MR-DOS/TDR_diploma_thesis/LaTeX/images/cml_output-eps-converted-to.pdf

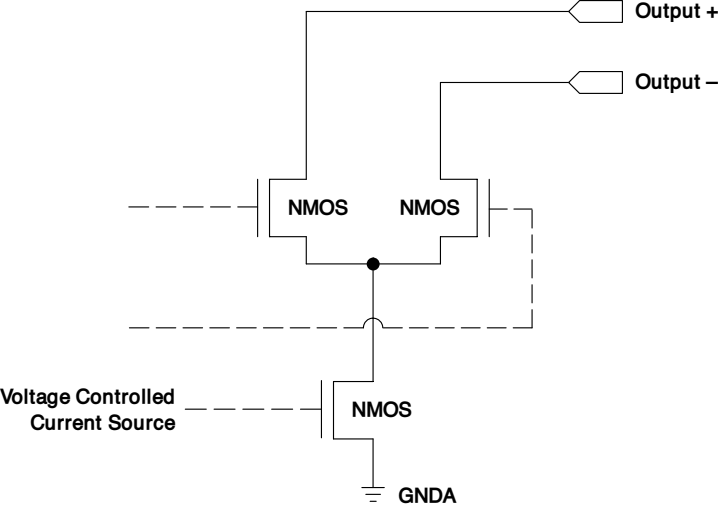
[picture p11: figure]
GNDA; NMOS; Output –; Voltage Controlled Current Source; Output +
