MR-DOS/TDR_diploma_thesis/LaTeX/diplomovy_projekt_4_separace.tex

\chapter{Separace budicího a odraženého signálu}
Pro potřeby zpracování změřených dat je nezbytné separovat budicí signál od jeho odrazů. Takovou separaci je možné provádět buď hardwarově v době měření nebo až během zpracování změřených dat. Cílem je dosáhnout toho, aby byly tyto dva signály zcela oddělené (či oddělitelné při zpracování). Možné metody separace:
\begin{itemize}
	\item
	\textbf{Směrová odbočnice}\\*	
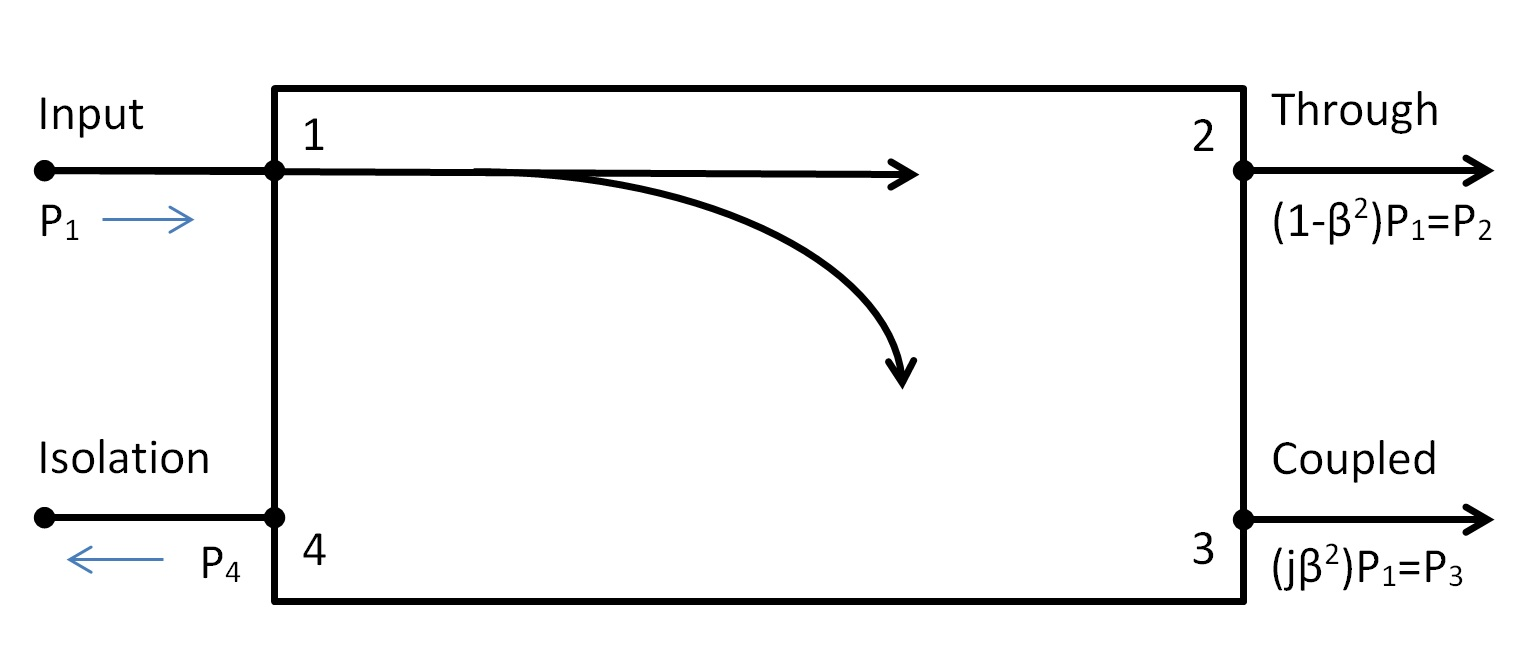
[picture p49: LaTeX/images/directionalcoupler.png]
	\begin{figure}[htbp]\caption{Směrová odbočnice, převzato z \cite{widebandcouplers}.}\label{directionalcoupler}\end{figure}	

	Pomocí tradičních odbočnic jako na obr. \ref{directionalcoupler} je možné provádět separaci s velkou izolací nechtěného signálu, ovšem nesplňují požadavek na šířku zpracovávaného pásma \cite{widebandcouplers}. Problematická je také skutečnost, že s rostoucí šířkou použitelného pásma odbočnice obvykle klesá směrovost odbočnice. Dochází tedy pouze k částečné separaci, další separační krok by byl nezbytný během zpracování naměřených dat.
	
	\item
	\textbf{Odporový můstek}\\*	
	Pomocí odporových můstků je možné provádět separaci signálů s velmi velkou šířkou pásma, např. v \cite{resistivedirectionalbridge} a obr. \ref{resistivebridge} uveden můstek pro pásmo \SI{300}{\kilo\hertz}--\SI{13.5}{\giga\hertz}. Opět je však separace budicího pulzu a odezvy pouze částečná, neboť tento můstek má konečnou směrovost.

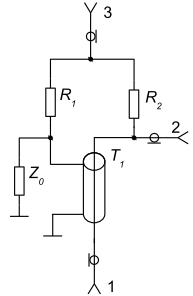
[picture p50: LaTeX/images/resistivebridge.png]
	\begin{figure}[htbp]\caption{Odporový směrový můstek, převzato z \cite{resistivedirectionalbridge}.}\label{resistivebridge}\end{figure}	
	
	\item
	\textbf{Časové oddělení}\\*	
	Pokud má budicí signál tu vlastnost, že má omezenou délku, po kterou se mění a mimo ni je konstantní (vybraný jednotkový skok tuto vlastnost splňuje), je možné jej od odrazů separovat tak, že je časově posunut vůči odezvě systému. Toho je možné dosáhnout například použitím dokonalého vedení bez odrazů, které se zapojí mezi bod měření a měřený systém. Jeho délka musí být minimálně taková, aby se nemohla nikdy překrývat nekonstantní část budicího signálu s odrazy. Pokud je v naměřených datech známá poloha budicího pulzu (nebo je-li možné jej spolehlivě identifikovat), je možné naměřená data rozdělit na část buzení a část odpovědi měřeného systému. První část pak může sloužit ke korekci frekvenční charakteristiky změřené odezvy systému a odhadu šumového spektra. Známe-li i přesnou délku prodlužovacího vedení (hrubě z návrhu zařízení, přesně pomocí kalibrace), je možné provést kalibraci měřicí roviny. Při použití této metody separace stačí vzorkování pouze jednoho průběhu, snižuje tedy počet potřebných vzorkovačů ze dvou (nebo více) na jeden. Z toho také vyplývá, že měřená data nejsou zatížena chybou, která by mohla vzniknout vzhledem k rozdílným vlastnostem jednotlivých vzorkovačů.
	
	Na obrázku \ref{separableunitstep} je znázorněna odezva na chybovou funkci pro \SI{50}{\ohm} zakončené \SI{75}{\ohm} terminátorem. Buzení se nachází v čase $t=\SI{0}{\nano\second}$, odezva v čase $t=\SI{0.5}{\nano\second}$. Průběh budicí funkce je předem známý, nekonstantní část průběhu se nepřekrývá s odezvou, je tedy možné je v časové oblasti $t\in (\SI{0}{\nano\second};\SI{0.5}{\nano\second})$ rozdělit na dva samostatné průběhy.

\begin{figure}[htbp]\caption{Časově oddělitelná odezva na jednotkový skok.}\label{separableunitstep}\end{figure}	
\end{itemize}

Pro vybraný budicí signál (jednotkový skok) je tedy možné provést separaci od odrazů zpožďovacím vedením a vhodným rozdělením naměřených dat na dvě části. Toto řešení se jeví jako obvodově i výpočetně nejjednodušší z uvažovaných metod separace.
