MR-DOS/TDR_diploma_thesis/obhajoba/obhajoba_prezentace_oponent.odp

## Diplomová práce Reflektometr v časové oblasti

ČVUT FEL EK, Elektronika

Petr Polášek

2020-02-01

## Slide 2

Odpovědi na dotazy oponenta

## Slide 3

## Slide 4

## Slide 5

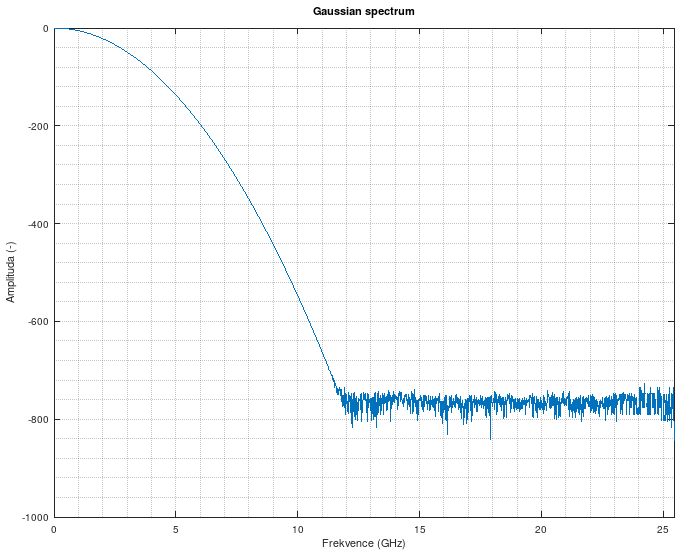
[picture p51: figure]

## Slide 6

## Slide 7

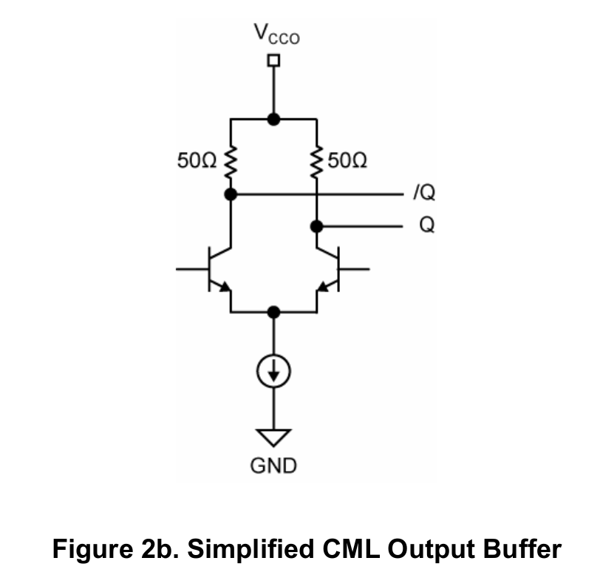
[picture p52: figure]

## Slide 8

+1.6 mW

(+0.8 mW)

+1.6 mW

(+0.8 mW)

## Slide 9

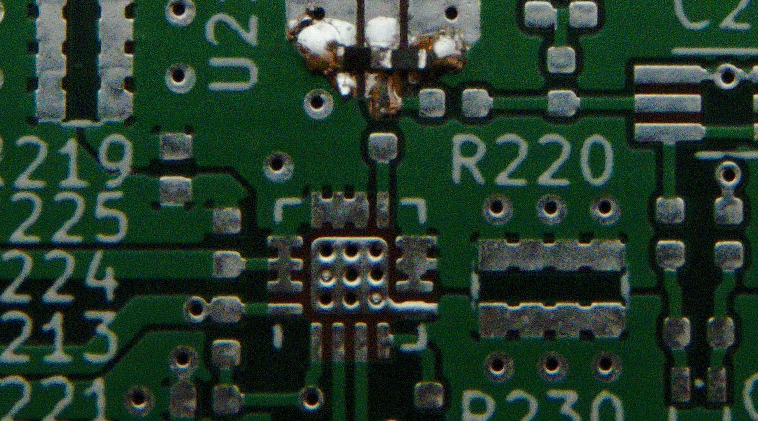
[picture p53: figure]

## Slide 10

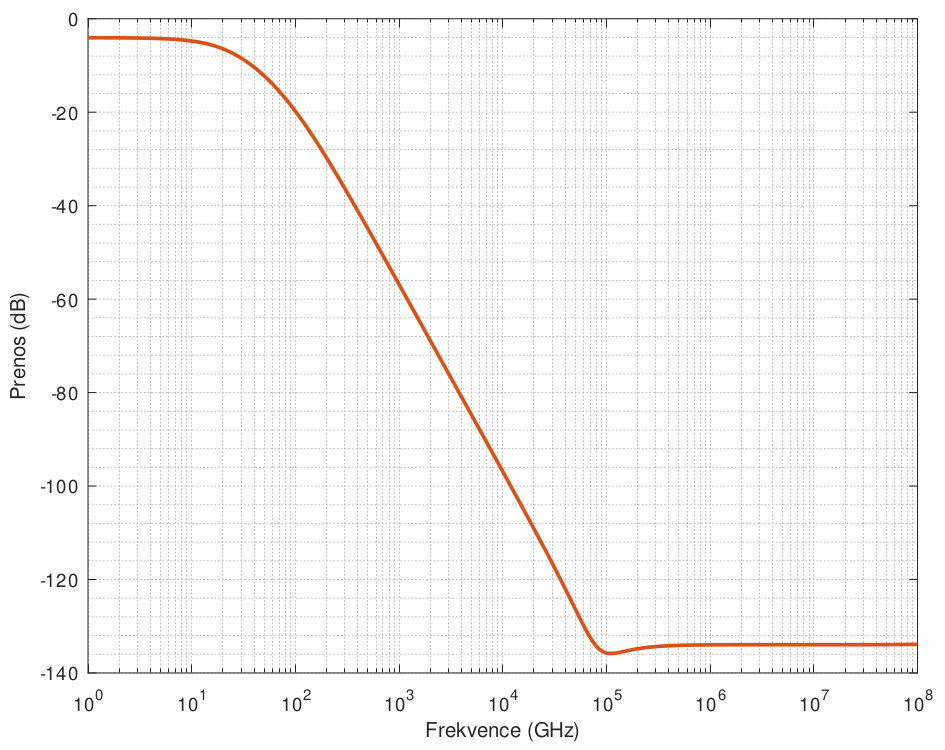
[picture p54: figure]

## Slide 11

## Slide 12

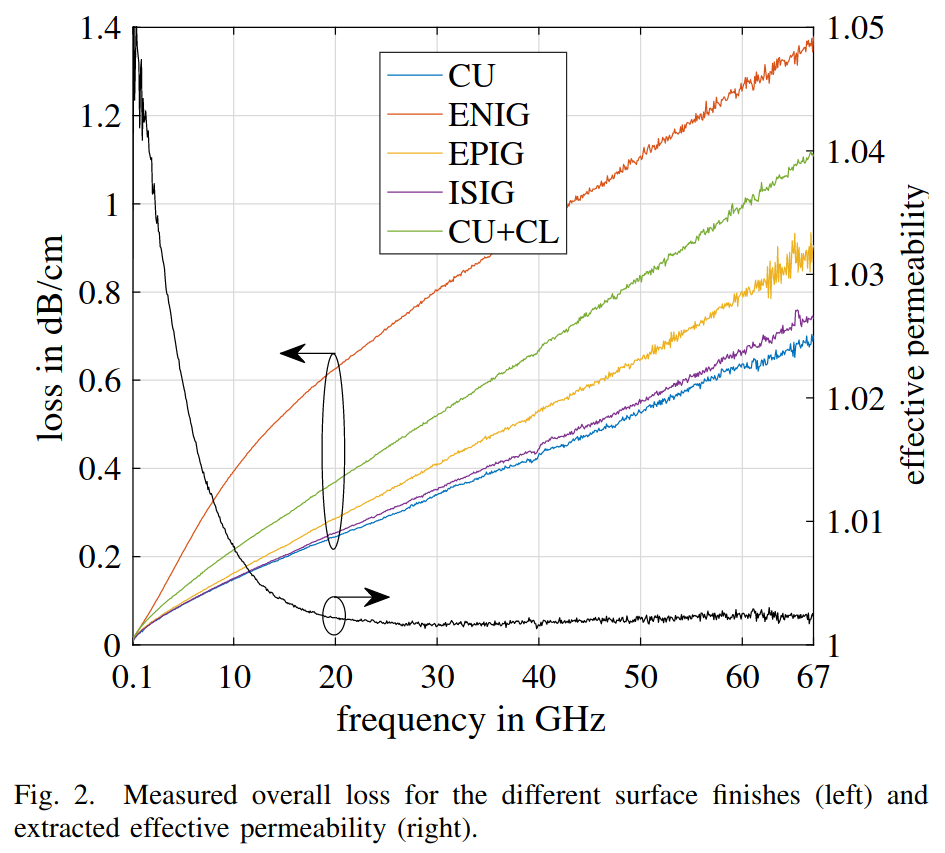
[picture p55: figure]

## Slide 13

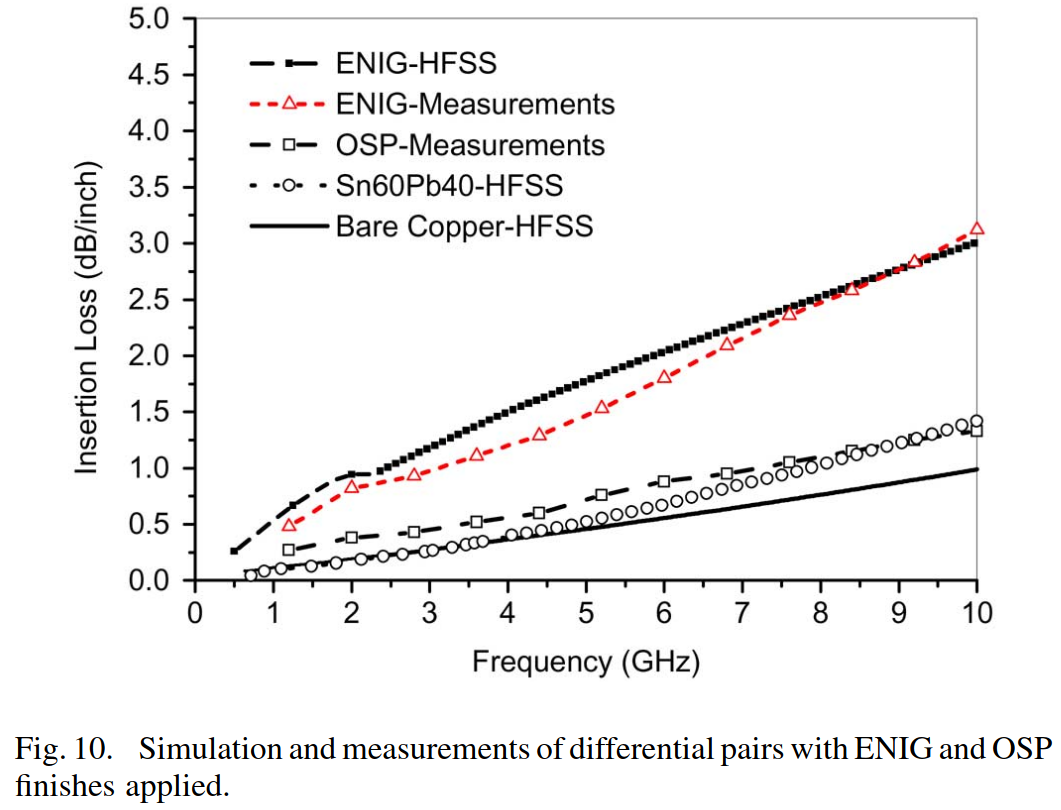
[picture p56: figure]

## Slide 14

## Slide 15

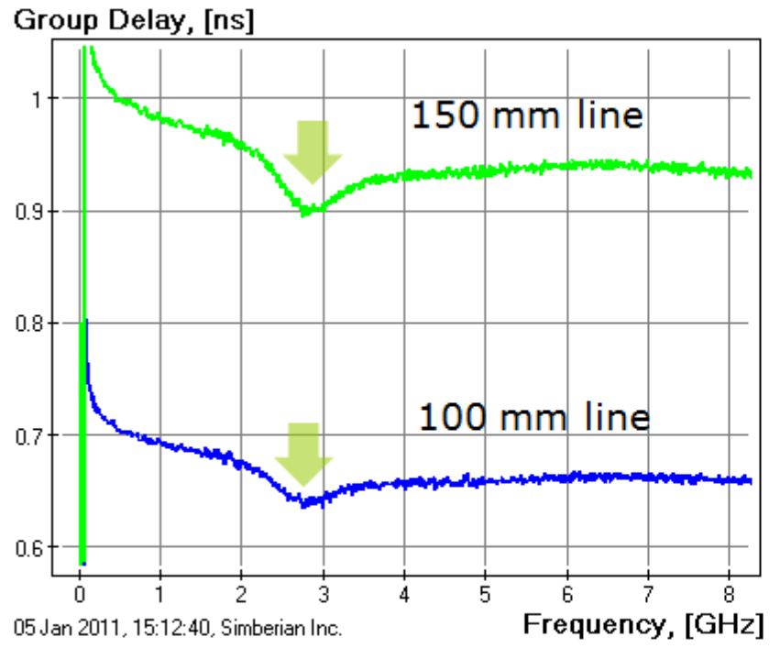
[picture p57: figure]
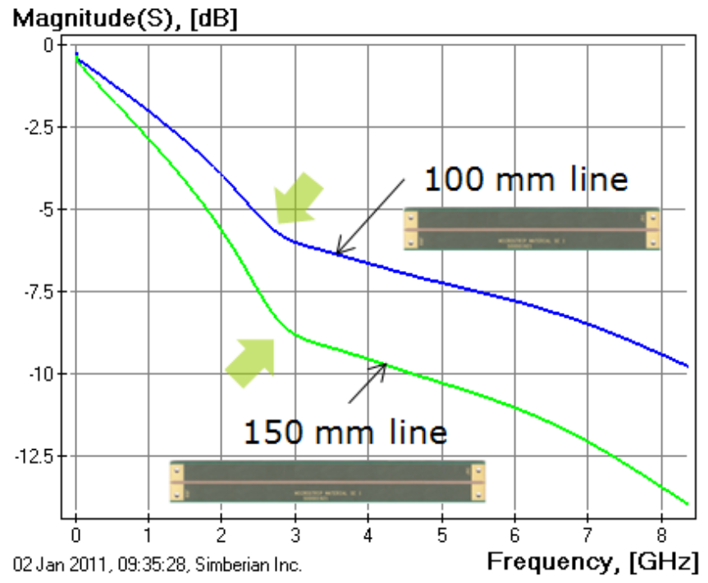
[picture p58: figure]

## Slide 16

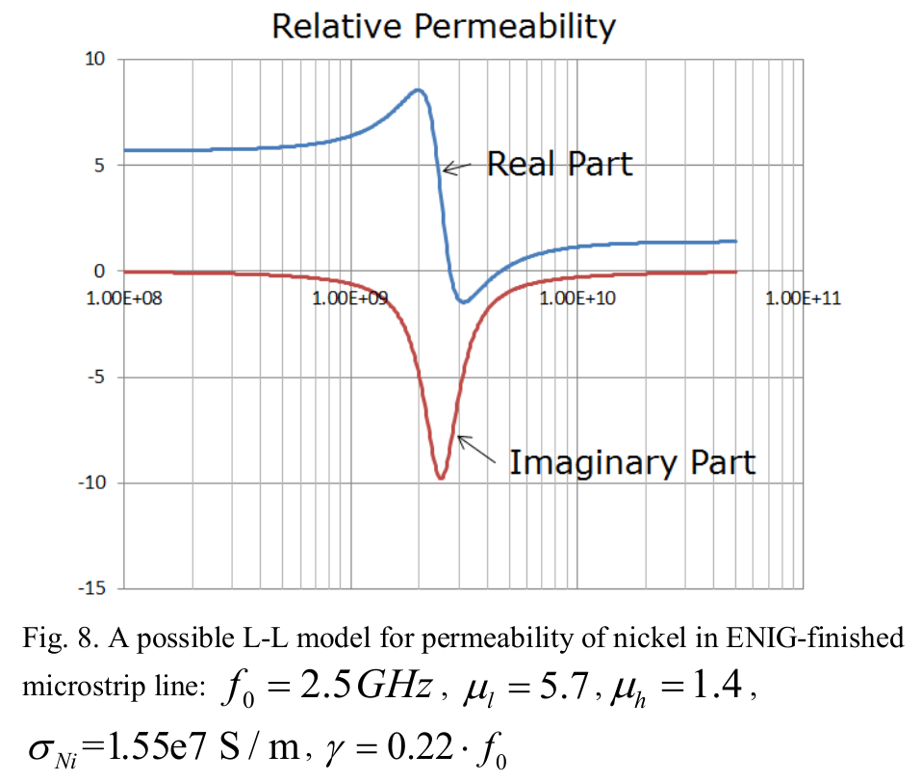
[picture p59: figure]
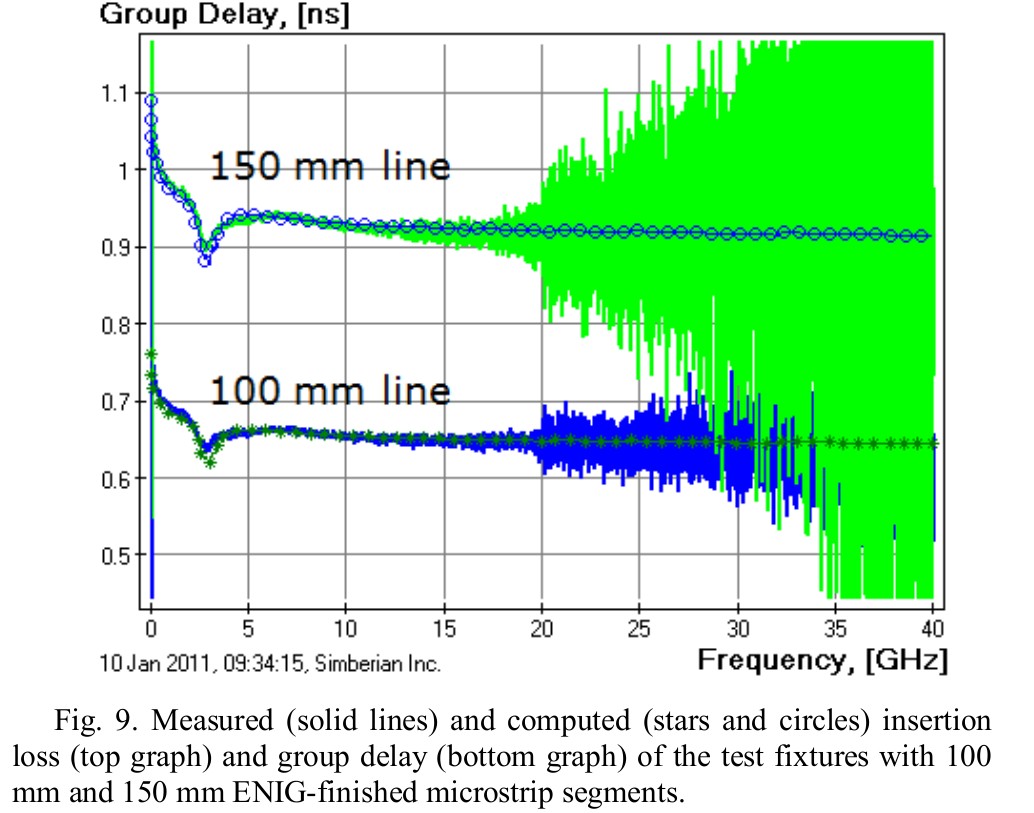
[picture p60: figure]

## Slide 17

## Slide 18

## Slide 19


## Slide 20

## Slide 21

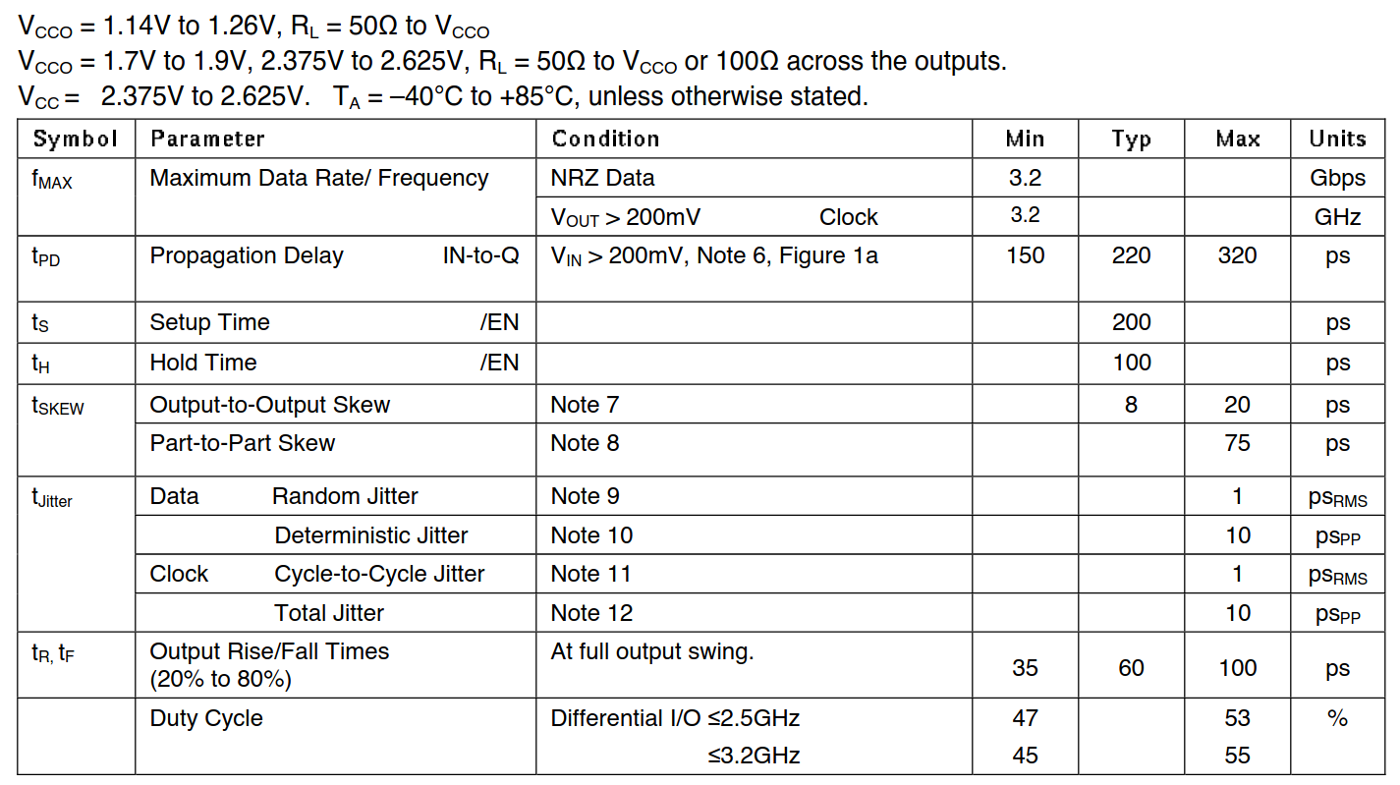
[picture p61: figure]

## Slide 22

## Slide 23

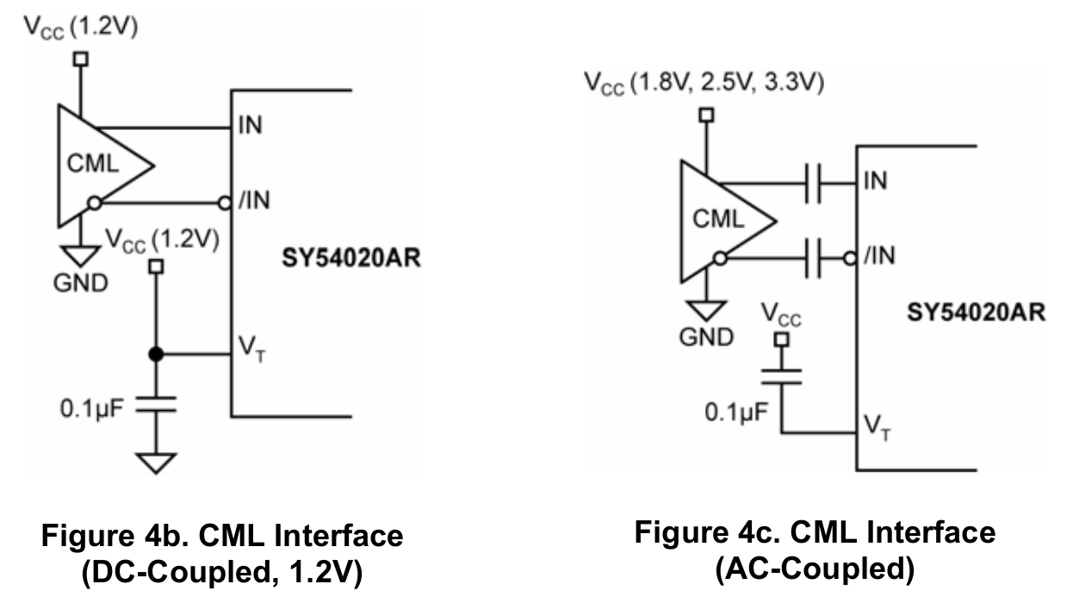
[picture p62: figure]

## Slide 24

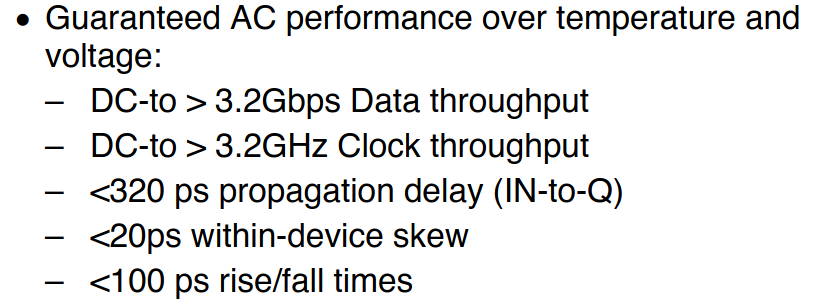
[picture p63: figure]

## Slide 25

## Slide 26

## Slide 27

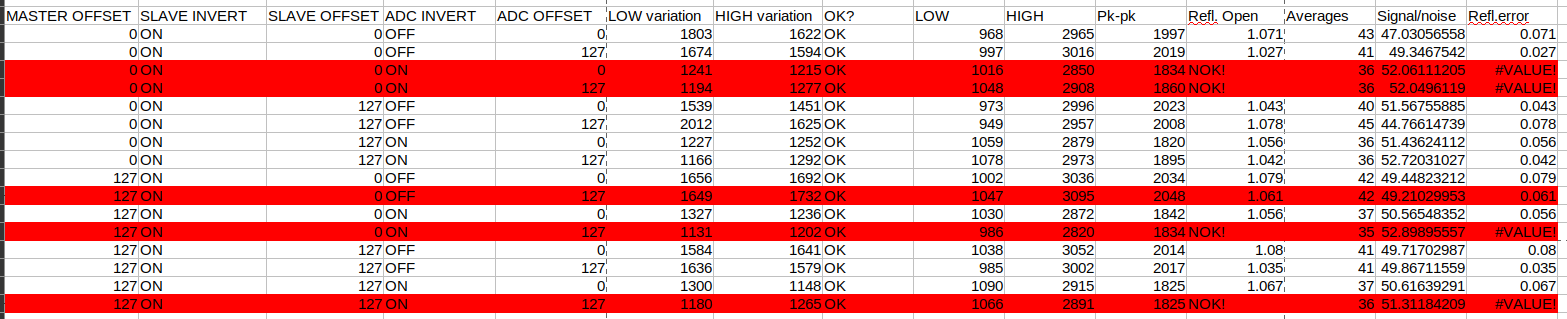
[picture p64: figure]

## Slide 28

## Slide 29

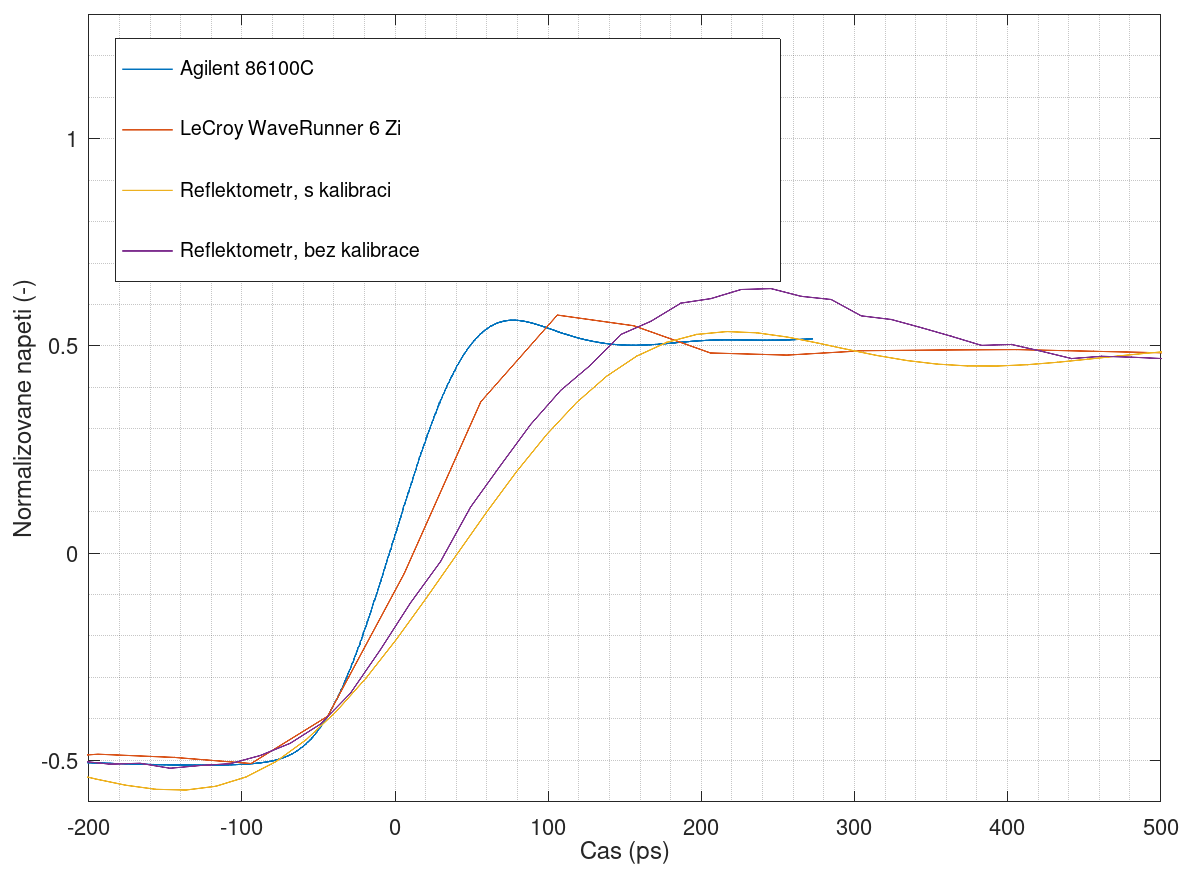
[picture p65: figure]

## Slide 30

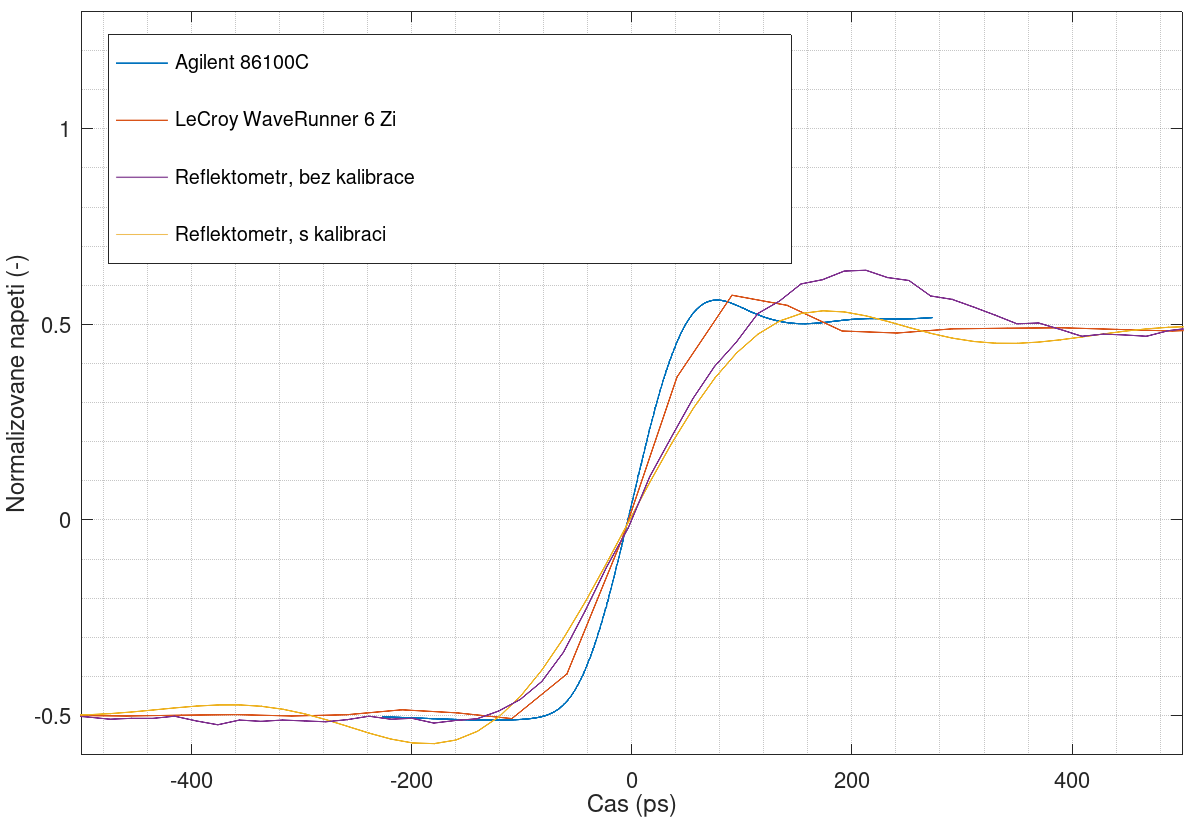
[picture p66: figure]

## Slide 31

## Slide 32

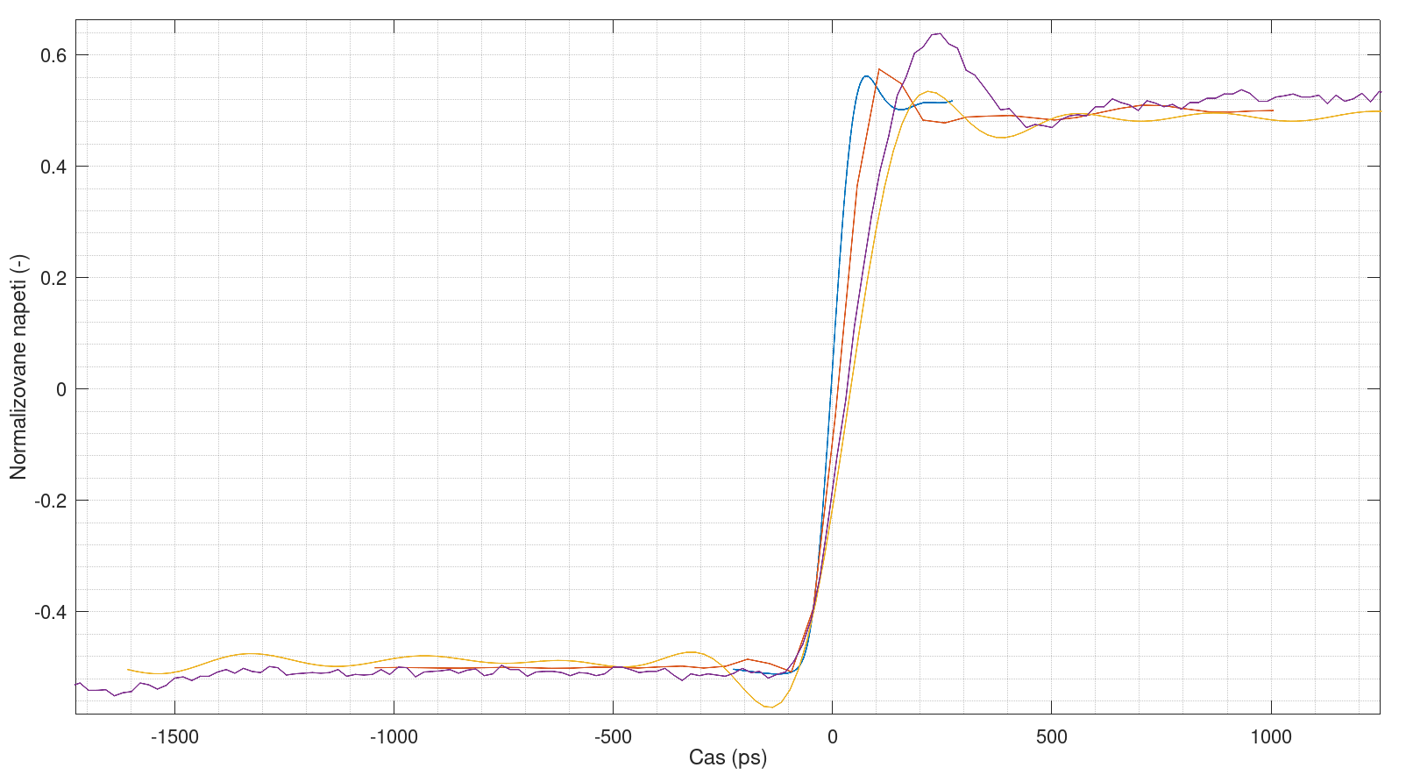
[picture p67: figure]

## Slide 33

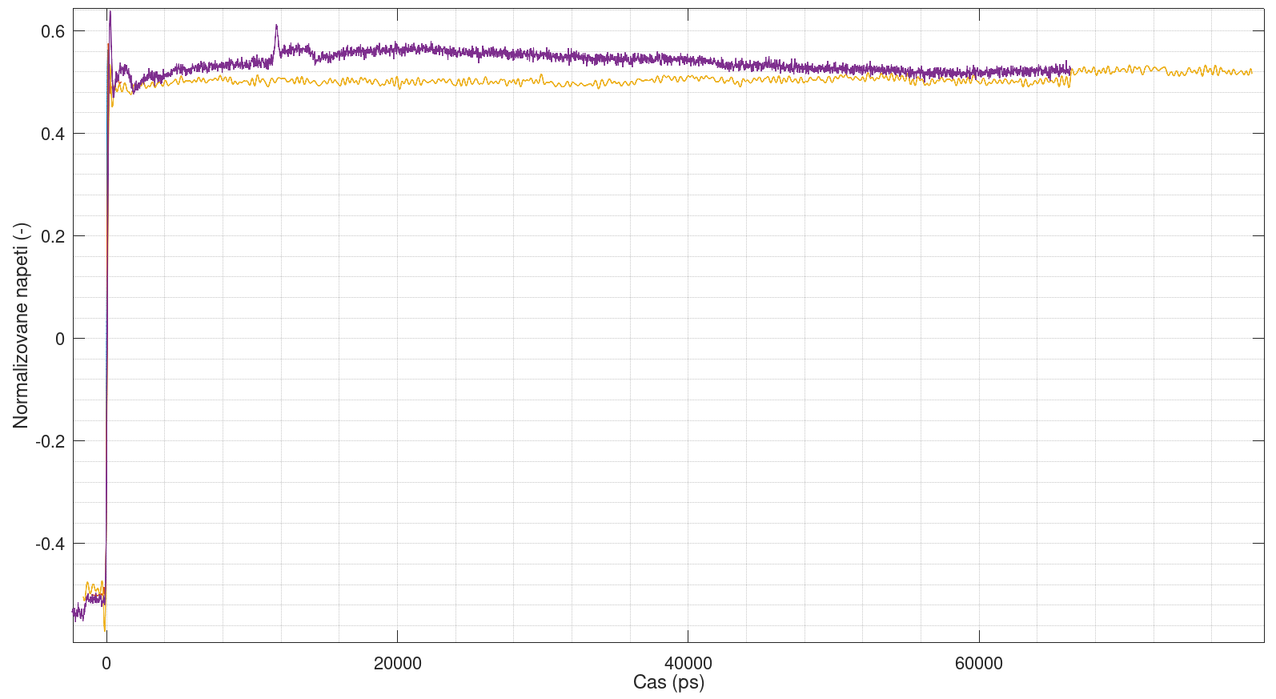
[picture p68: figure]

## Slide 34

## Slide 35

## Slide 36

5,2 mm

0,63 mm

## Slide 37

## Slide 38

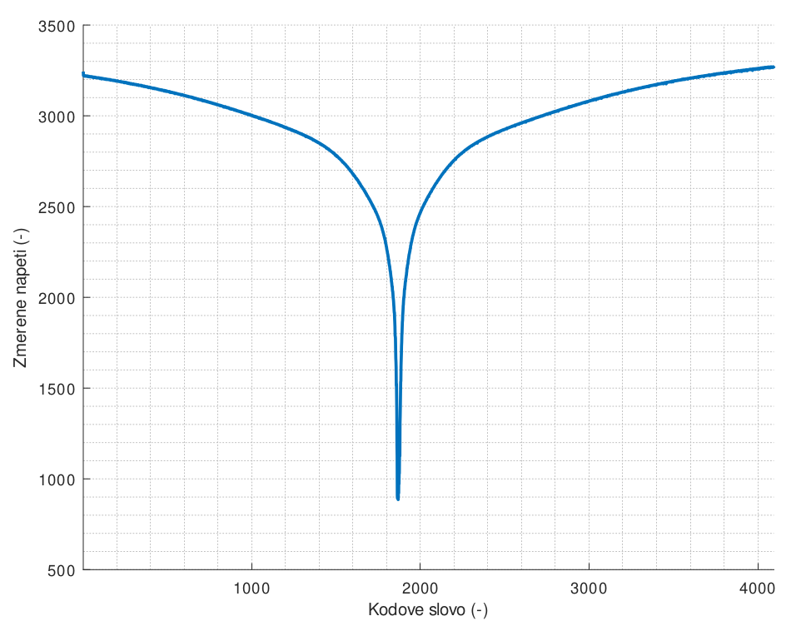
[picture p69: figure]

## Slide 39

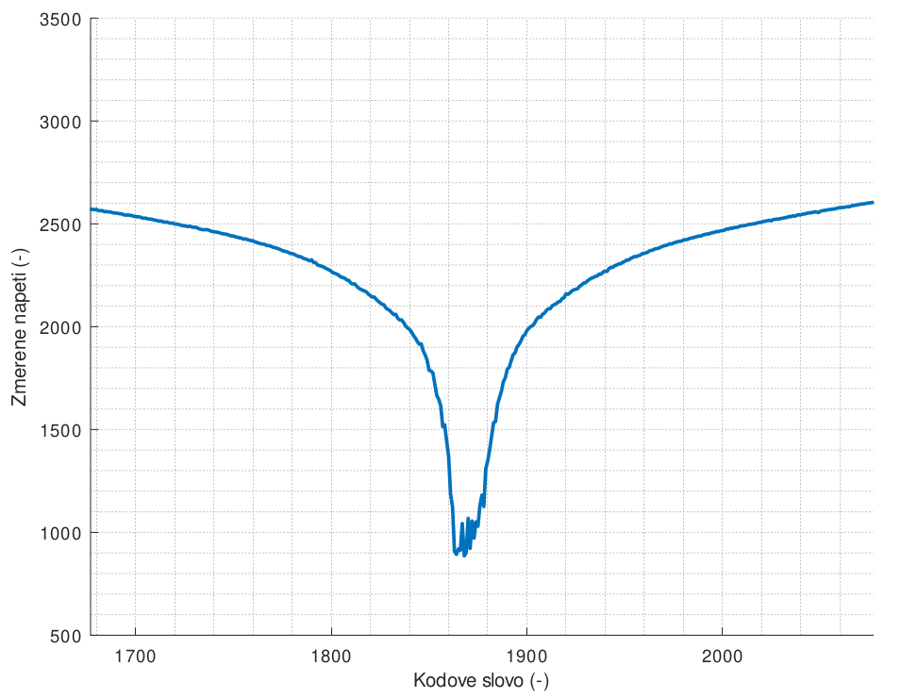
[picture p70: figure]

## Slide 40

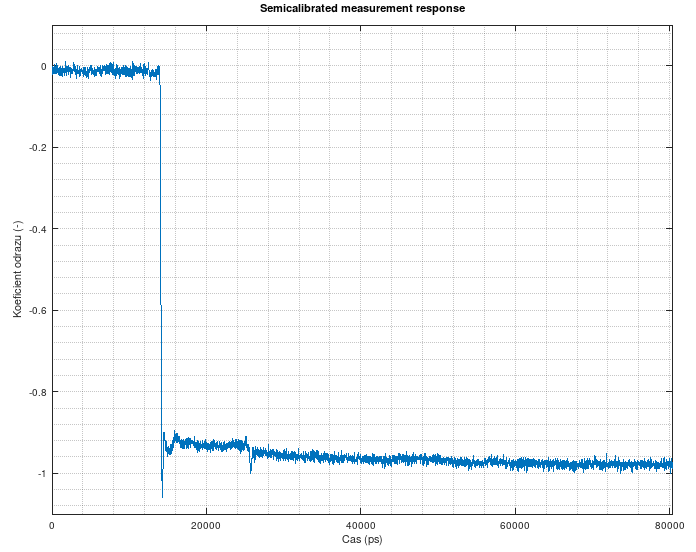
[picture p71: figure]

## Slide 41

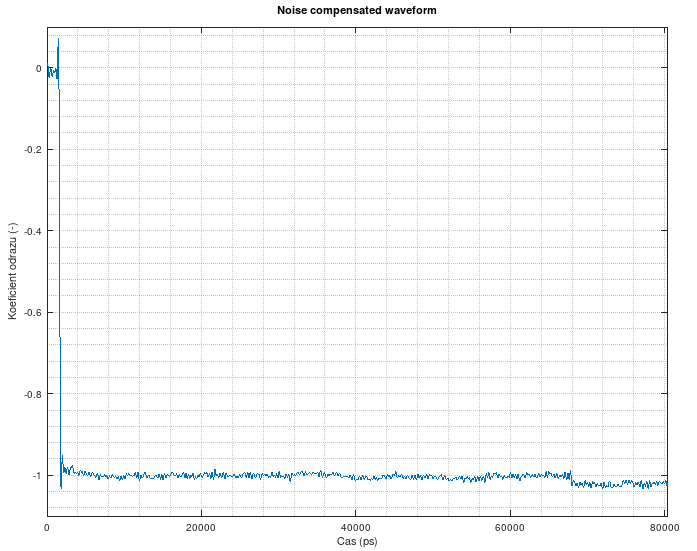
[picture p72: figure]

## Slide 42

## Slide 43

## Slide 44

## Slide 45

## Slide 46

## Slide 47

## Diplomová práce Reflektometr v časové oblasti

ČVUT FEL EK, Elektronika

Petr Polášek

2020-02-01
