MR-DOS/TDR_diploma_thesis/obhajoba/obhajoba_prezentace_oponent_flat_min.odp

## Diplomová práce Reflektometr v časové oblasti

ČVUT FEL EK, Elektronika

Petr Polášek

2020-02-01

## Slide 2

Odpovědi na dotazy oponenta

## Slide 3

## Slide 4

## Slide 5

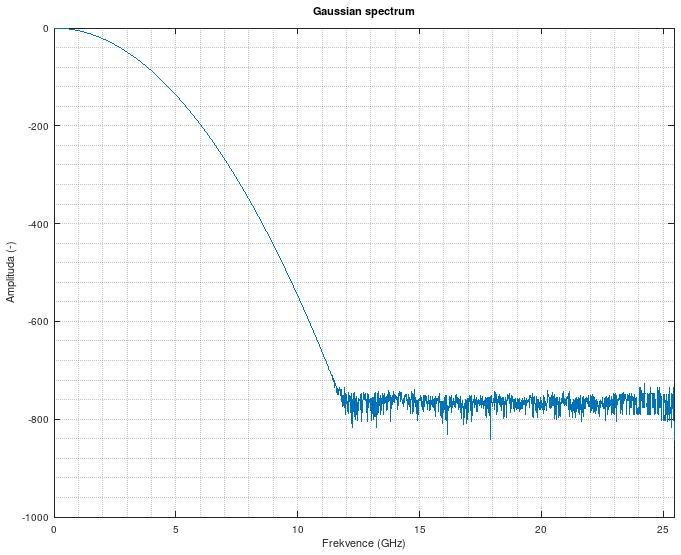
[picture p73: figure]

## Slide 6

## Slide 7

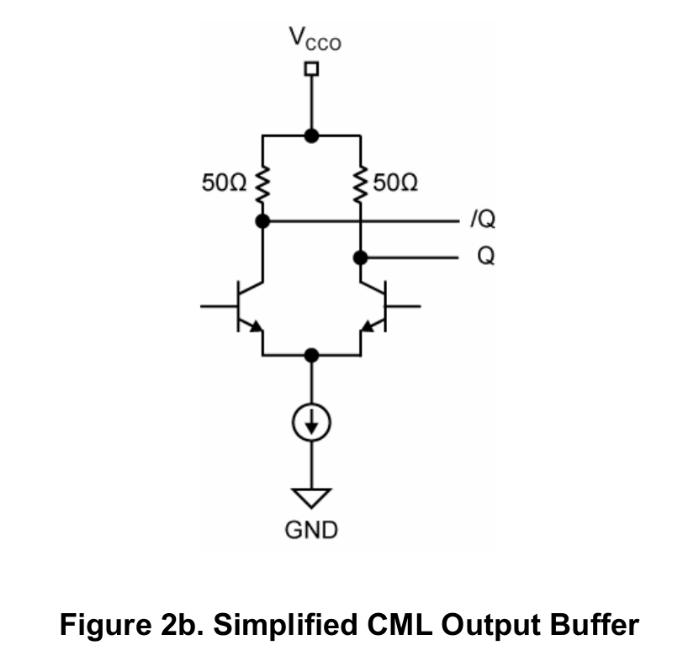
[picture p74: figure]

## Slide 8

+1.6 mW

(+0.8 mW)

+1.6 mW

(+0.8 mW)

## Slide 9

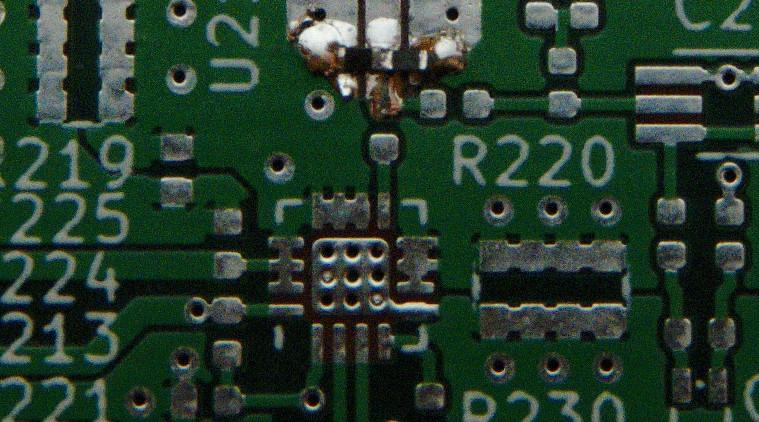
[picture p75: figure]

## Slide 10

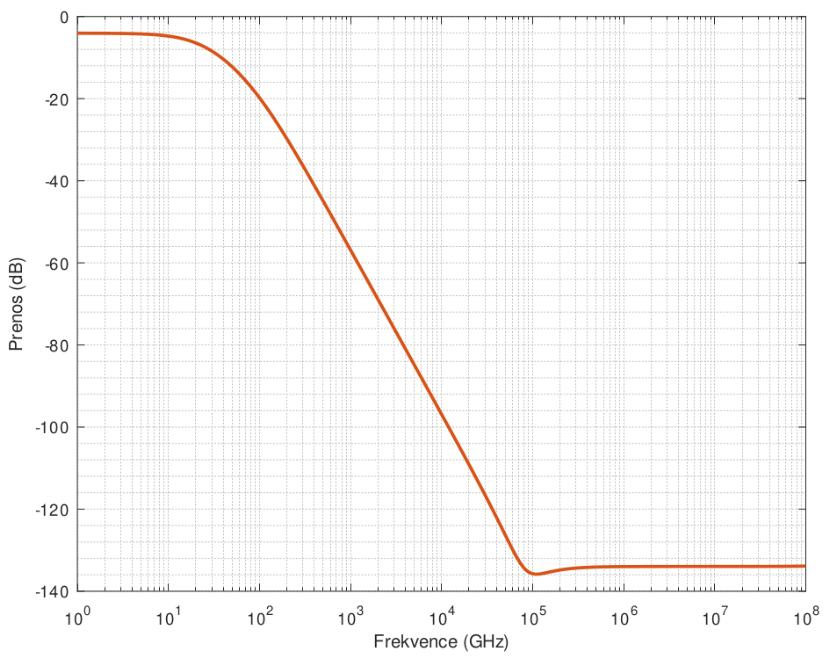
[picture p76: figure]

## Slide 11

## Slide 12

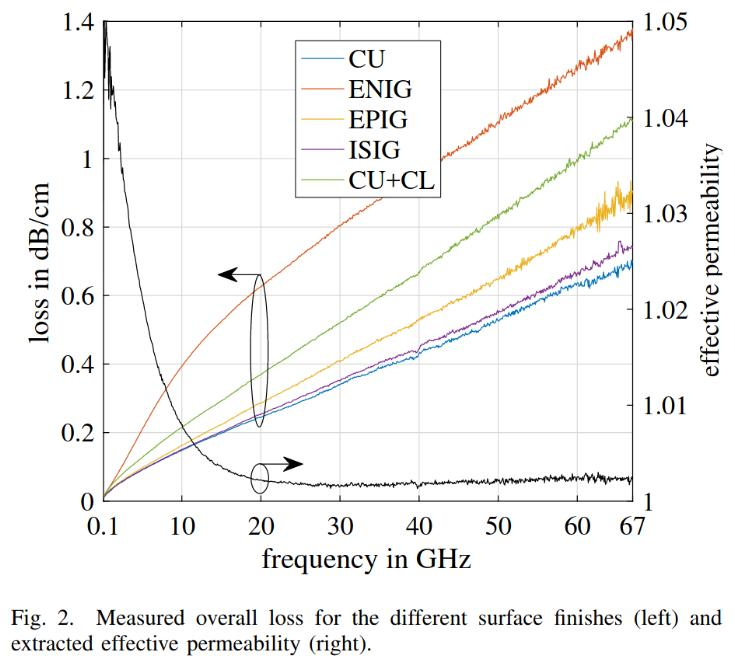
[picture p77: figure]

## Slide 13

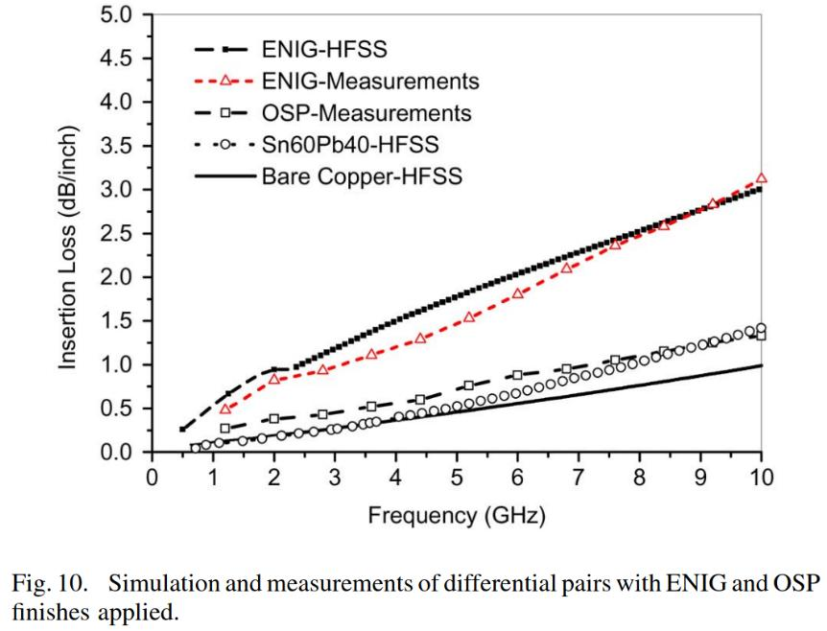
[picture p78: figure]

## Slide 14

## Slide 15

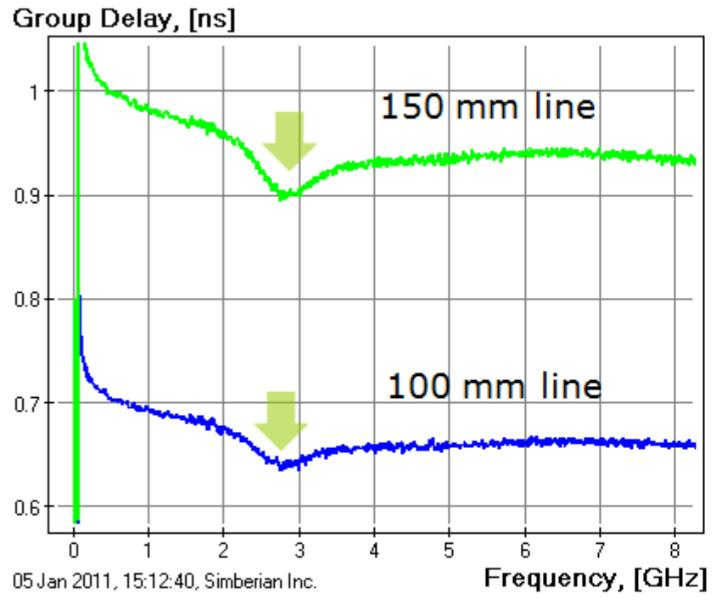
[picture p79: figure]
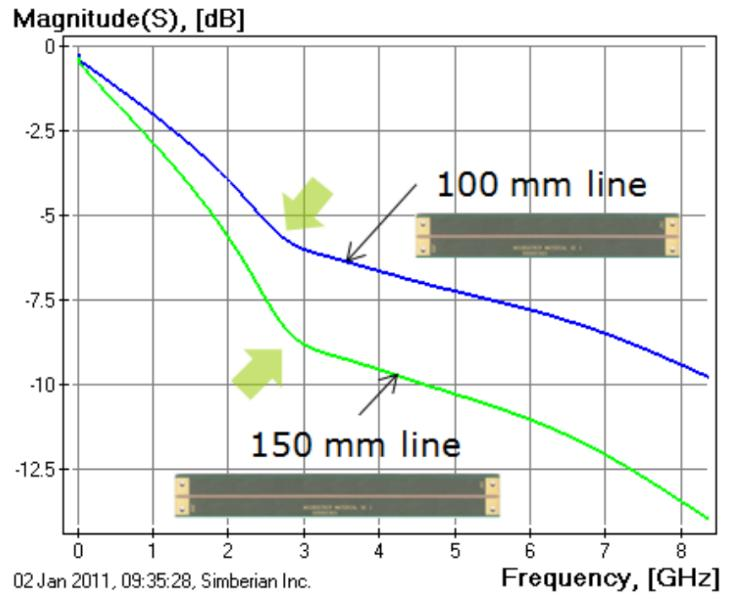
[picture p80: figure]

## Slide 16

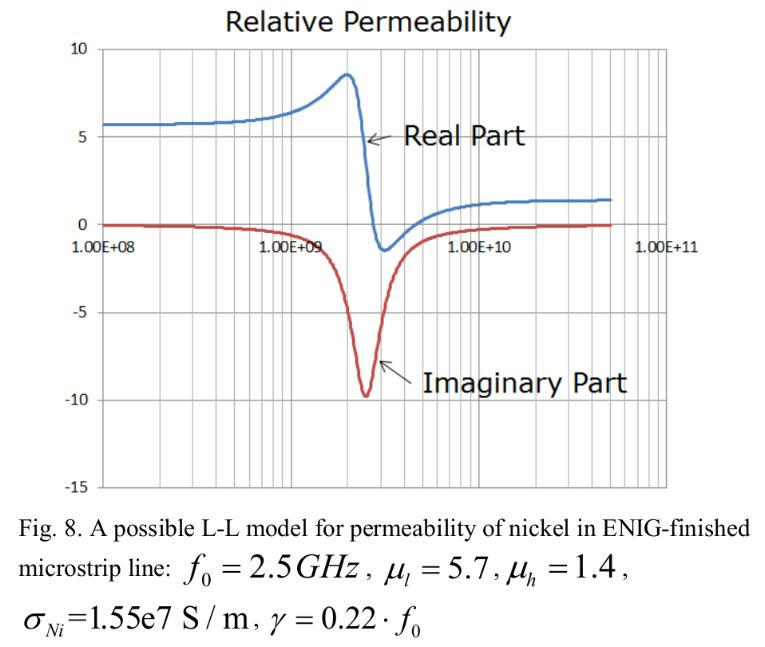
[picture p81: figure]
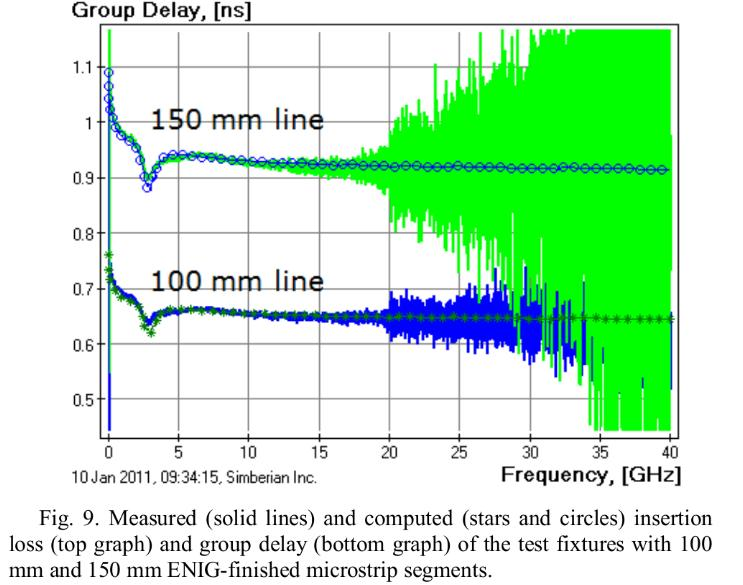
[picture p82: figure]

## Slide 17

## Slide 18

## Slide 19

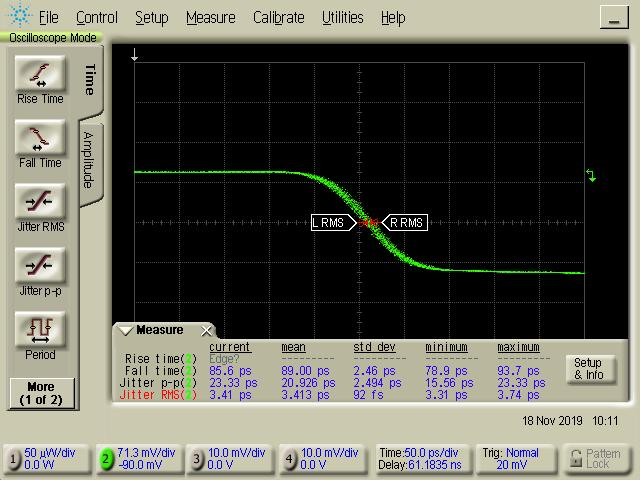
[picture p83: figure]

## Slide 20

## Slide 21

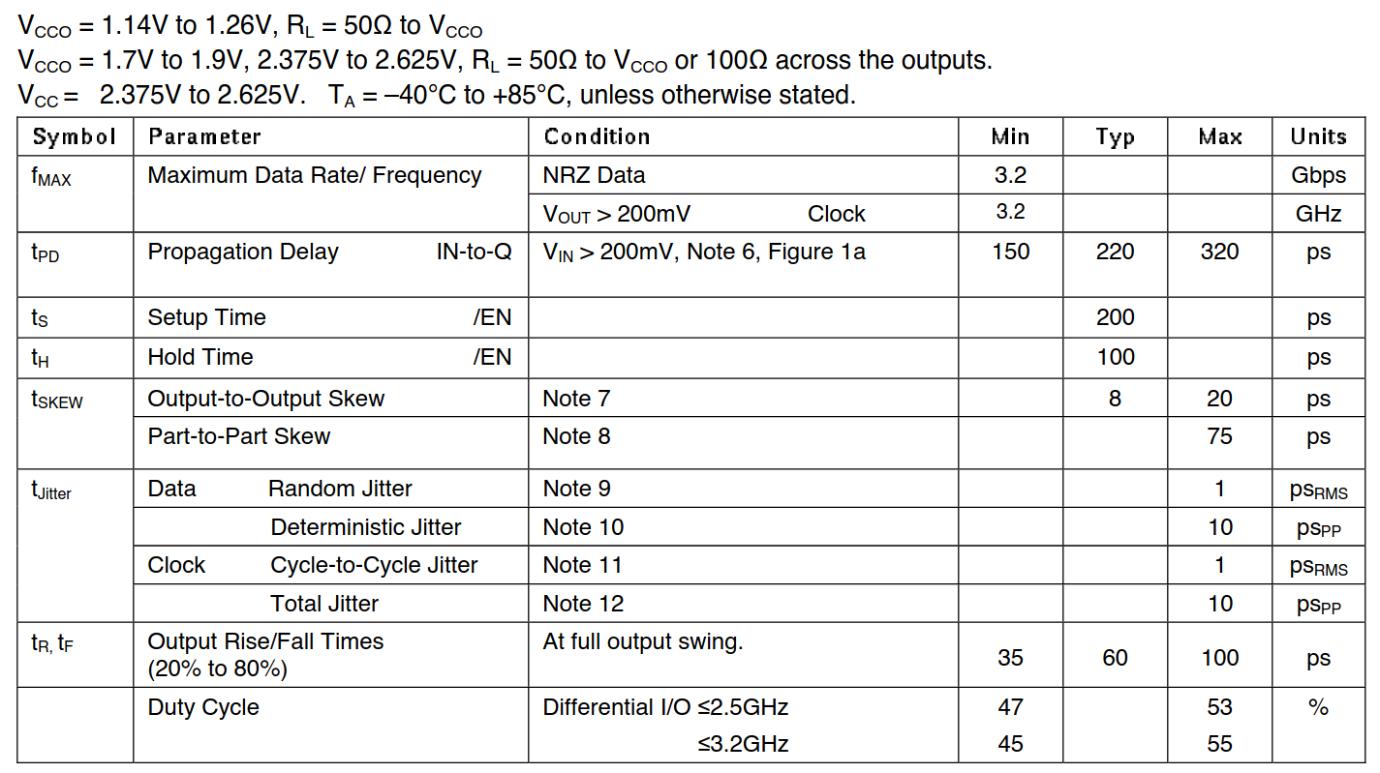
[picture p84: figure]

## Slide 22

## Slide 23

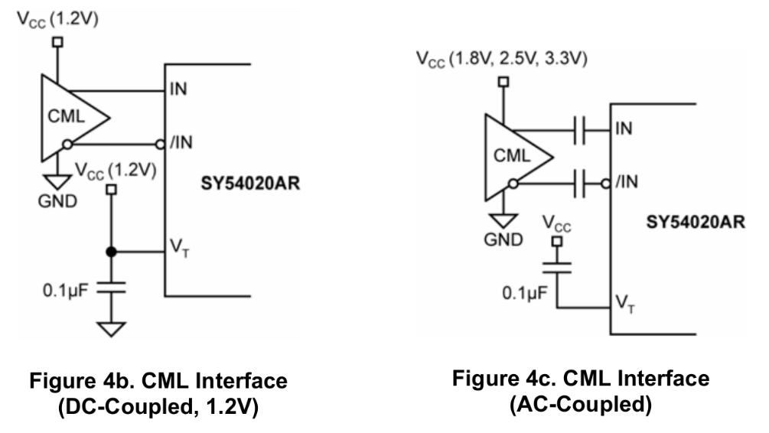
[picture p85: figure]

## Slide 24

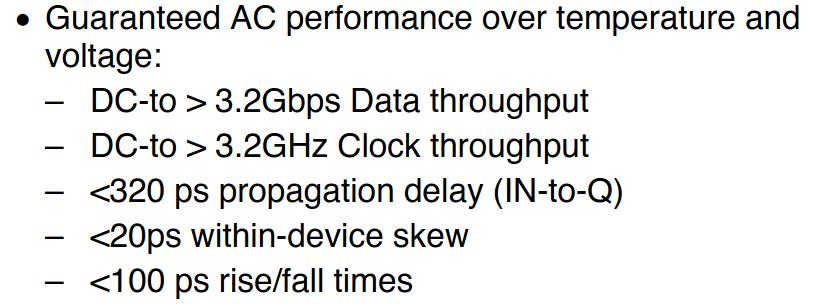
[picture p86: figure]

## Slide 25

## Slide 26

## Slide 27

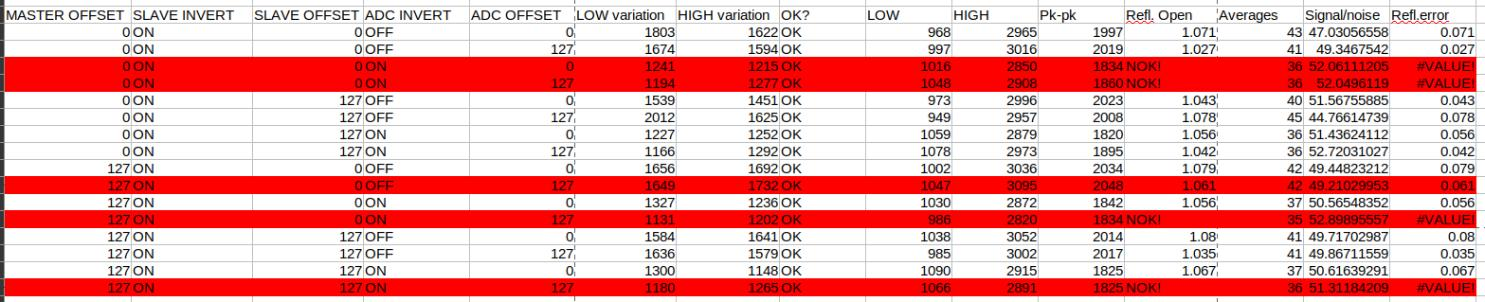
[picture p87: figure]

## Slide 28

## Slide 29

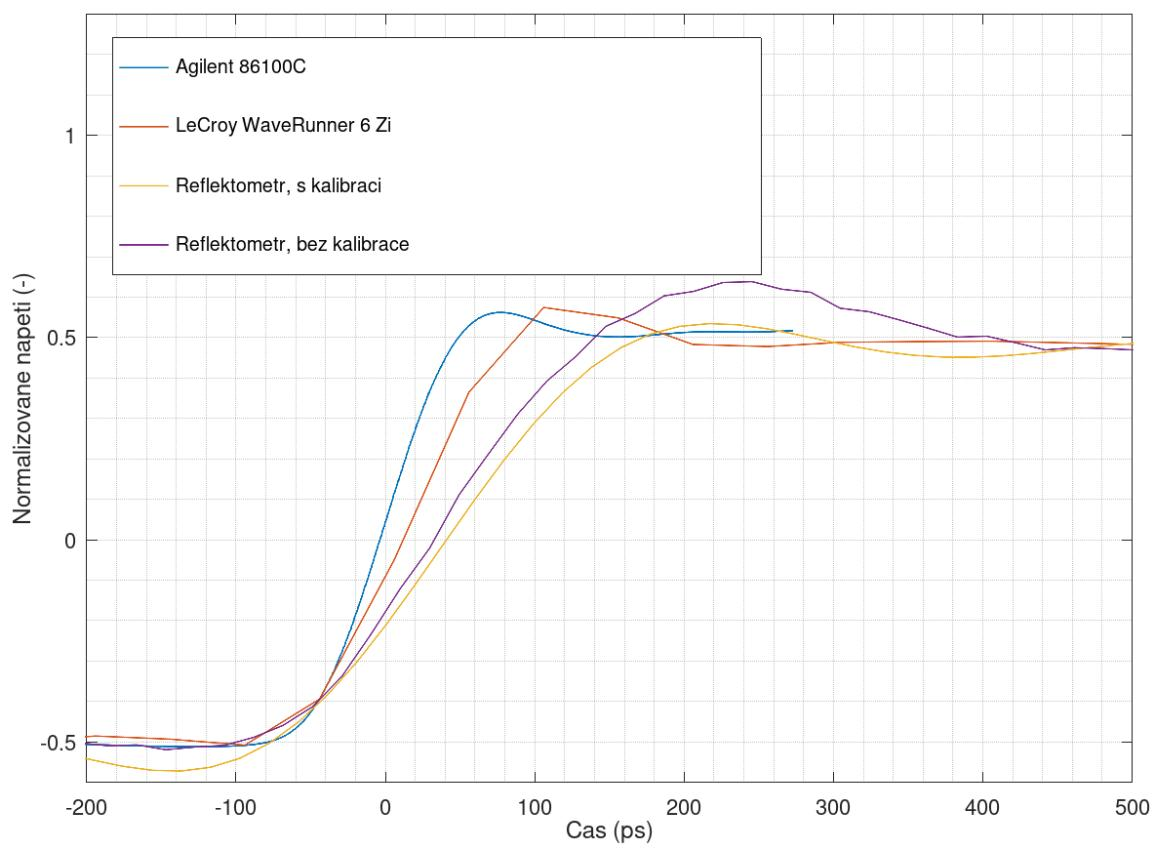
[picture p88: figure]

## Slide 30


## Slide 31

## Slide 32

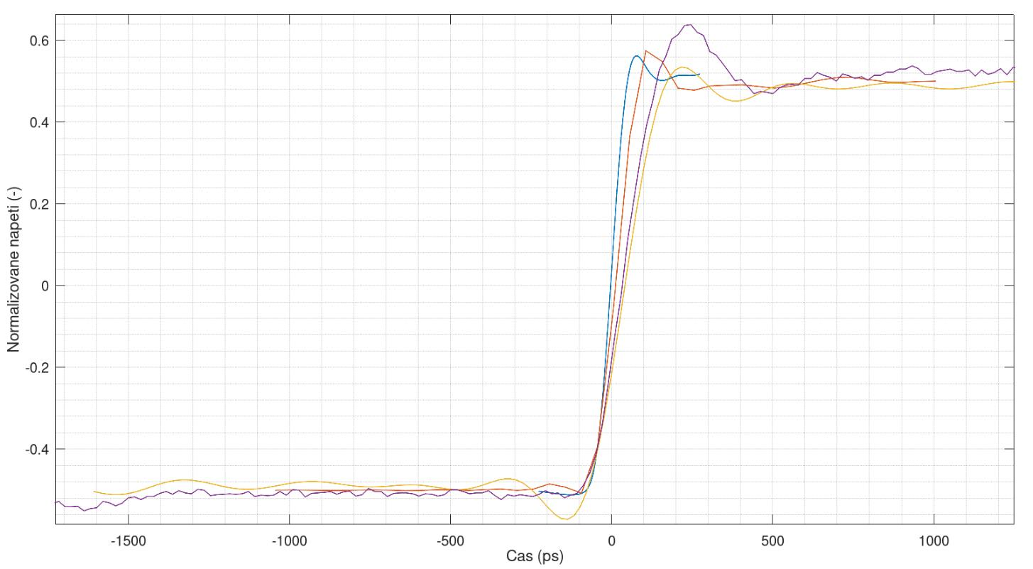
[picture p89: figure]

## Slide 33

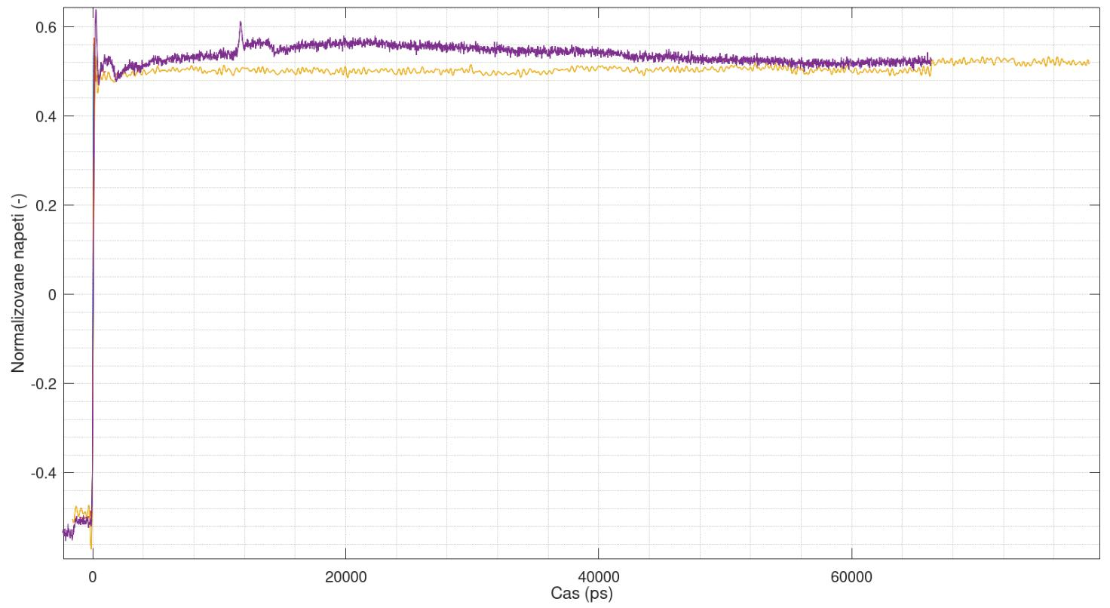
[picture p90: figure]

## Slide 34

## Slide 35

## Slide 36

5,2 mm

0,63 mm

## Slide 37

## Slide 38

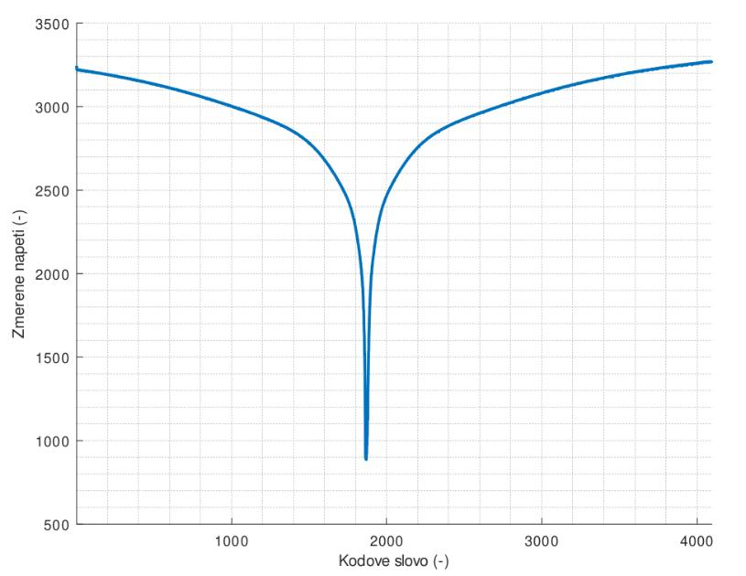
[picture p91: figure]

## Slide 39

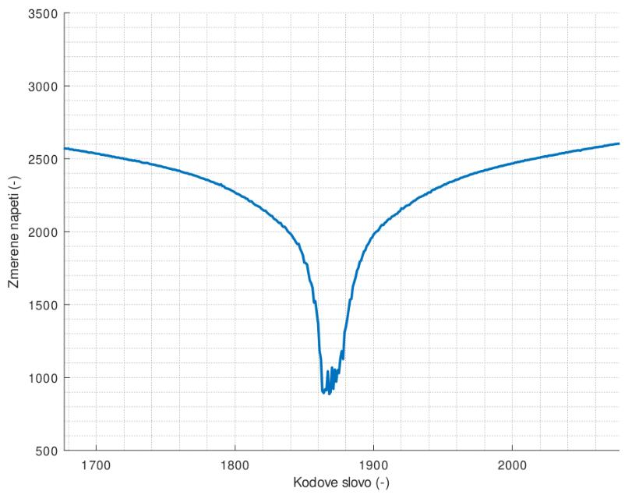
[picture p92: figure]

## Slide 40


## Slide 41

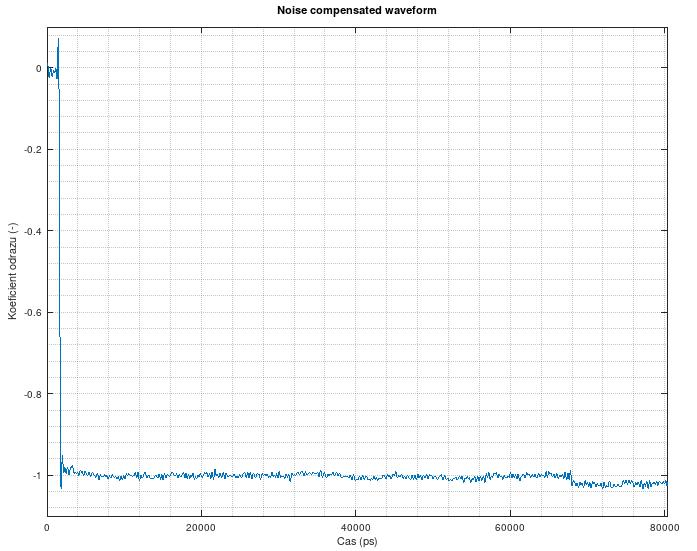
[picture p93: figure]

## Slide 42

## Slide 43

## Slide 44

## Slide 45

## Slide 46

## Slide 47

## Diplomová práce Reflektometr v časové oblasti

ČVUT FEL EK, Elektronika

Petr Polášek

2020-02-01
