MR-DOS/TDR_diploma_thesis/obhajoba/obhajoba_prezentace_prace_flat_min.odp

## Diplomová práce Reflektometr v časové oblasti

ČVUT FEL EK, Elektronika

Petr Polášek

2020-02-01

## Struktura obhajoby

Princip funkce

Navržený hardware

Firmware v zařízení

Software pro PC

SOL kalibrace

Potlačení šumu

Změřené parametry

## Slide 3

Princip funkce

## Slide 4

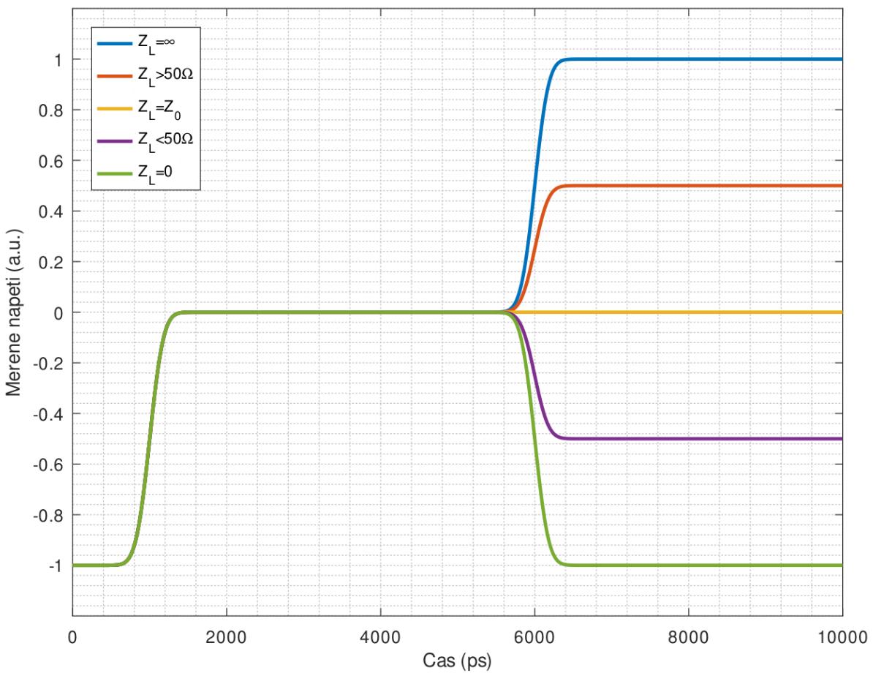
[picture p94: figure]

## Slide 5

## Slide 6

## Slide 7

## Slide 8

## Slide 9

## Slide 10

## Slide 11

## Slide 12

Navržený hardware

## Slide 13

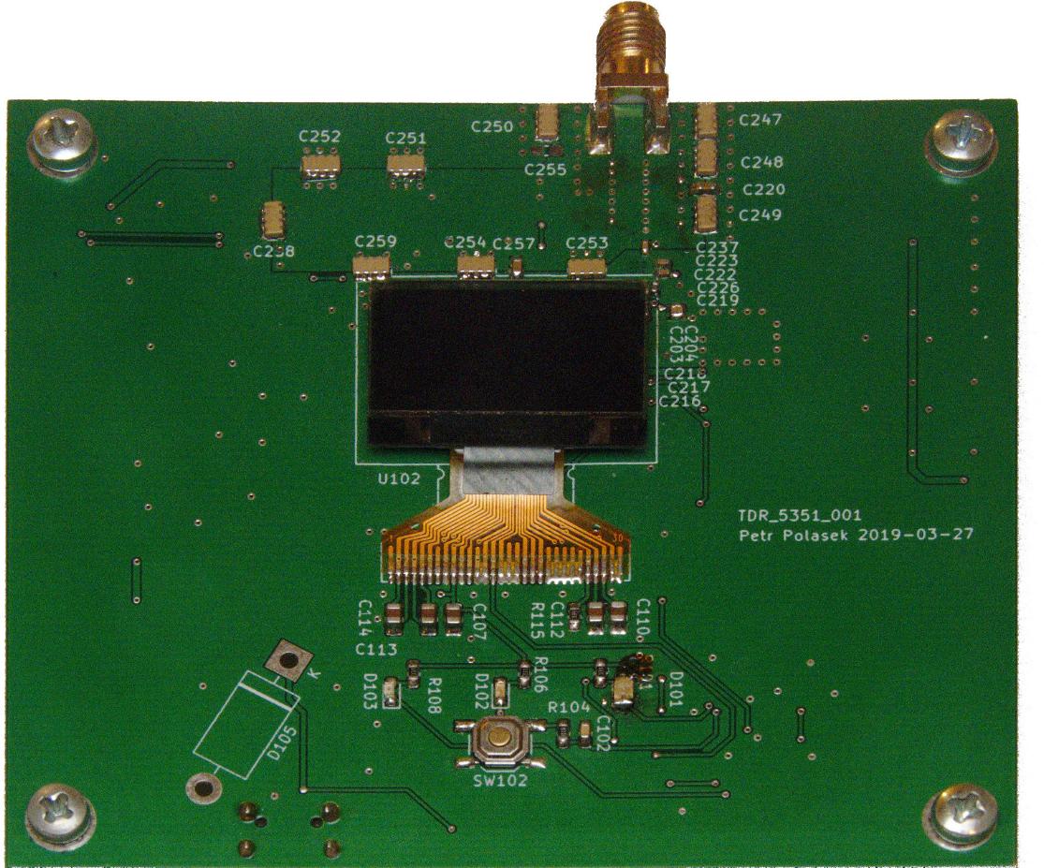
[picture p95: figure]

## Slide 14

## Slide 15

## Slide 16

## Slide 17

## Slide 18

## Slide 19

## Slide 20

## Slide 21

## Slide 22

## Slide 23

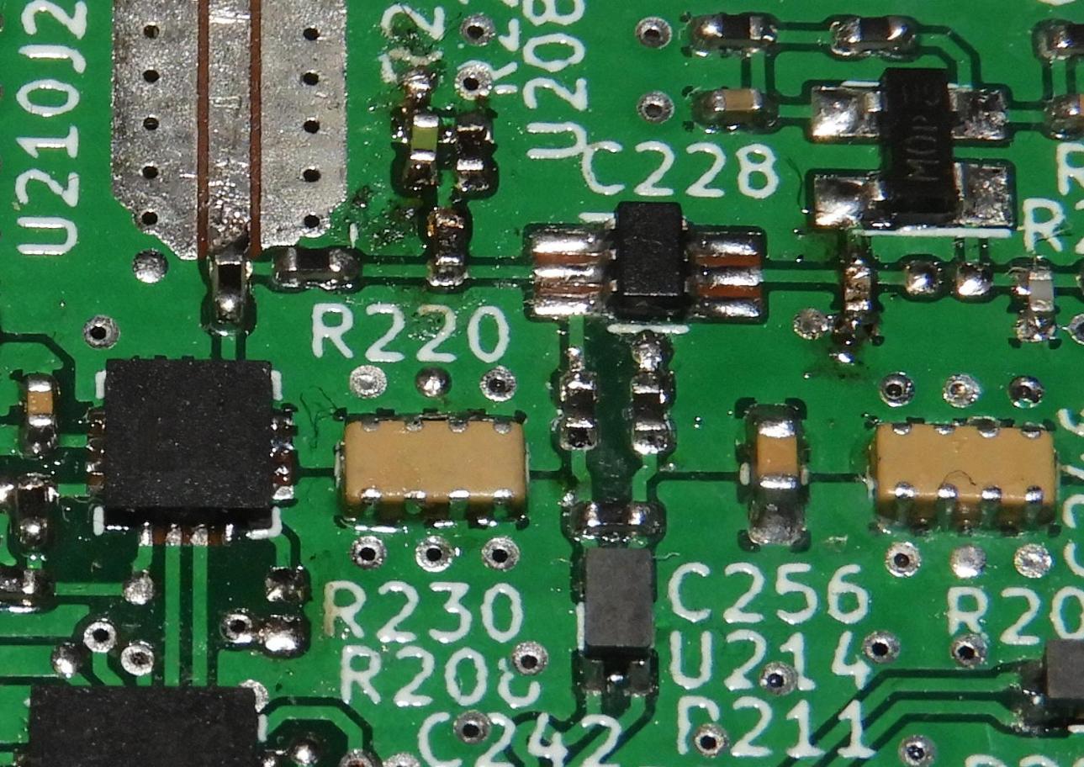
[picture p96: figure]

## Slide 24

## Slide 25

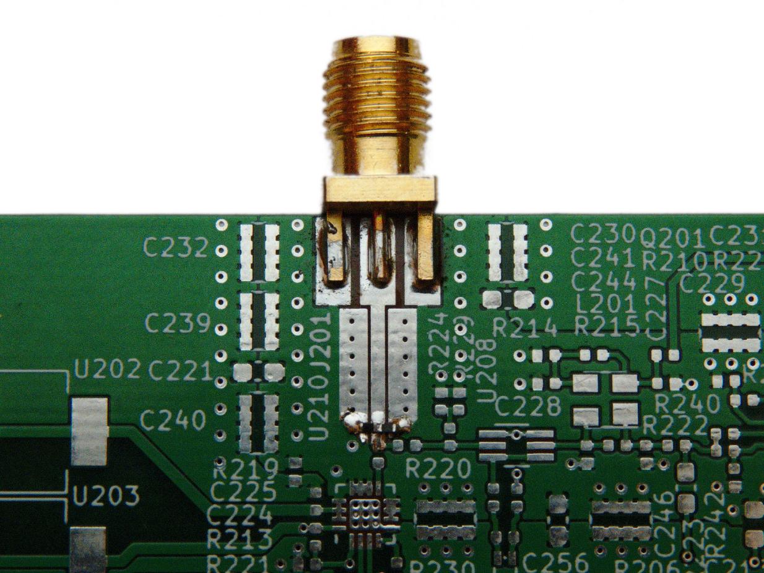
[picture p97: figure]

## Slide 26

Firmware v zařízení

## Slide 27

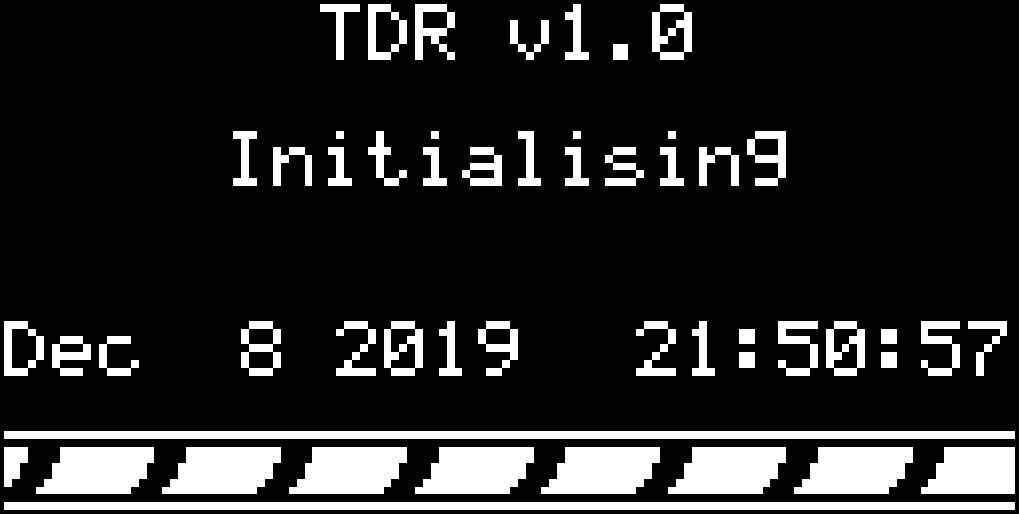
[picture p98: figure]

## Slide 28

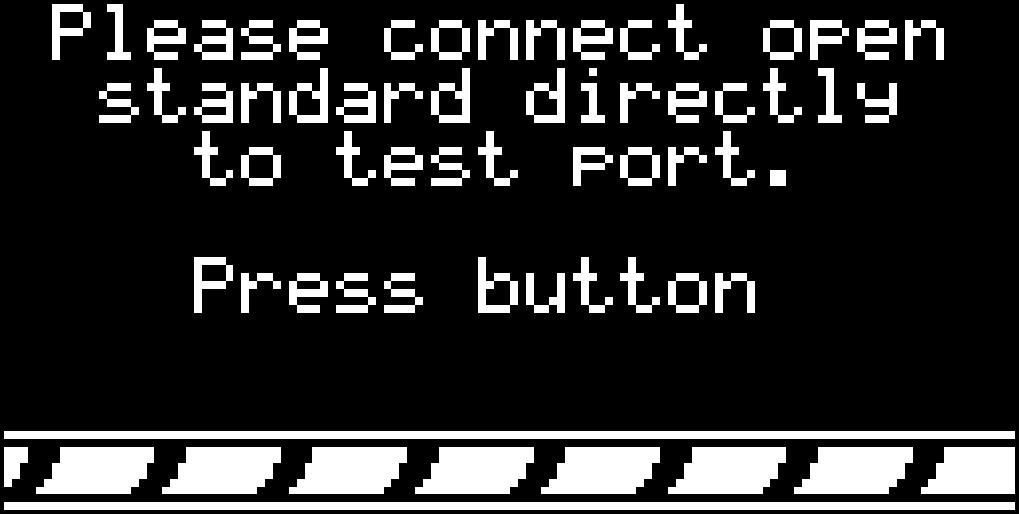
[picture p99: figure]

## Slide 29

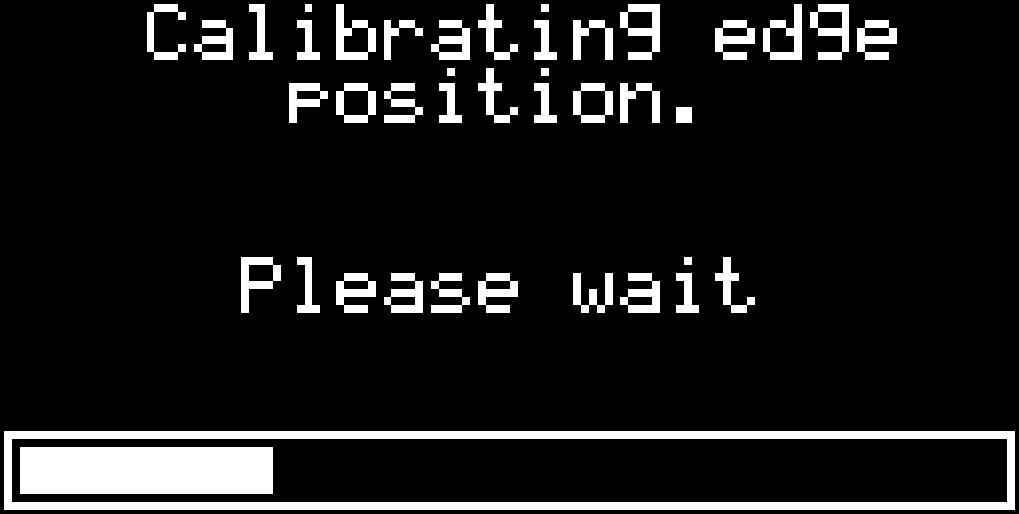
[picture p100: figure]

## Slide 30

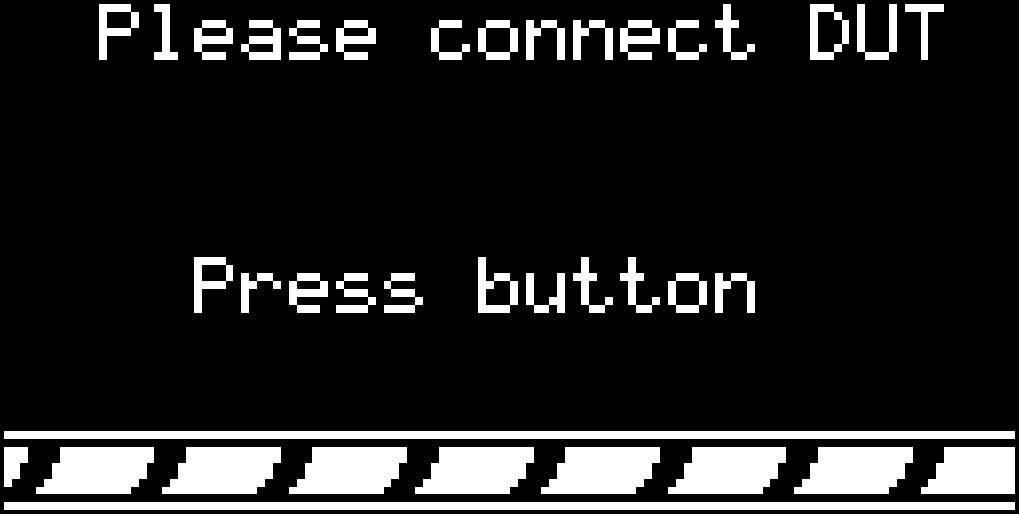
[picture p101: figure]

## Slide 31

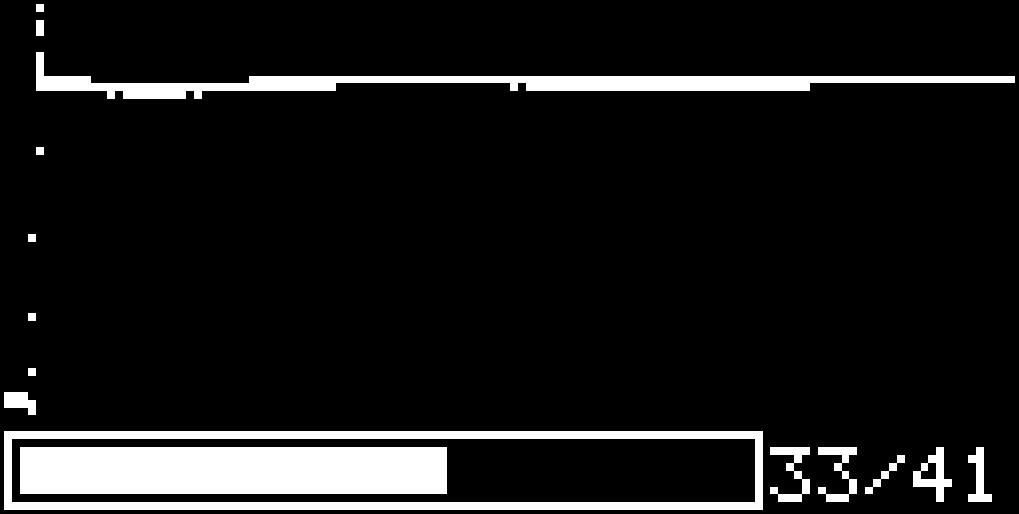
[picture p102: figure]

## Slide 32

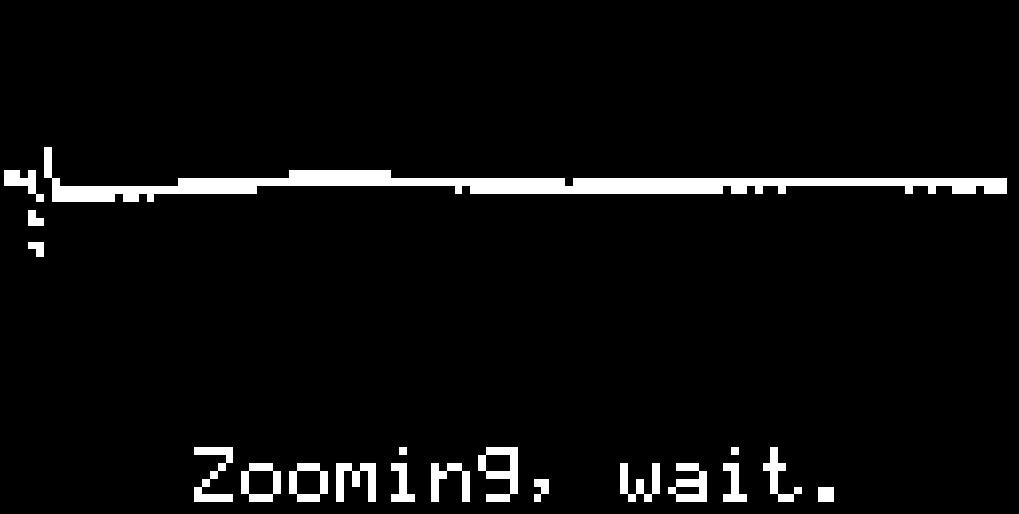
[picture p103: figure]

## Slide 33

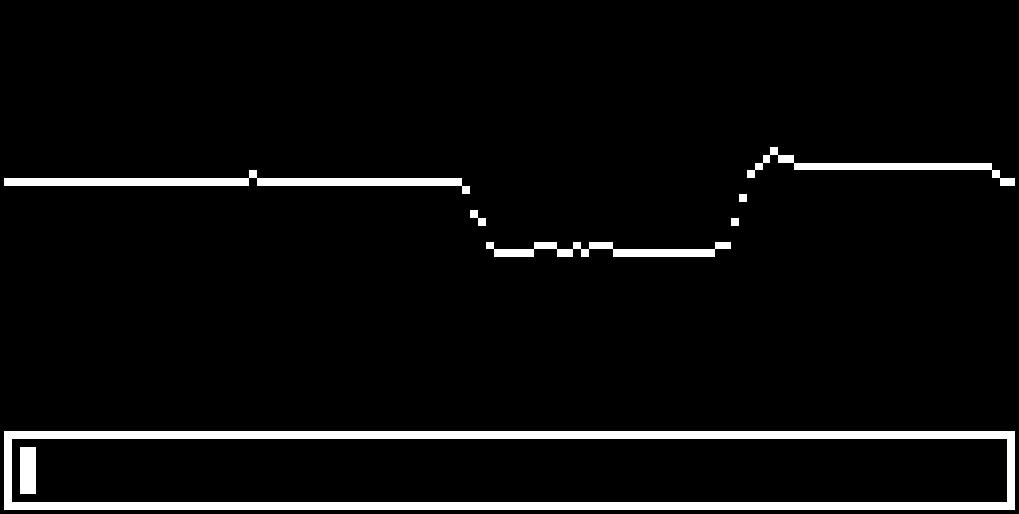
[picture p104: figure]

## Slide 34

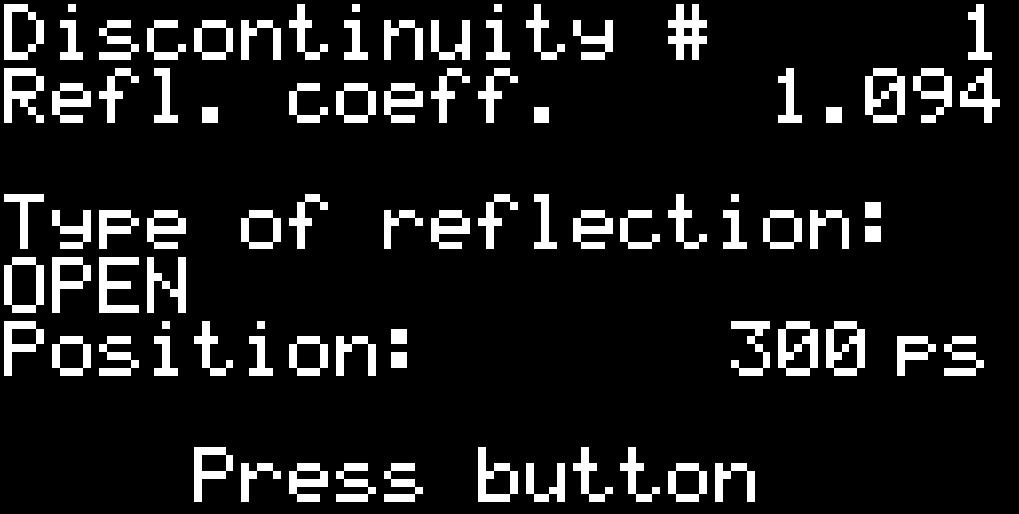
[picture p105: figure]

## Slide 35

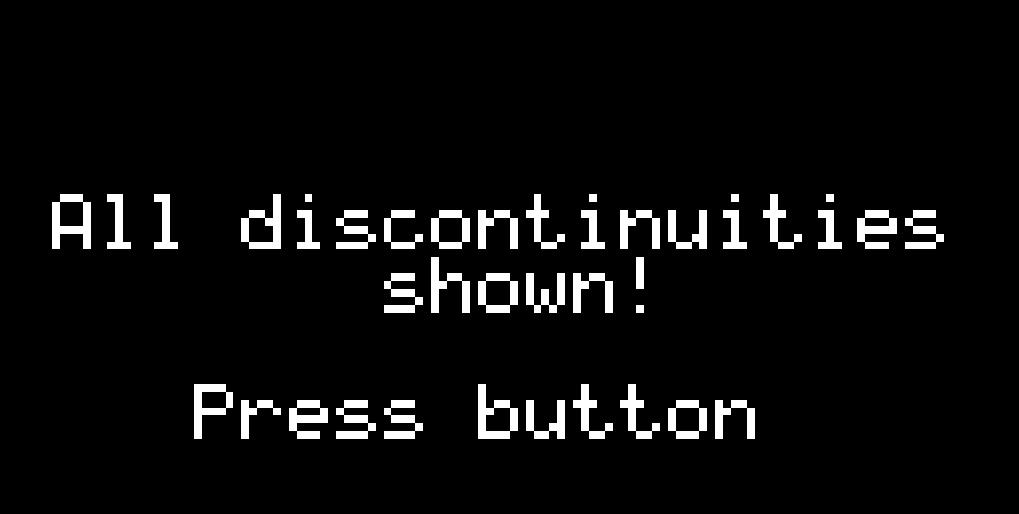
[picture p106: figure]

## Slide 36

Software pro PC

## Slide 37

## Slide 38

## Slide 39

## Slide 40

## Slide 41

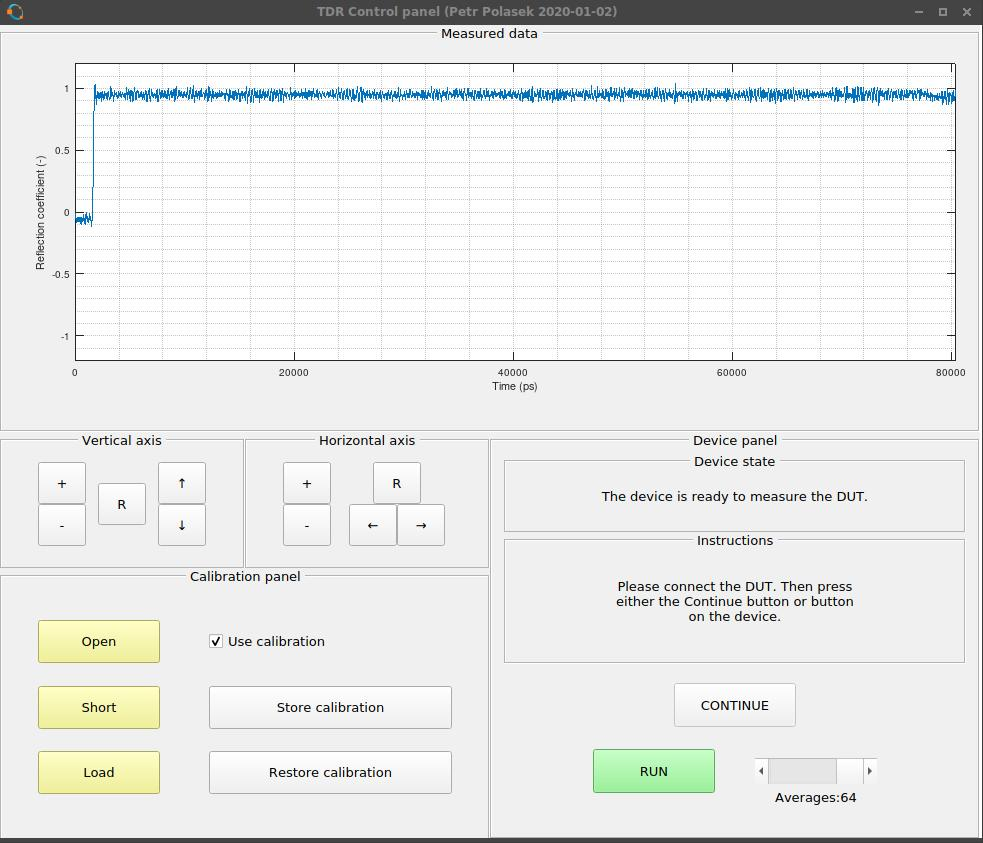
[picture p107: figure]

## Slide 42

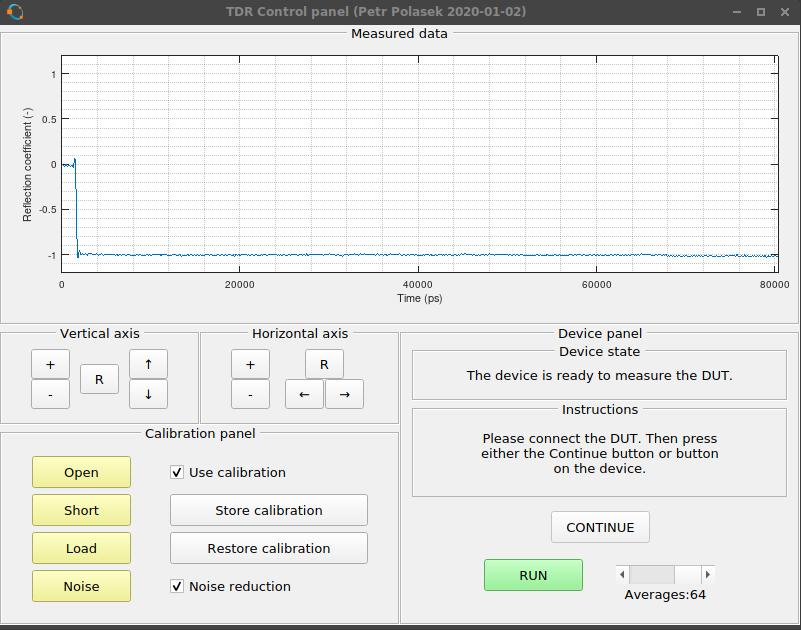
[picture p108: figure]

## Slide 43

SOL kalibrace

## Slide 44

## Slide 45

## Slide 46

## Slide 47

## Slide 48

## Slide 49

## Slide 50

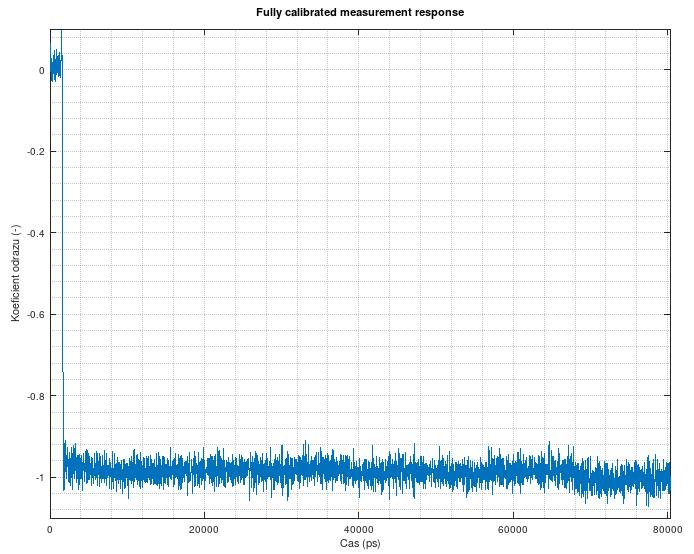
[picture p109: figure]

## Slide 51

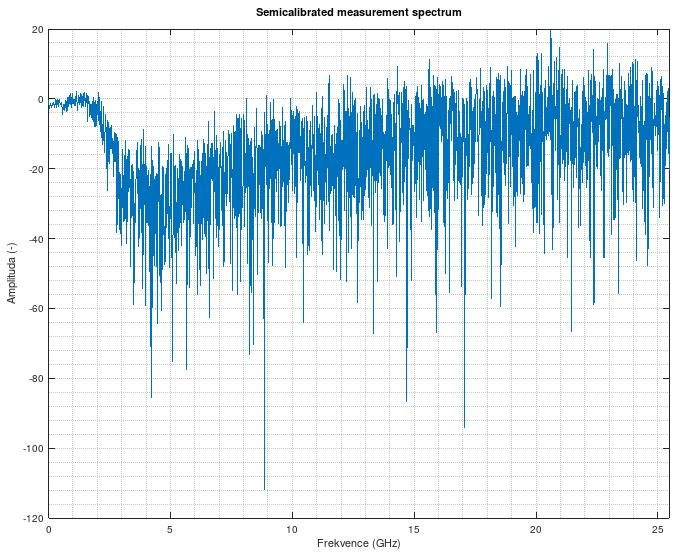
[picture p110: figure]

## Slide 52

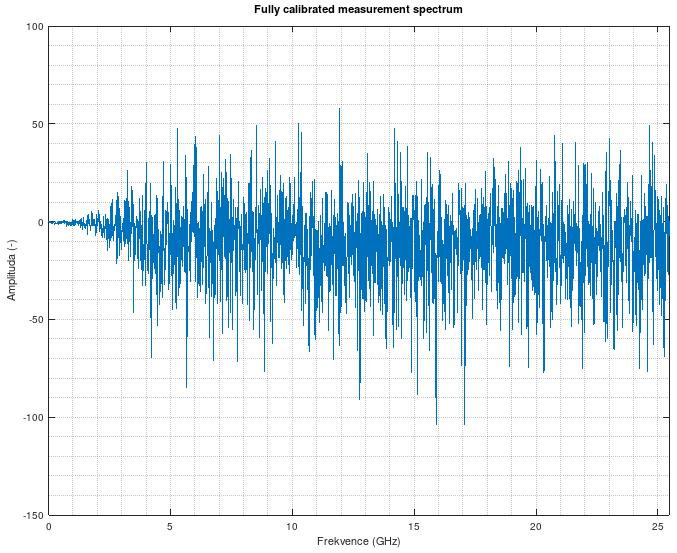
[picture p111: figure]

## Slide 53

Potlačení šumu

## Slide 54

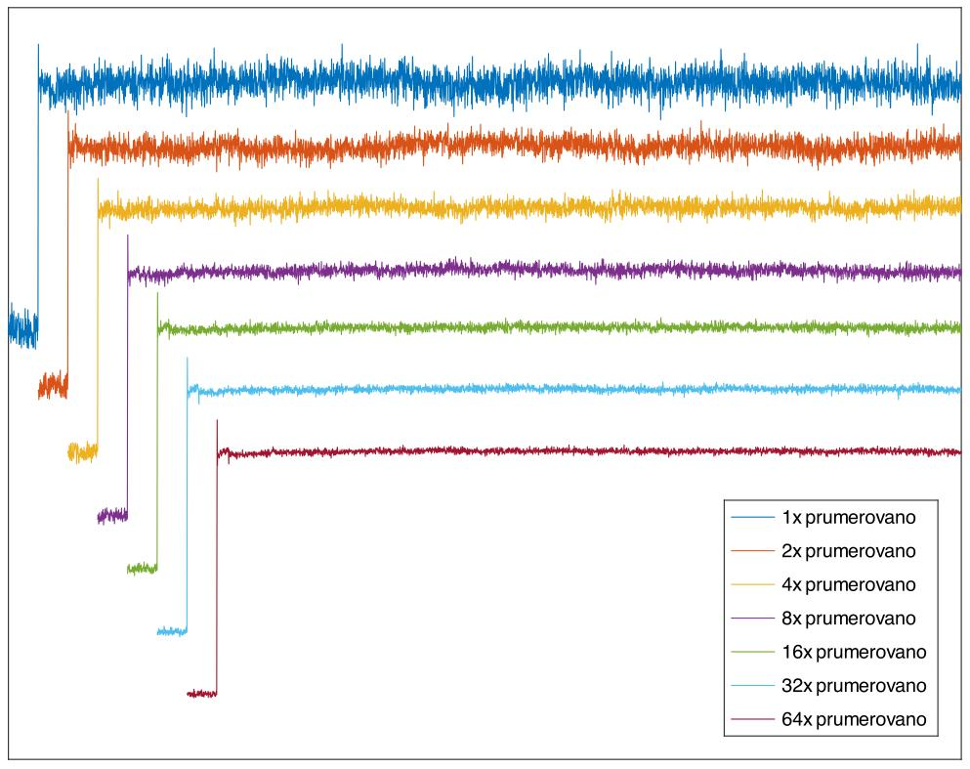
[picture p112: figure]

## Slide 55

## Slide 56


## Wienerova dekonvoluce

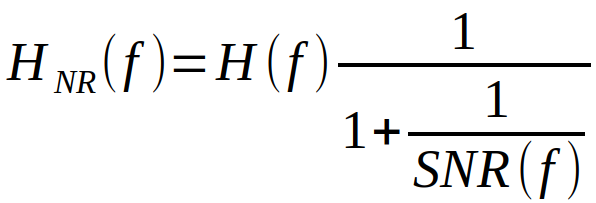
[picture p113: figure]

## Slide 58

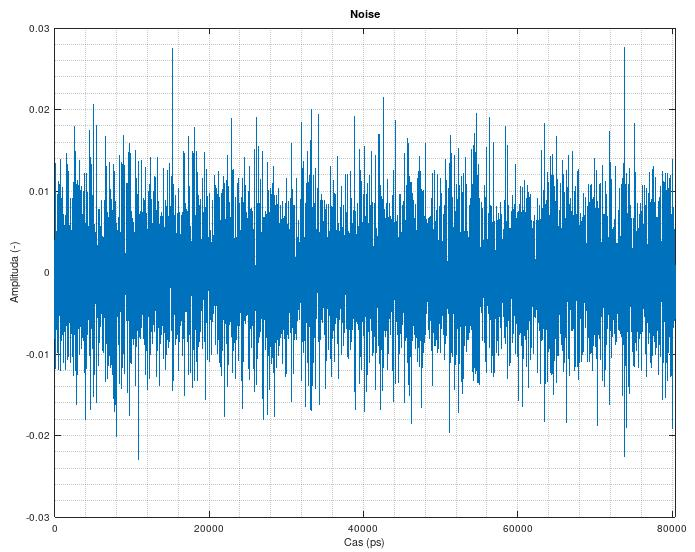
[picture p114: figure]

## Slide 59

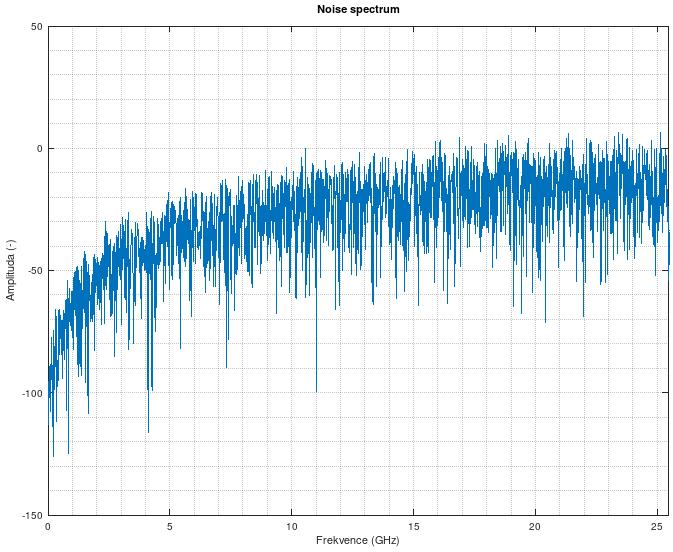
[picture p115: figure]

## Slide 60

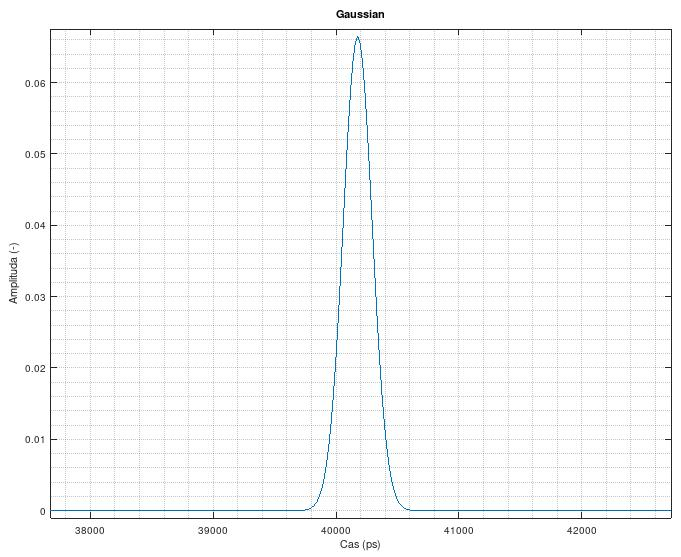
[picture p116: figure]

## Slide 61


## Slide 62

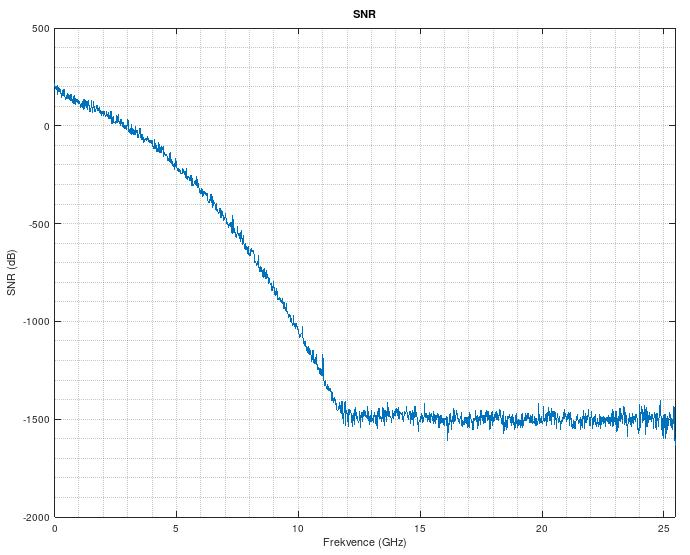
[picture p117: figure]

## Slide 63

## Slide 64

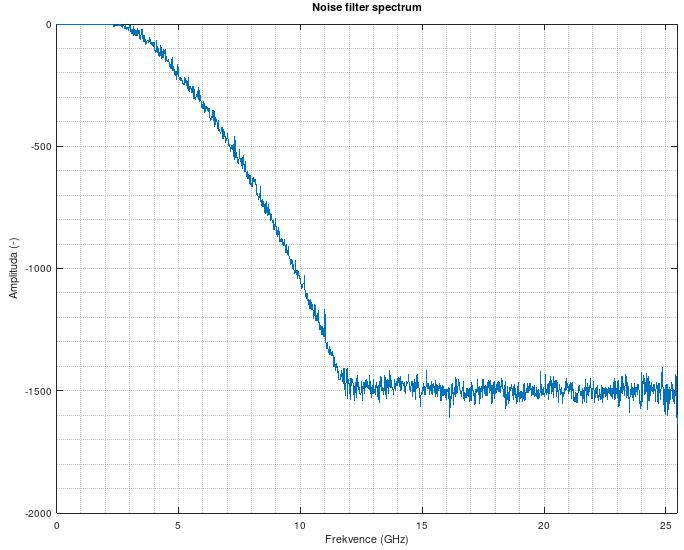
[picture p118: figure]

## Slide 65

## Slide 66

## Slide 67

## Slide 68

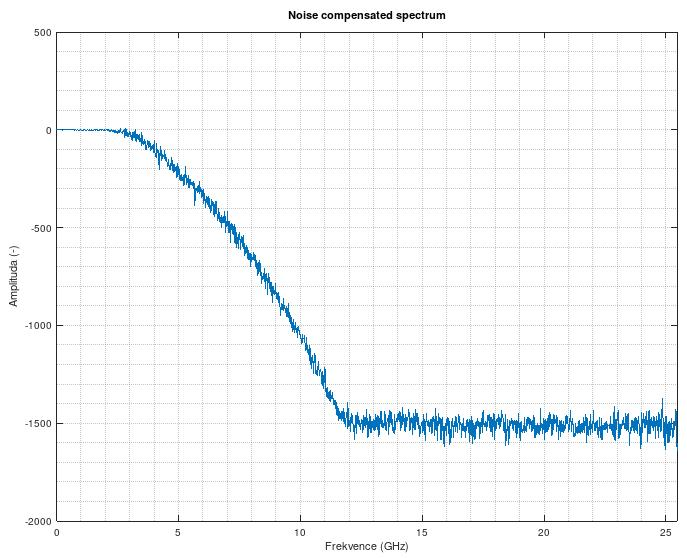
[picture p119: figure]

## Slide 69

## Slide 70

## Slide 71

Změřené parametry

## Slide 72


## Slide 73


## Slide 74

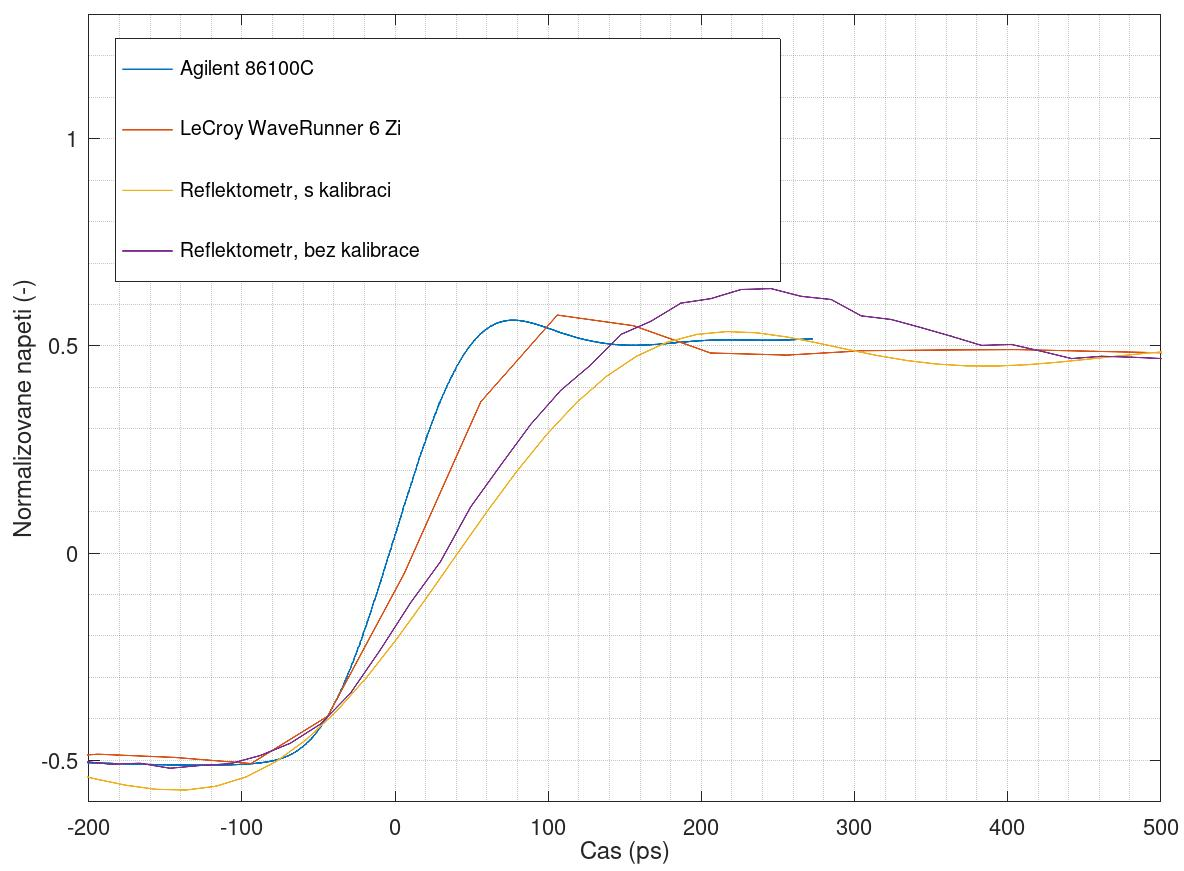
[picture p120: figure]

## Slide 75

## Slide 76

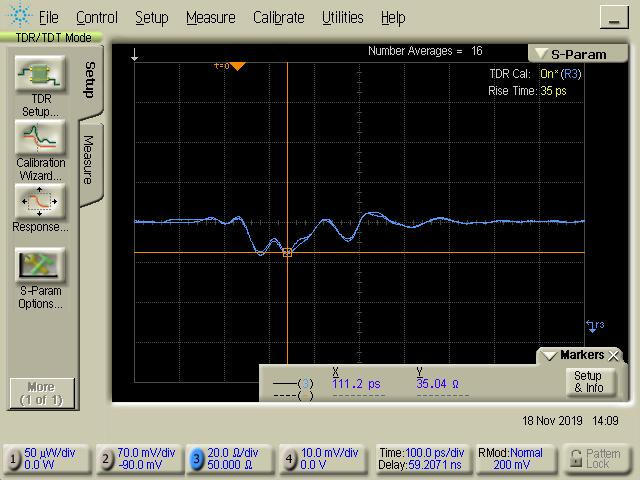
[picture p121: figure]

## Slide 77

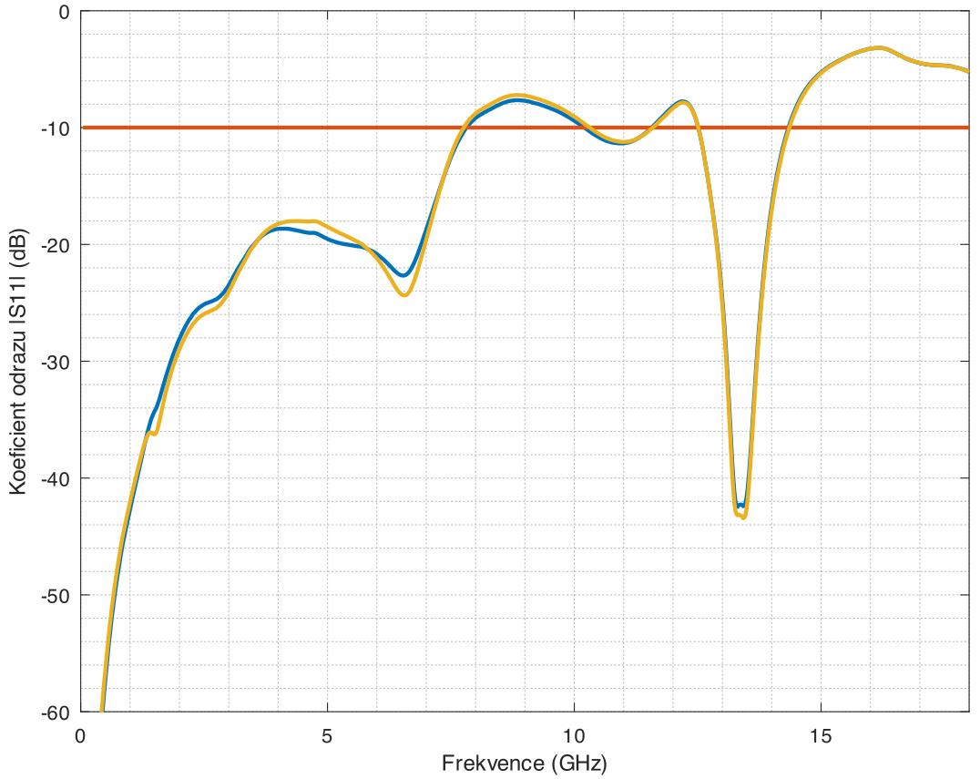
[picture p122: figure]

## Diplomová práce Reflektometr v časové oblasti

ČVUT FEL EK, Elektronika

Petr Polášek

2020-02-01
