MR-DOS/TDR_diploma_thesis/LaTeX/images/averaging_float_variance-eps-converted-to.pdf

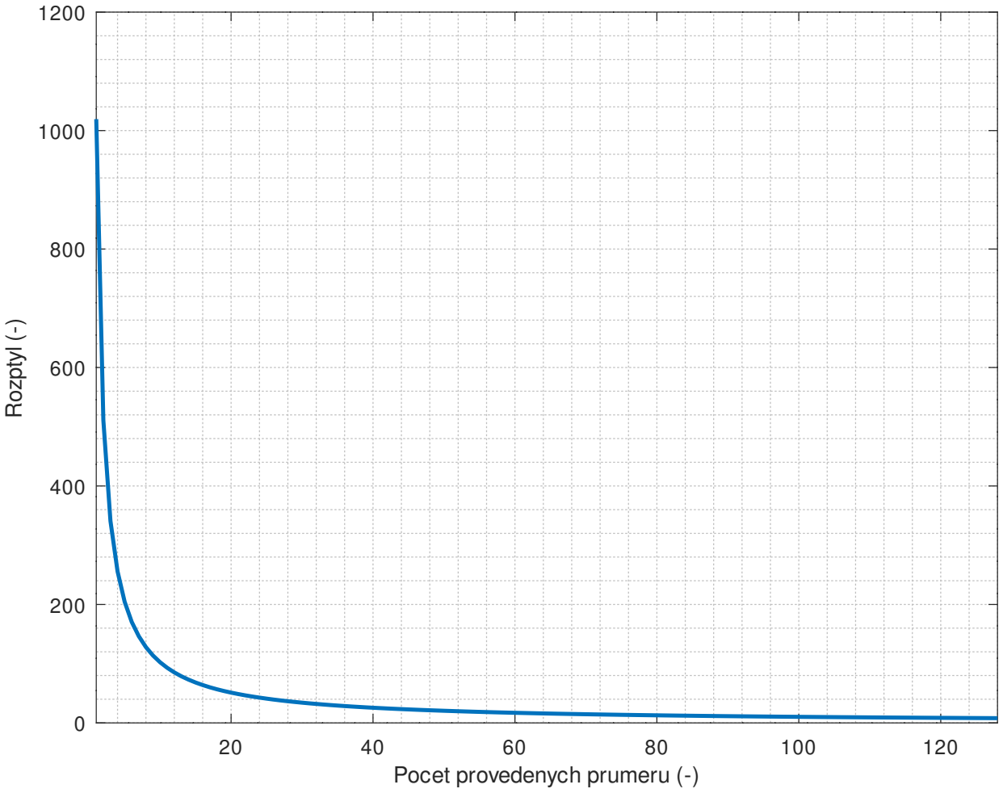
[picture p123: figure]
Pocet provedenych prumeru (-); Rozptyl (-)
