MR-DOS/TDR_diploma_thesis/LaTeX/images/rising_edge_DUT_open-eps-converted-to.pdf

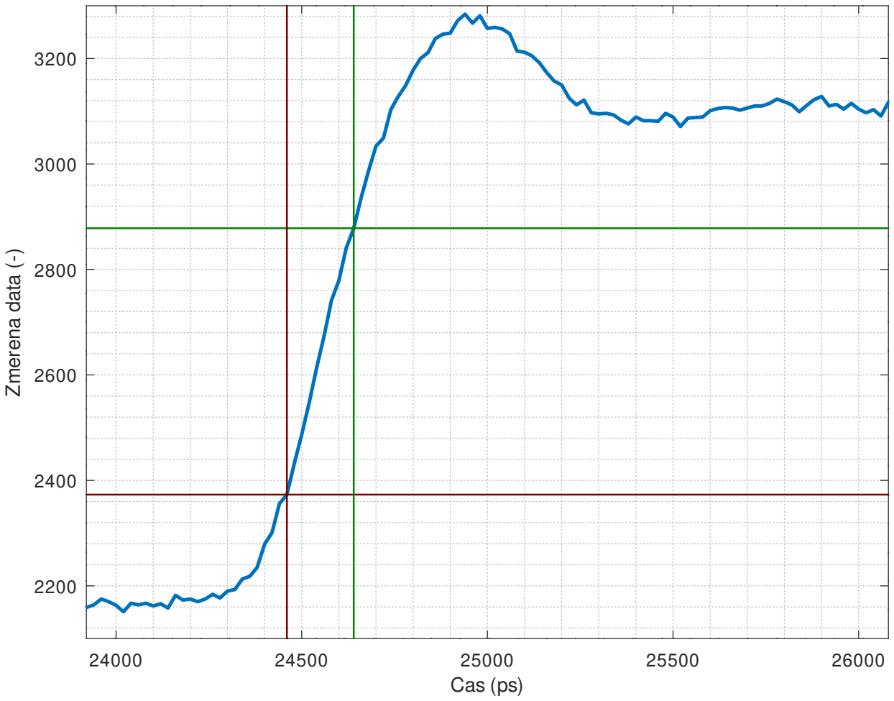
[picture p124: figure]
Cas (ps); Zmerena data (-)
