MR-DOS/TDR_diploma_thesis/LaTeX/images/onereflectionsample.png

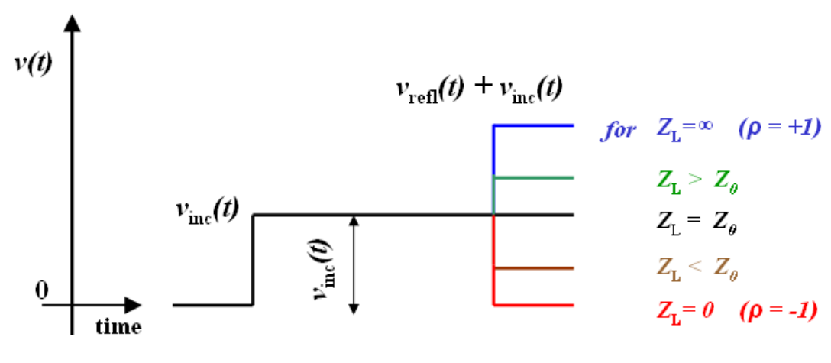
LaTeX/images/onereflectionsample.png
