MR-DOS/TDR_diploma_thesis/LaTeX/images/pcb/pcb_secondary_sampler.jpg

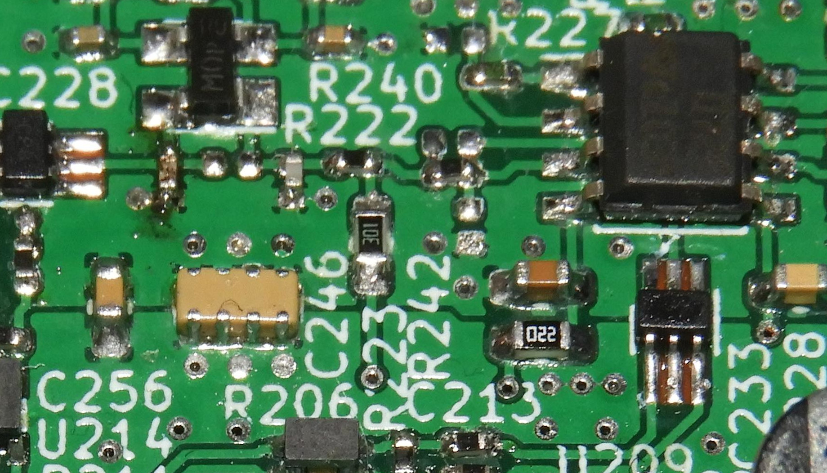
LaTeX/images/pcb/pcb_secondary_sampler.jpg
