MR-DOS/TDR_diploma_thesis/LaTeX/images/samplecomplexresponse.png

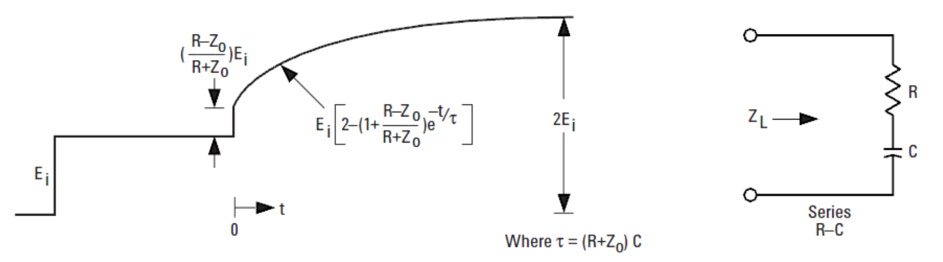
LaTeX/images/samplecomplexresponse.png
