MR-DOS/TDR_diploma_thesis/obhajoba/corr.png

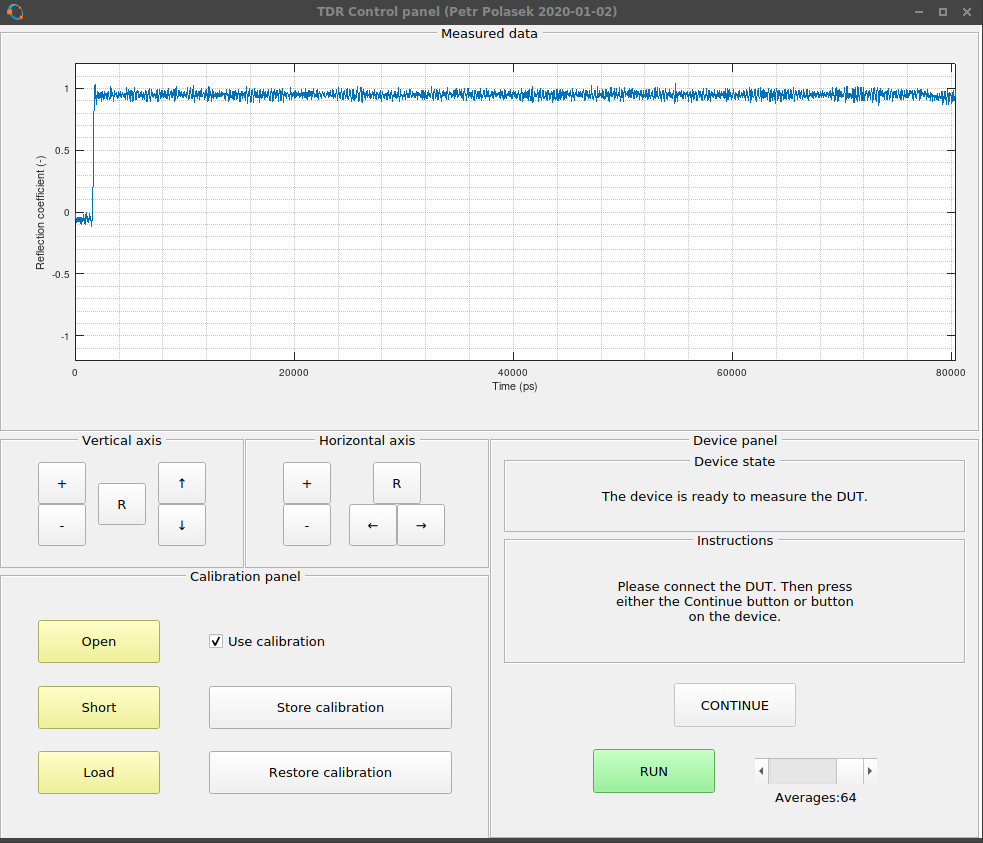
obhajoba/corr.png
