MR-DOS/TDR_diploma_thesis/obhajoba/filter_response.png

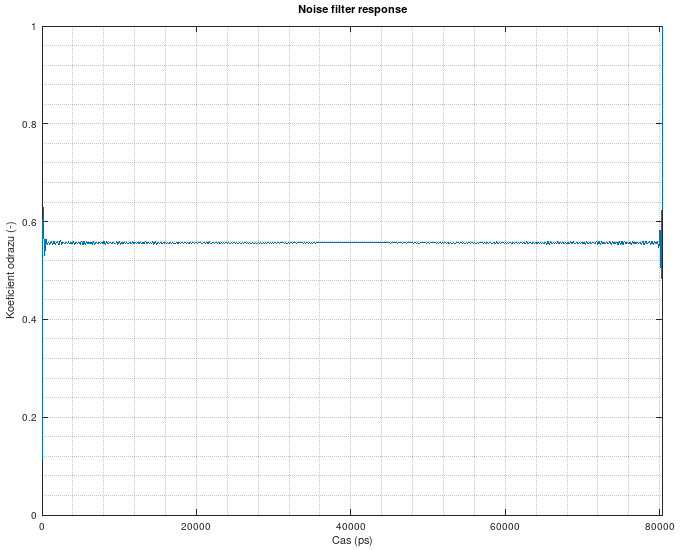
obhajoba/filter_response.png
