MR-DOS/TDR_diploma_thesis/obhajoba/filter_spectrum.png

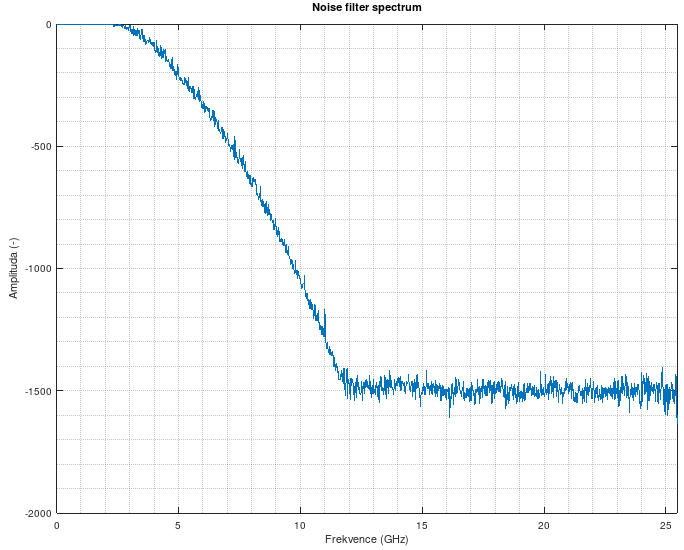
obhajoba/filter_spectrum.png
