MR-DOS/TDR_diploma_thesis/obhajoba/noise_spectrum.png

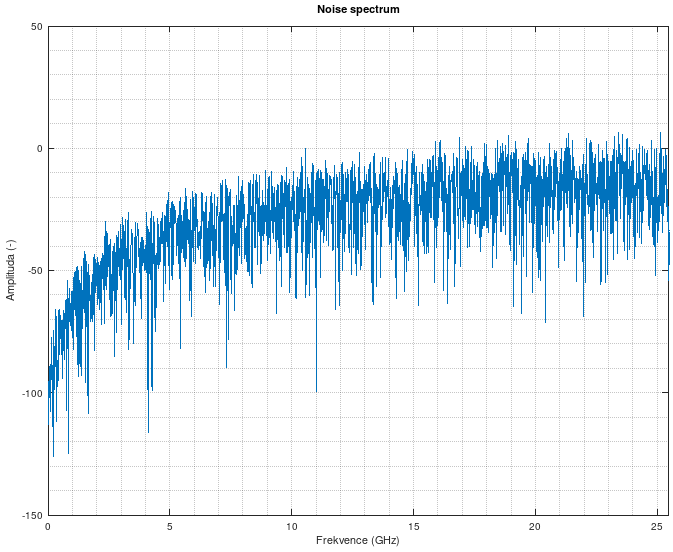
obhajoba/noise_spectrum.png
