MR-DOS/TDR_diploma_thesis/obhajoba/SNR.png

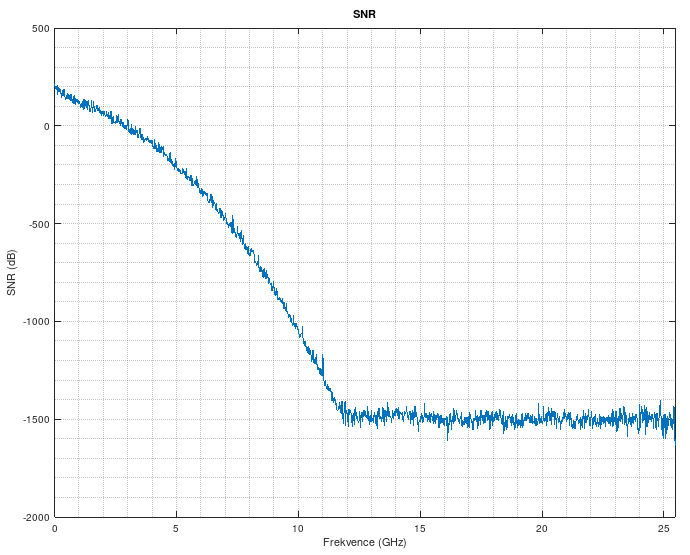
obhajoba/SNR.png
