MR-DOS/TDR_diploma_thesis/obhajoba/SNR_zoom.png

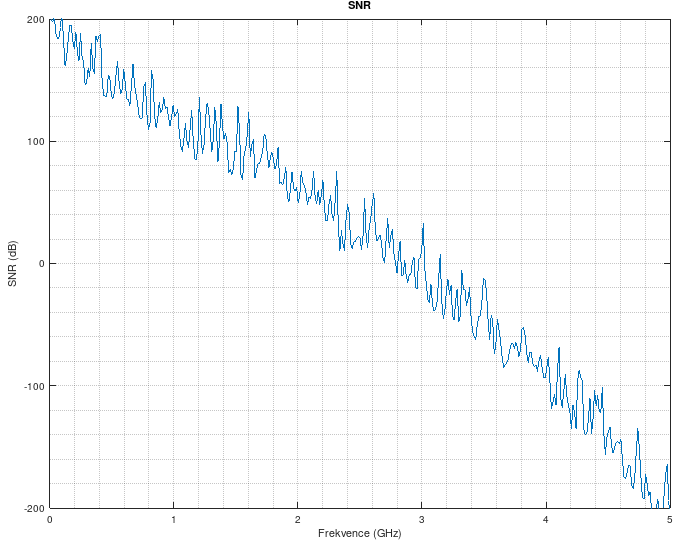
obhajoba/SNR_zoom.png
