MR-DOS/TDR_diploma_thesis/obhajoba/pcb_bottom_assembled.jpg

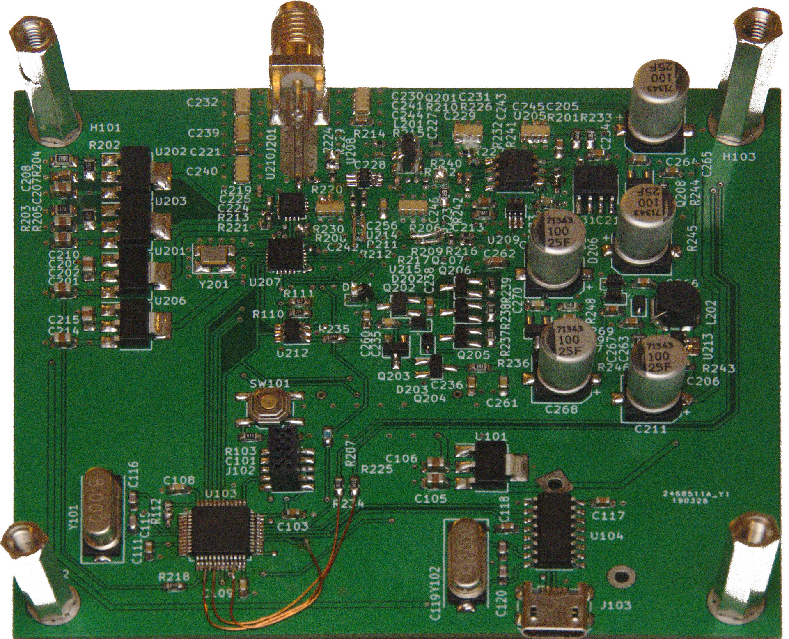
obhajoba/pcb_bottom_assembled.jpg
