MR-DOS/TDR_diploma_thesis/measurements/oscilloscope/C1--vlc_pc--00002.csv

LECROYWR640Zi | 55774 | Waveform
Segments | 1 | SegmentSize | 202
Segment | TrigTime | TimeSinceSegment1
#1 | 18-Nov-2019 09:45:25 | 0
Time | Ampl
-5.05e-09 | -0.00186671
-5e-09 | -0.00185383
-4.95e-09 | -0.00184096
-4.9e-09 | -0.00182809
-4.85e-09 | -0.00184096
-4.8e-09 | -0.00184096
-4.75e-09 | -0.00186671
-4.7e-09 | -0.00187958
-4.65e-09 | -0.00189245
-4.6e-09 | -0.00190533
-4.55e-09 | -0.0019182
-4.5e-09 | -0.0019182
-4.45e-09 | -0.00190533
-4.4e-09 | -0.00189245
-4.35e-09 | -0.00187958
-4.3e-09 | -0.00186671
-4.25e-09 | -0.00186671
-4.2e-09 | -0.00187958
-4.15e-09 | -0.00187958
-4.1e-09 | -0.00189245
-4.05e-09 | -0.00190533
-4e-09 | -0.0019182
-3.95e-09 | -0.0019182
-3.9e-09 | -0.0019182
-3.85e-09 | -0.00189245
-3.8e-09 | -0.00187958
-3.75e-09 | -0.00187958
-3.7e-09 | -0.00187958
-3.65e-09 | -0.00187958
-3.6e-09 | -0.00187958
-3.55e-09 | -0.00186671
-3.5e-09 | -0.00185383
-3.45e-09 | -0.00182809
-3.4e-09 | -0.00181521
-3.35e-09 | -0.00181521
-3.3e-09 | -0.00181521
-3.25e-09 | -0.00182809
-3.2e-09 | -0.00182809
-3.15e-09 | -0.00182809
-3.1e-09 | -0.00181521
-3.05e-09 | -0.00181521
-3e-09 | -0.00181521
-2.95e-09 | -0.00182809
-2.9e-09 | -0.00182809
-2.85e-09 | -0.00182809
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
