MR-DOS/TDR_diploma_thesis/measurements/oscilloscope/236--00004.png

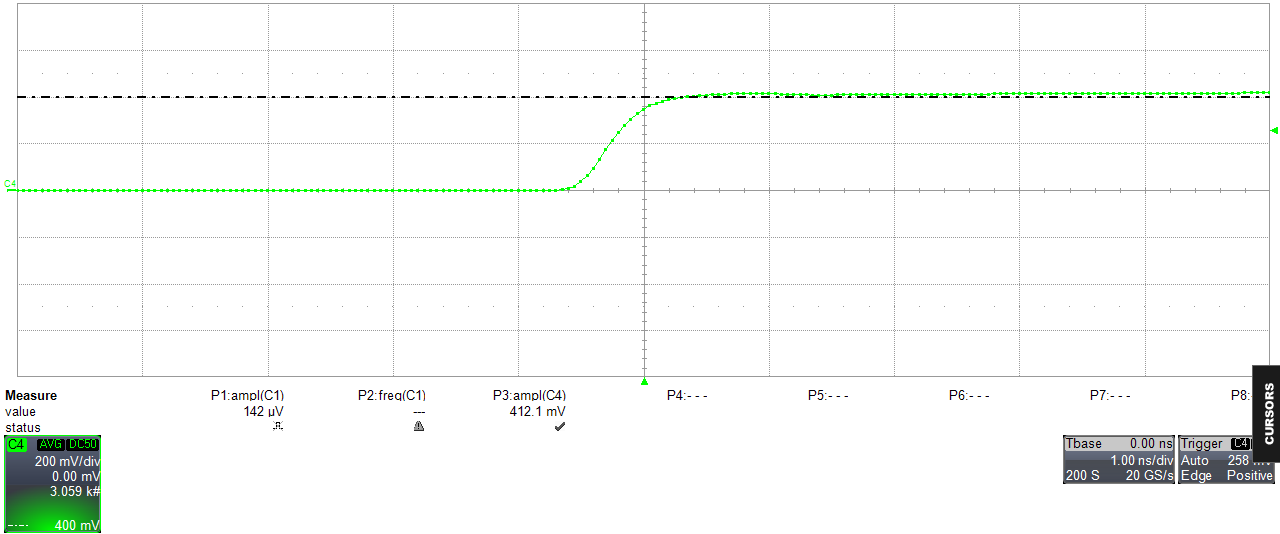
measurements/oscilloscope/236--00004.png
