MR-DOS/TDR_diploma_thesis/measurements/oscilloscope/screen2.bmp

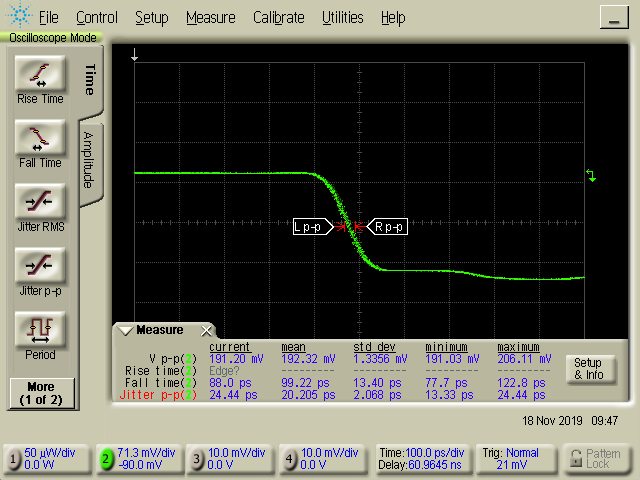
measurements/oscilloscope/screen2.bmp
