MR-DOS/TDR_diploma_thesis/measurements/oscilloscope/screen3.bmp

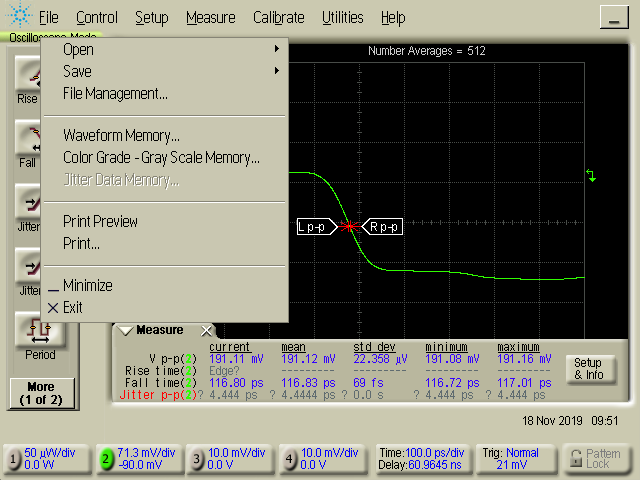
measurements/oscilloscope/screen3.bmp
