MR-DOS/TDR_diploma_thesis/measurements/oscilloscope/screen5.bmp

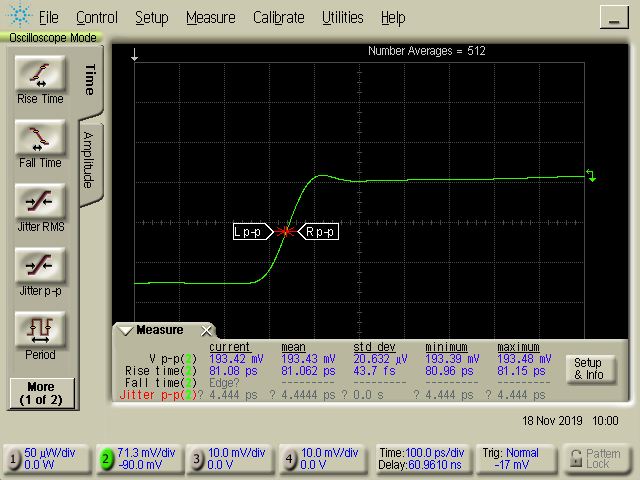
measurements/oscilloscope/screen5.bmp
