MR-DOS/TDR_diploma_thesis/measurements/oscilloscope/screen7.bmp

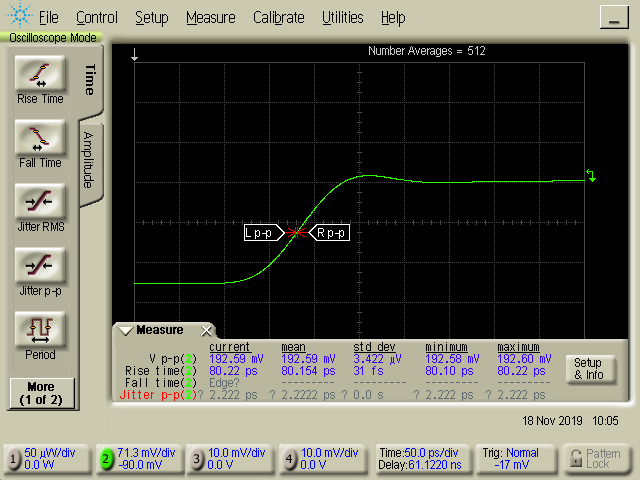
measurements/oscilloscope/screen7.bmp
