MR-DOS/TDR_diploma_thesis/measurements/oscilloscope/screen12.bmp

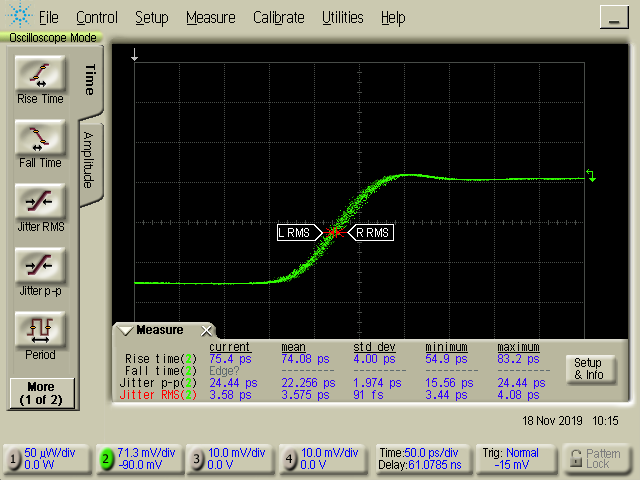
measurements/oscilloscope/screen12.bmp
