MR-DOS/TDR_diploma_thesis/measurements/TDR/screen16.bmp

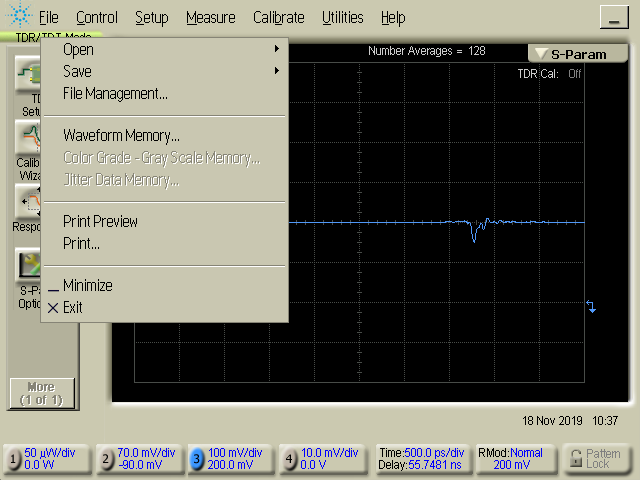
measurements/TDR/screen16.bmp
