MR-DOS/TDR_diploma_thesis/measurements/TDR/screen18.bmp

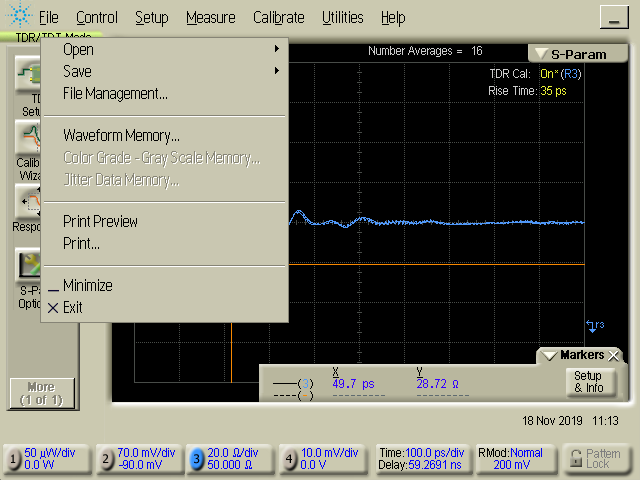
measurements/TDR/screen18.bmp
