MR-DOS/TDR_diploma_thesis/obhajoba/calibrated_spectrum.png

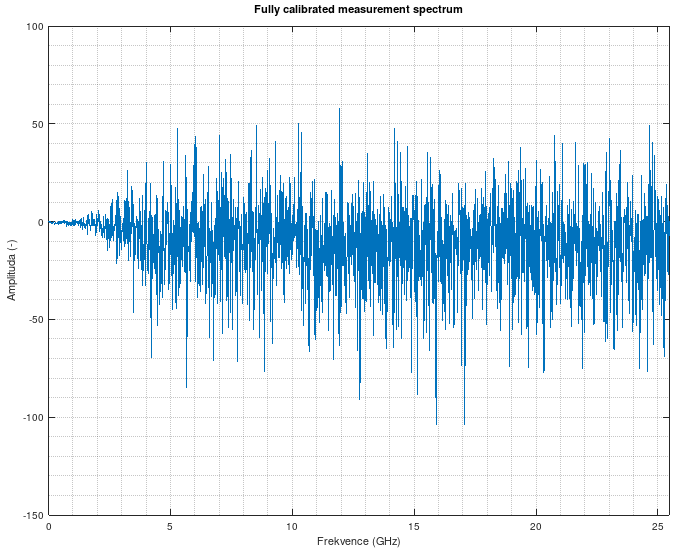
obhajoba/calibrated_spectrum.png
