MR-DOS/TDR_diploma_thesis/obhajoba/calibrated_waveform.png

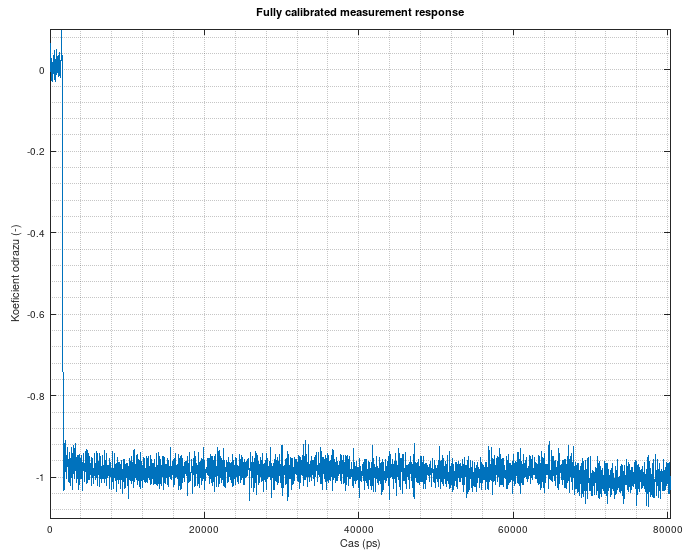
obhajoba/calibrated_waveform.png
