MR-DOS/TDR_diploma_thesis/trl_calibration_set_measurement/cst/FR4.png

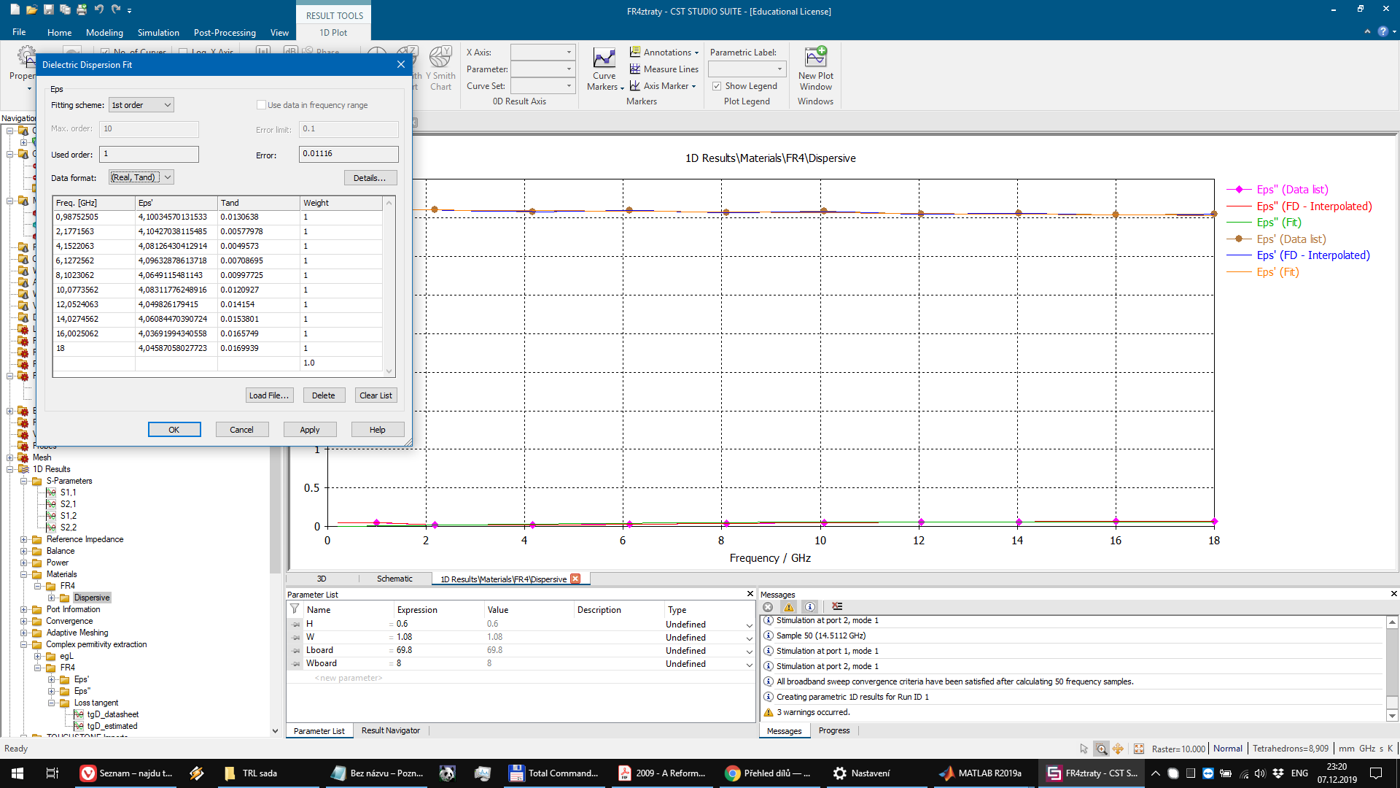
trl_calibration_set_measurement/cst/FR4.png
