MR-DOS/TDR_diploma_thesis/trl_calibration_set_measurement/cst/microstrip.png

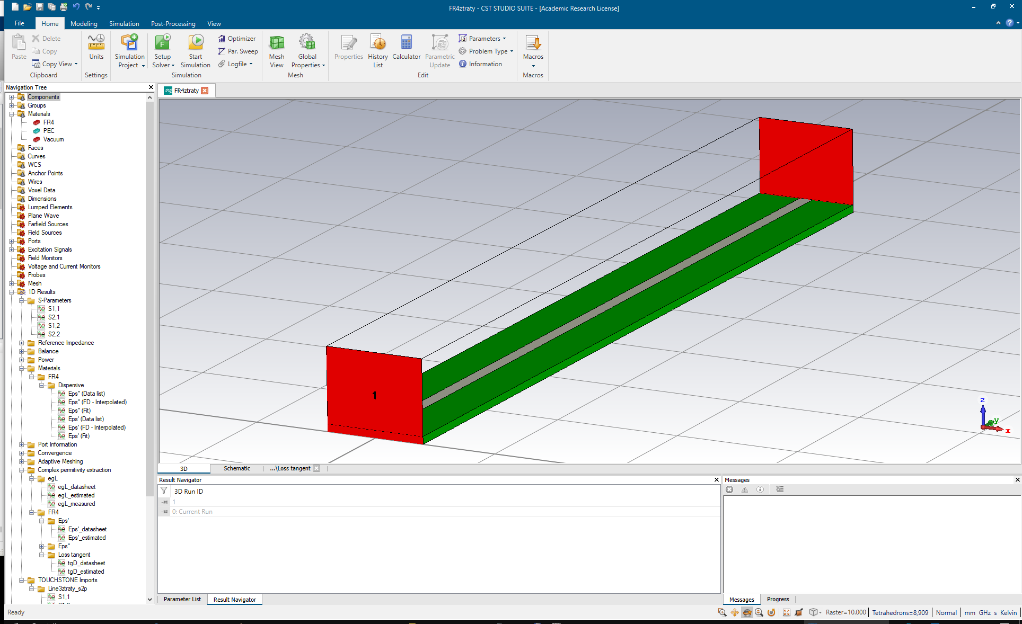
trl_calibration_set_measurement/cst/microstrip.png
