MR-DOS/TDR_diploma_thesis/LaTeX/images/lvds_output-eps-converted-to.pdf

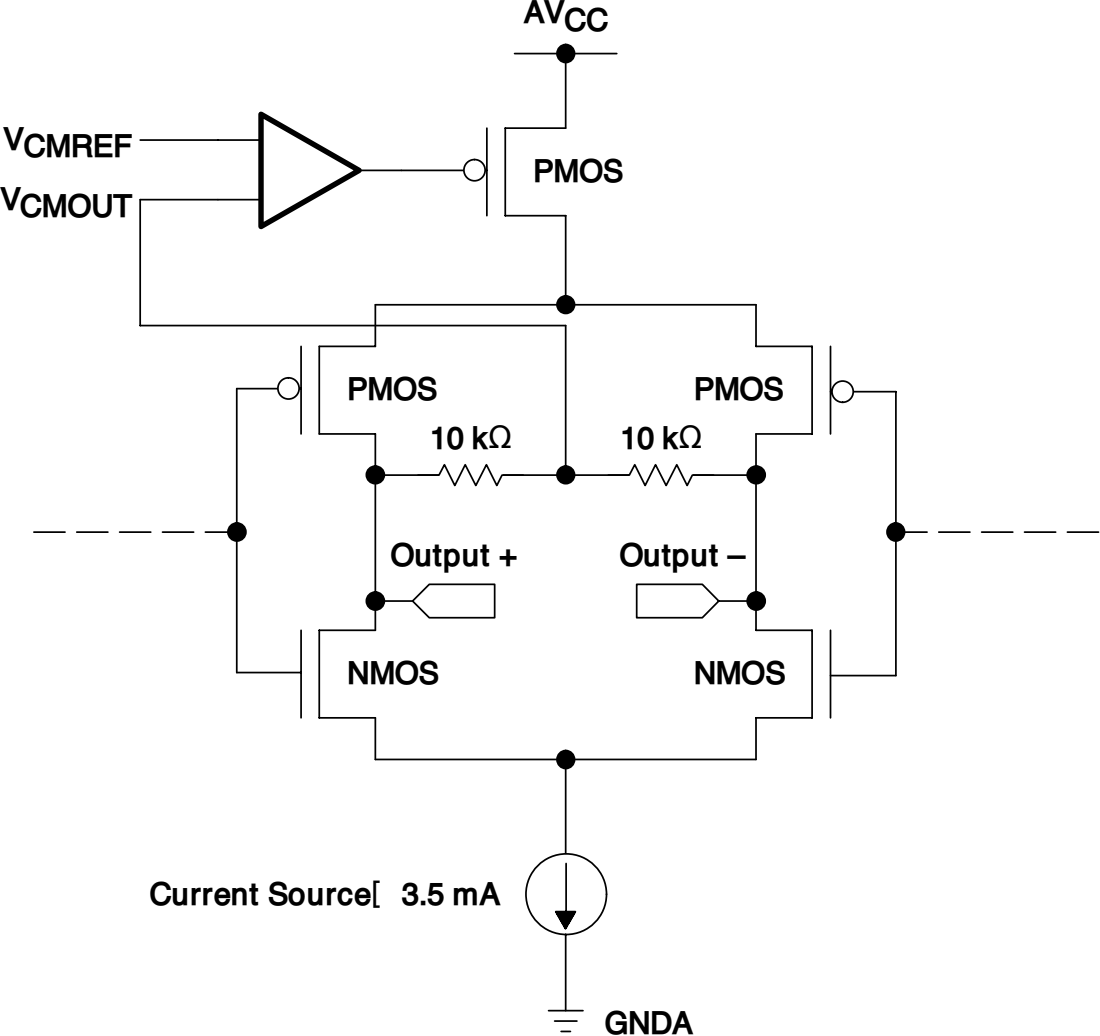
[picture p154: page 1]
Output +; Output –; PMOS; GNDA; NMOS; VCMREF; VCMOUT; AVCC

Current Source[ 3.5 mA
