MR-DOS/TDR_diploma_thesis/LaTeX/images/lvpecl_output-eps-converted-to.pdf

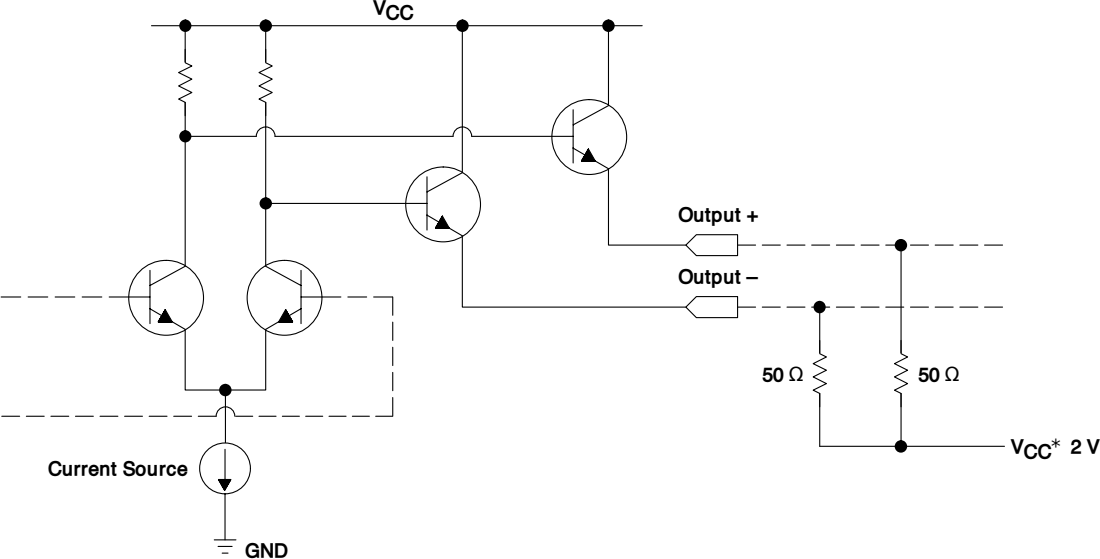
[picture p155: page 1]
Output +; Output –; GND; Current Source; VCC; VCC* 2 V
