MR-DOS/TDR_diploma_thesis/LaTeX/images/block_diagram-eps-converted-to.pdf

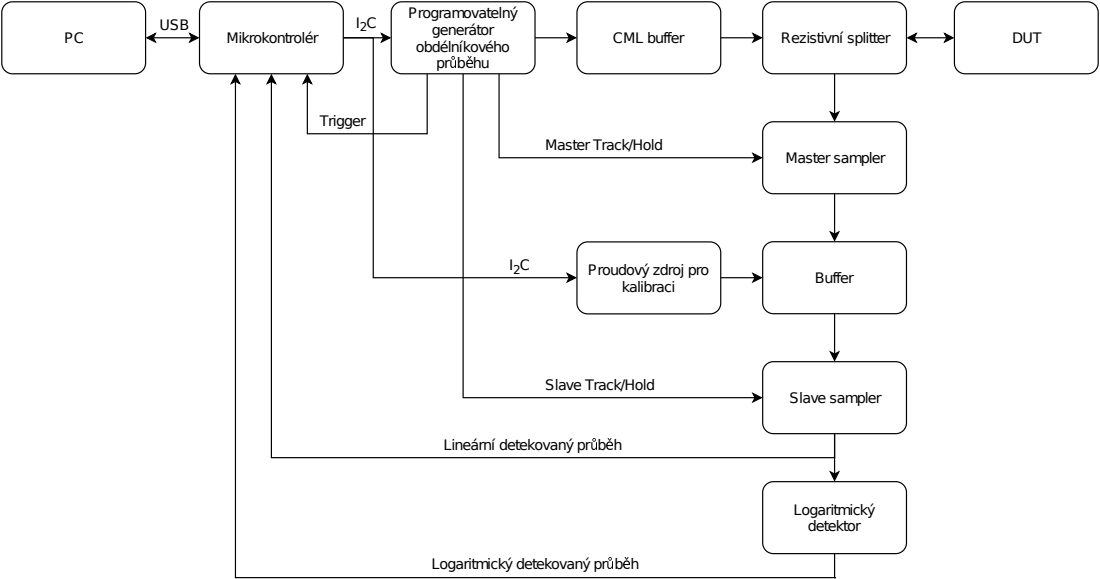
[picture p156: page 1]
Programovatelný generátor obdélníkového prb- hu; Rezistivní splitter; DUT; Master sampler; Buffer; Slave sampler; Logaritmický detektor; Mikrokontrolér; Trigger; USB; CML buffer

Master Track/Hold

Proudový zdroj pro
kalibraci

Slave Track/Hold

Lineární detekovaný prb-

Logaritmický detekovaný prb-
