MR-DOS/TDR_diploma_thesis/LaTeX/images/measurements/vna_low_blank-eps-converted-to.pdf

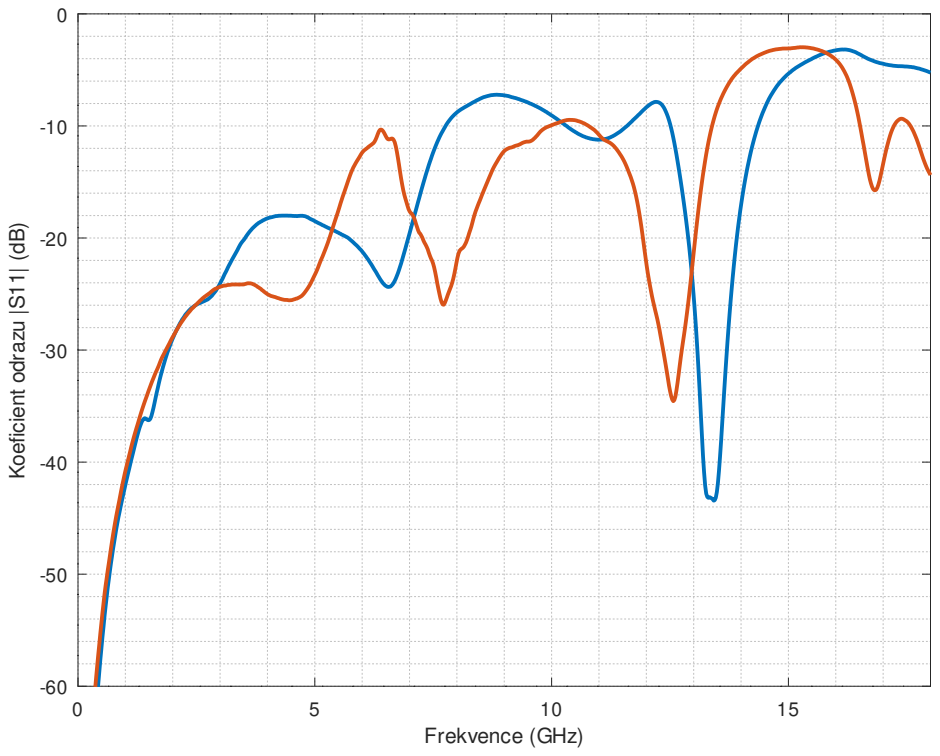
[picture p166: page 1]
Frekvence (GHz)

Koeficient odrazu |S11| (dB)
