MR-DOS/TDR_diploma_thesis/LaTeX/images/denoiser_transfer_function-eps-converted-to.pdf

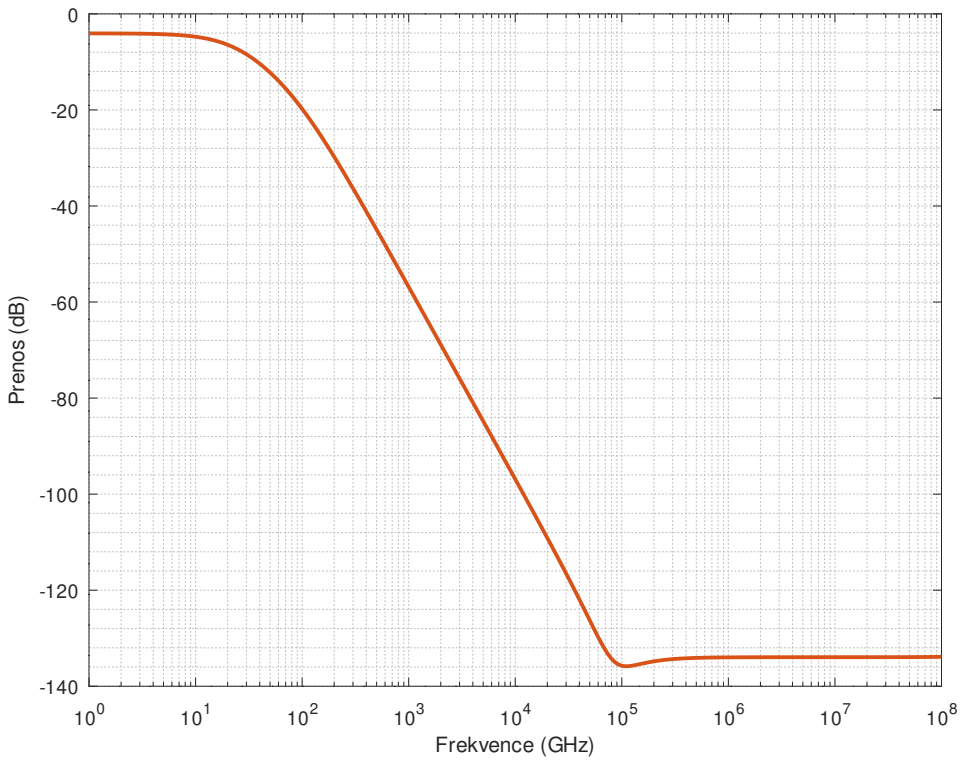
[picture p167: page 1]
Frekvence (GHz); Prenos (dB)
