MR-DOS/TDR_diploma_thesis/LaTeX/images/frequency_transfer_function_all-eps-converted-to.pdf

-100 0

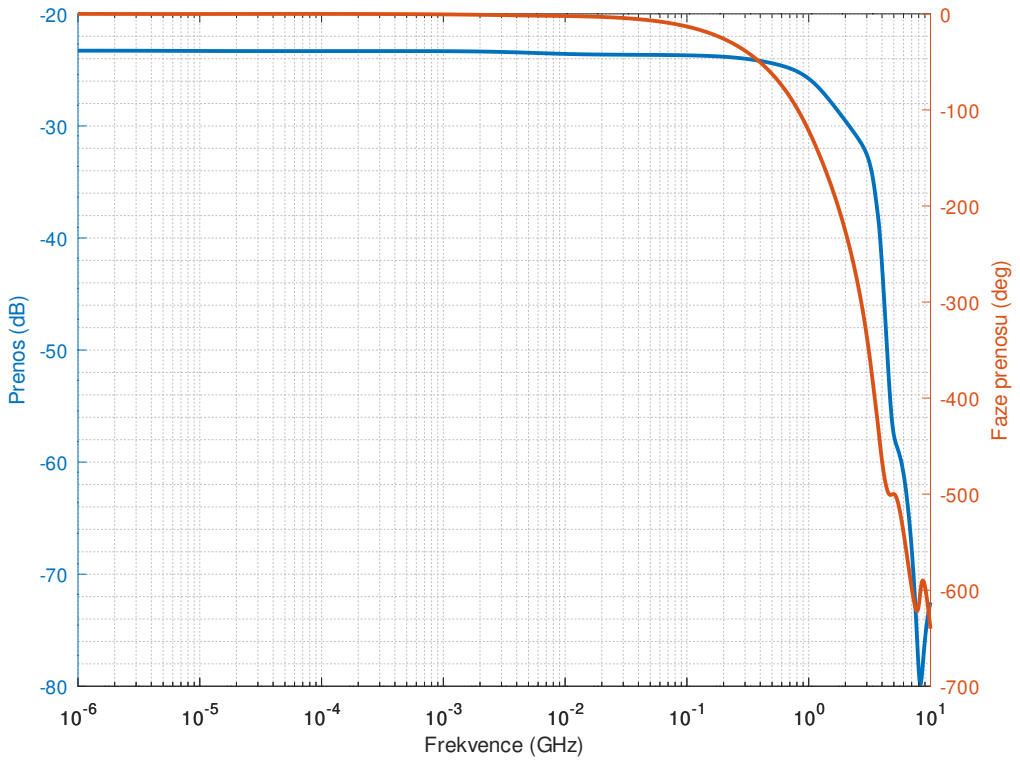
[picture p168: page 1]
Prenos (dB); Frekvence (GHz)

Faze prenosu (deg)
