MR-DOS/TDR_diploma_thesis/LaTeX/images/frequency_transfer_function_BF-eps-converted-to.pdf

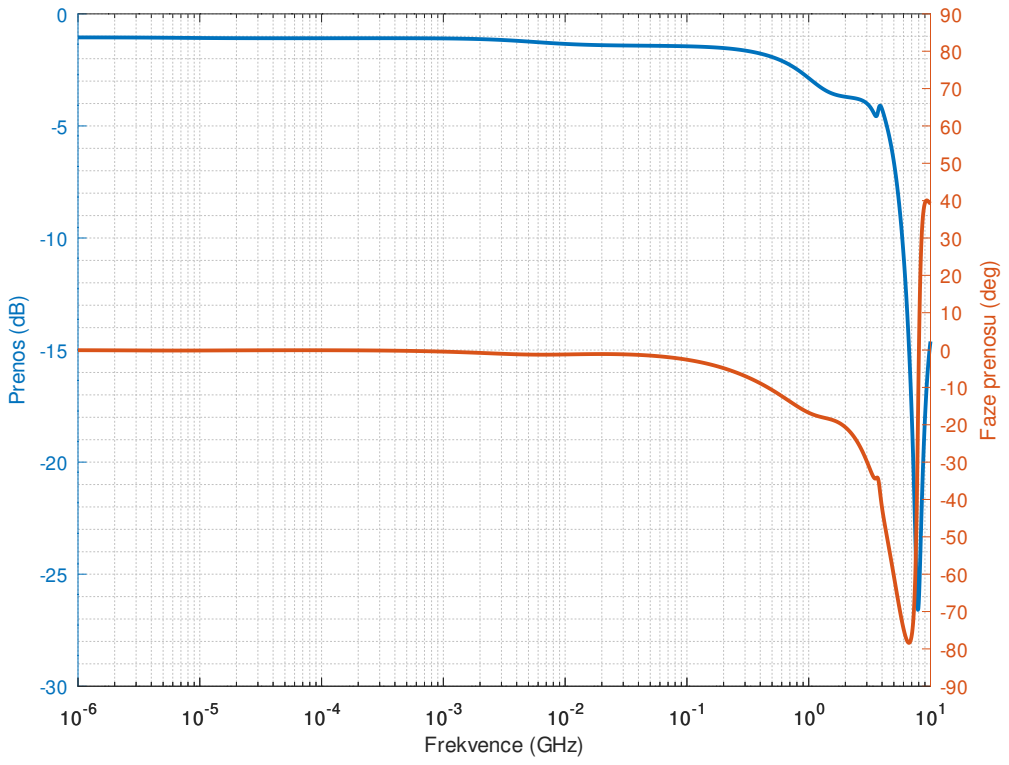
[picture p169: page 1]
Prenos (dB); Frekvence (GHz)

Faze prenosu (deg)
