MR-DOS/TDR_diploma_thesis/LaTeX/images/input_impedance-eps-converted-to.pdf

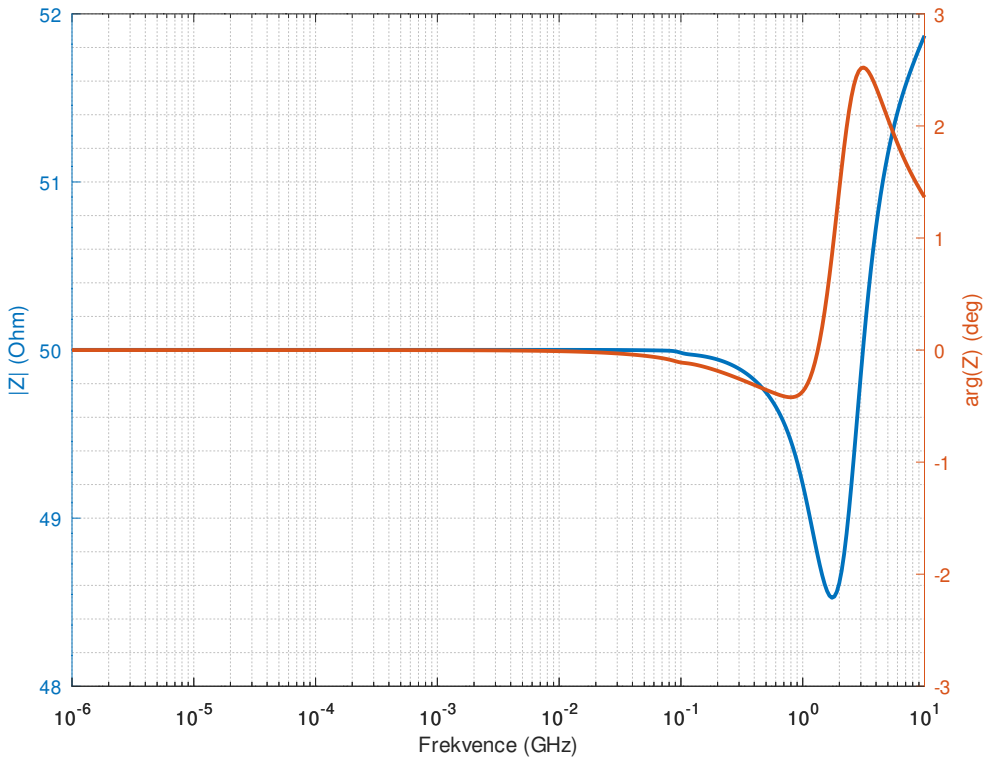
[picture p170: page 1]
|Z| (Ohm); Frekvence (GHz); arg(Z) (deg)
