MR-DOS/TDR_diploma_thesis/LaTeX/images/input_reflection-eps-converted-to.pdf

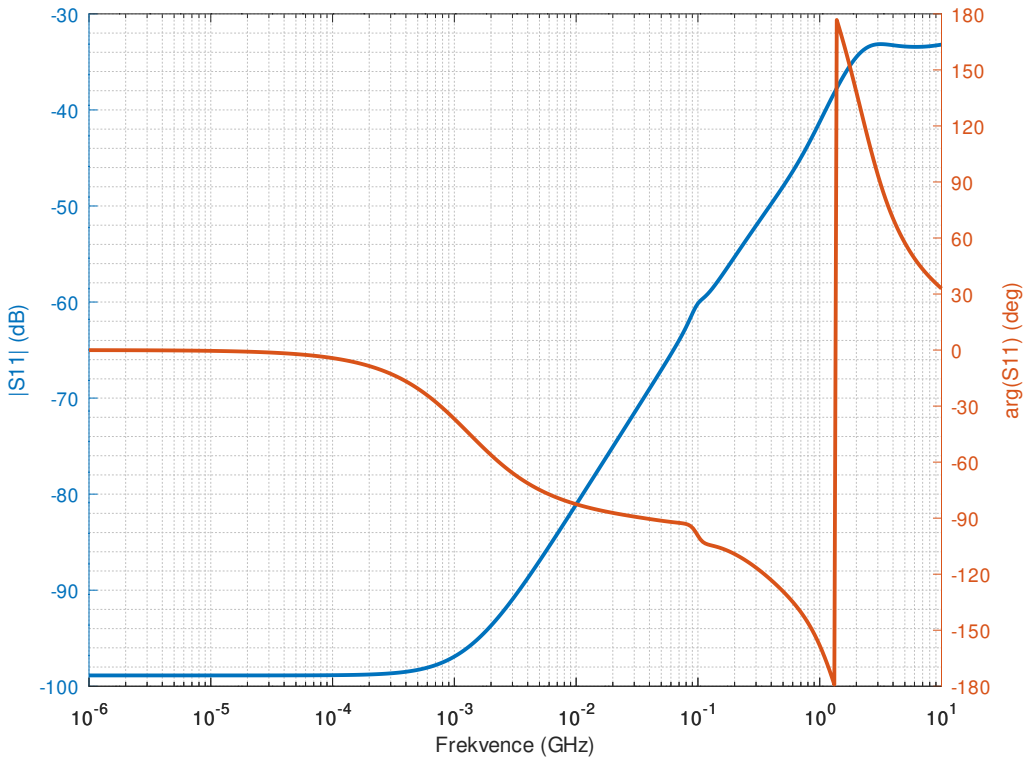
[picture p171: page 1]
Frekvence (GHz); arg(S11) (deg)
