MR-DOS/TDR_diploma_thesis/LaTeX/images/noise_cal_avg1-eps-converted-to.pdf

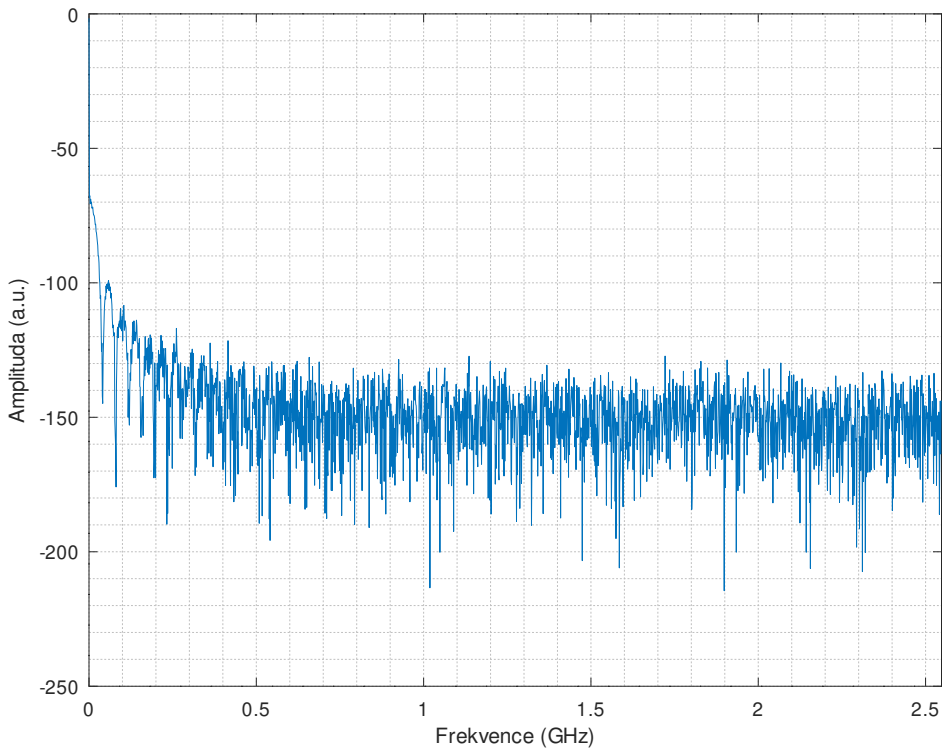
[picture p172: page 1]
Frekvence (GHz); Amplituda (a.u.)
