MR-DOS/TDR_diploma_thesis/LaTeX/images/noise_cal_avg64-eps-converted-to.pdf

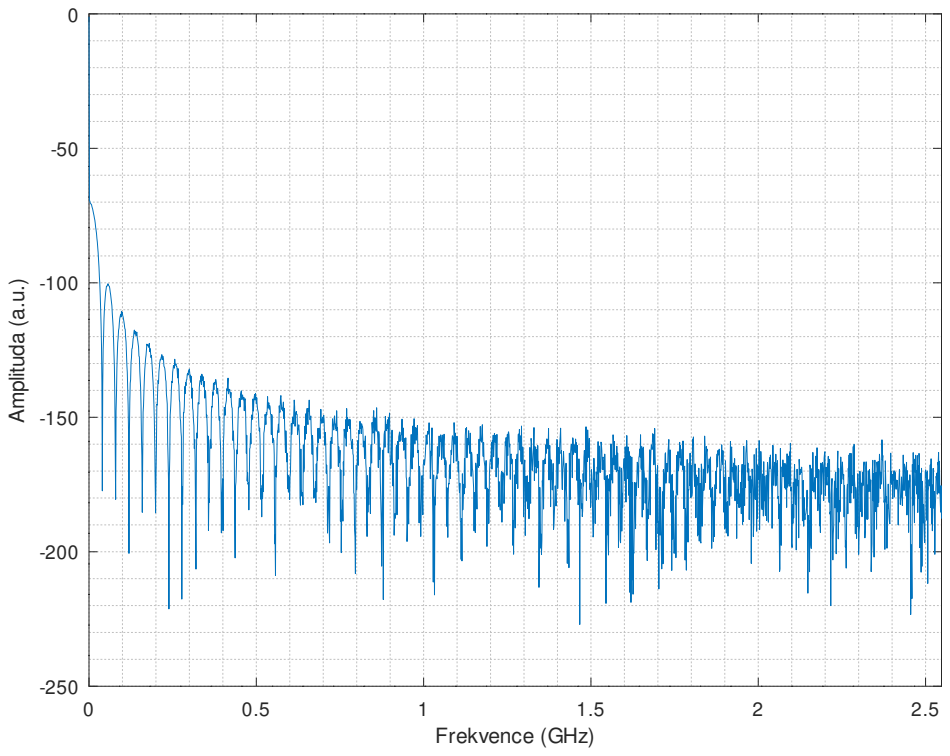
[picture p173: page 1]
Frekvence (GHz); Amplituda (a.u.)
