MR-DOS/TDR_diploma_thesis/LaTeX/images/noise_cal_comparison-eps-converted-to.pdf

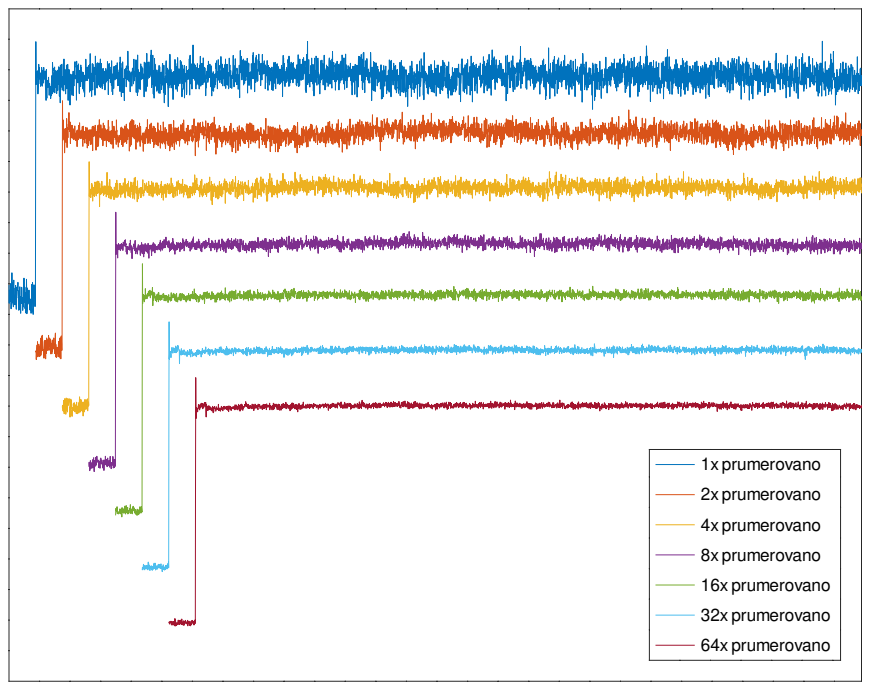
[picture p174: page 1]
1x prumerovano; 2x prumerovano; 4x prumerovano; 8x prumerovano; 16x prumerovano; 32x prumerovano; 64x prumerovano
