MR-DOS/TDR_diploma_thesis/LaTeX/images/noise_comparison-eps-converted-to.pdf

1x prumerovano; 2x prumerovano; 4x prumerovano; 8x prumerovano; 16x prumerovano; 32x prumerovano; 64x prumerovano
