MR-DOS/TDR_diploma_thesis/LaTeX/images/noise_raw_avg1-eps-converted-to.pdf

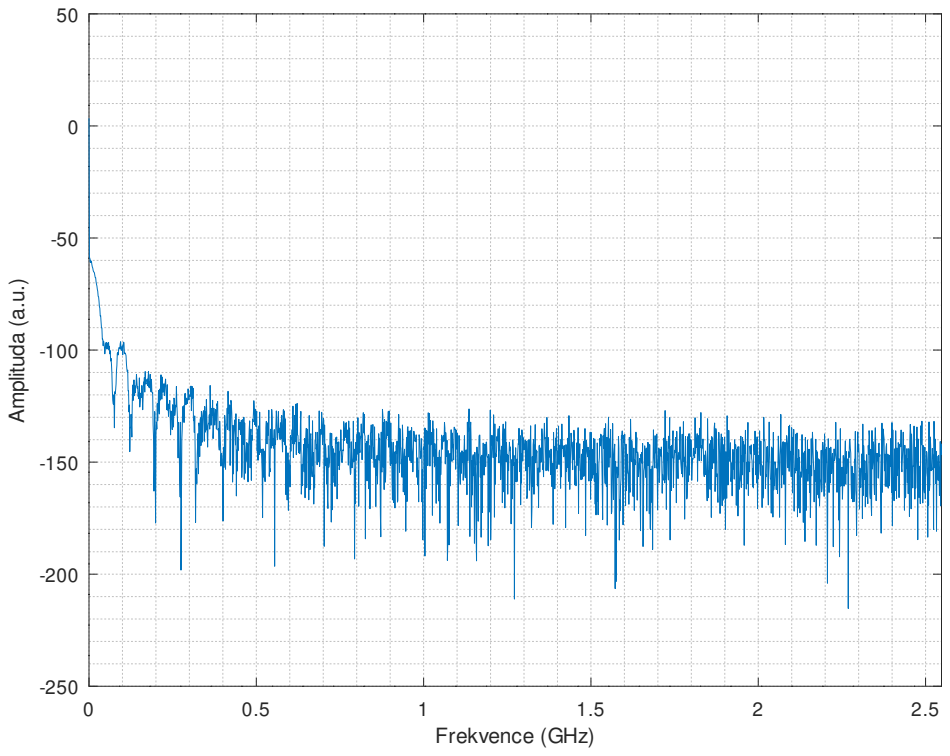
[picture p175: page 1]
Frekvence (GHz); Amplituda (a.u.)
