MR-DOS/TDR_diploma_thesis/LaTeX/images/noise_raw_avg64-eps-converted-to.pdf

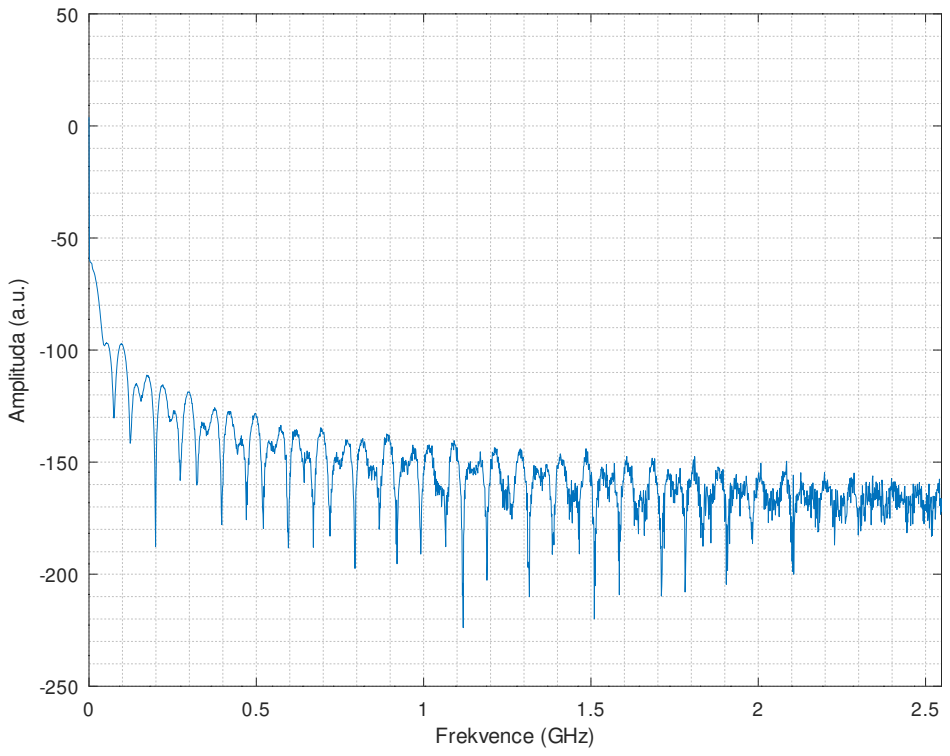
[picture p176: page 1]
Frekvence (GHz); Amplituda (a.u.)
