MR-DOS/TDR_diploma_thesis/LaTeX/images/error_box.pdf

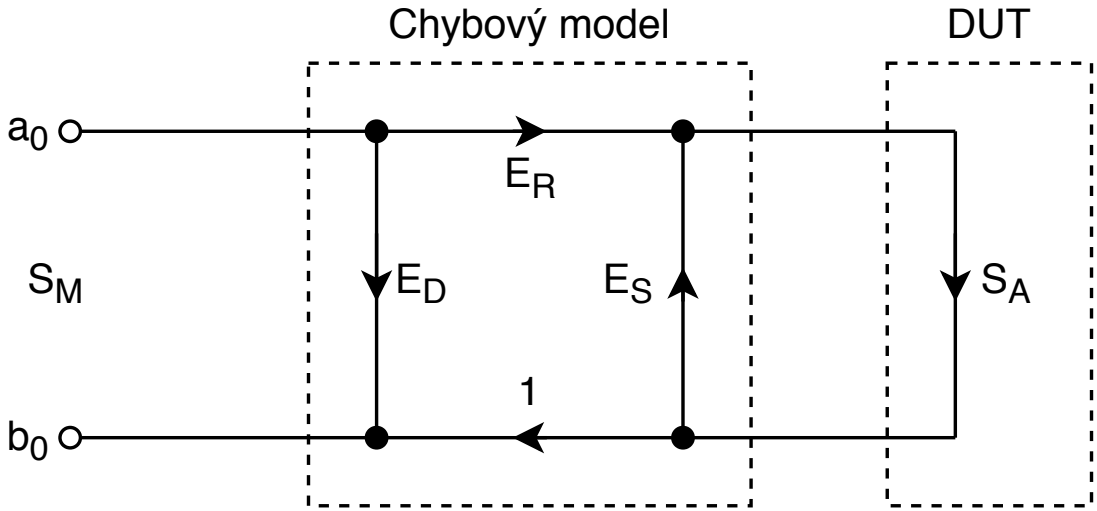
[picture p178: page 1]
Chybový model; DUT
