MR-DOS/TDR_diploma_thesis/LaTeX/images/erf-eps-converted-to.pdf

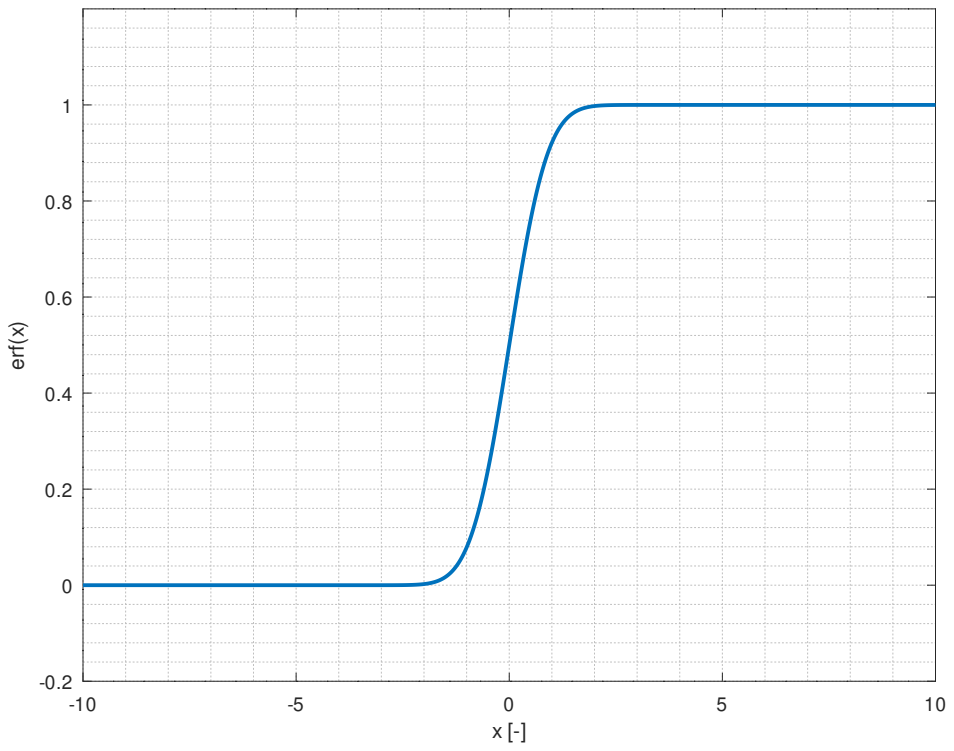
[picture p179: page 1]
erf(x)
