MR-DOS/TDR_diploma_thesis/LaTeX/images/gauss-eps-converted-to.pdf

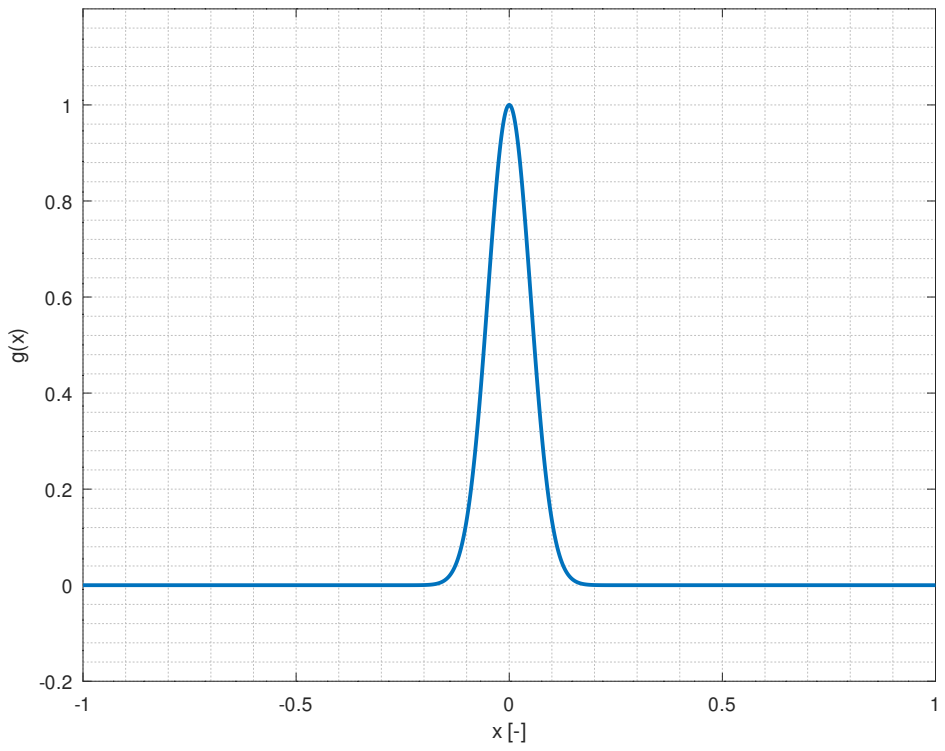
[picture p180: page 1]
