MR-DOS/TDR_diploma_thesis/LaTeX/images/onereflectionsample-eps-converted-to.pdf

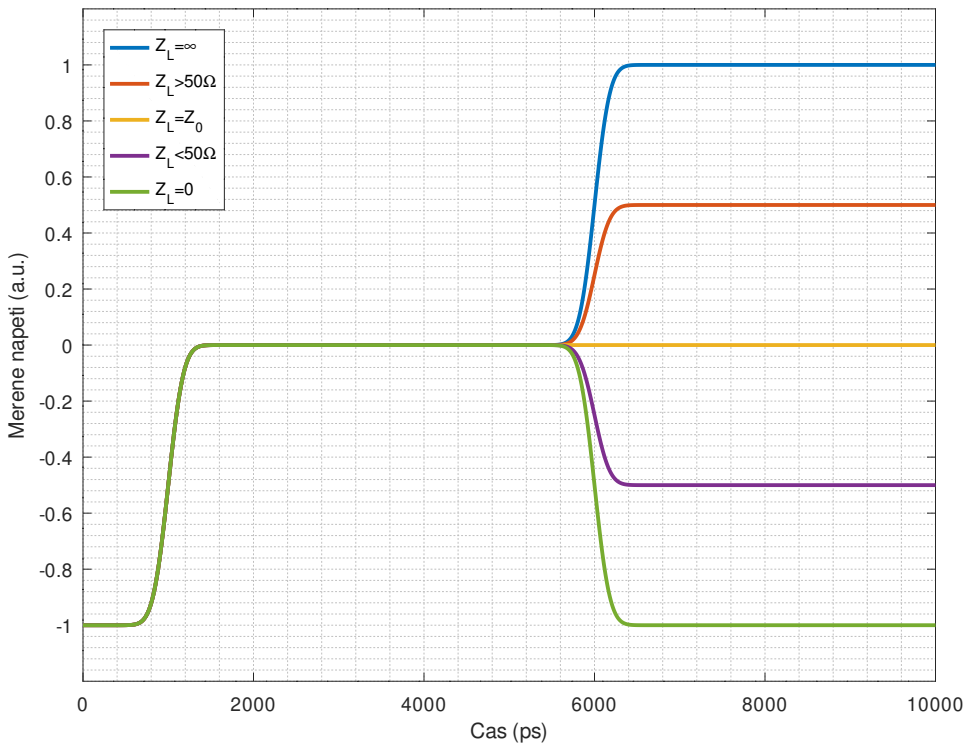
[picture p181: page 1]
Cas (ps); Merene napeti (a.u.)

Z =∞
Z >50Ω
Z =Z0

Z =0
