MR-DOS/TDR_diploma_thesis/LaTeX/images/samplecomplexresponse-eps-converted-to.pdf

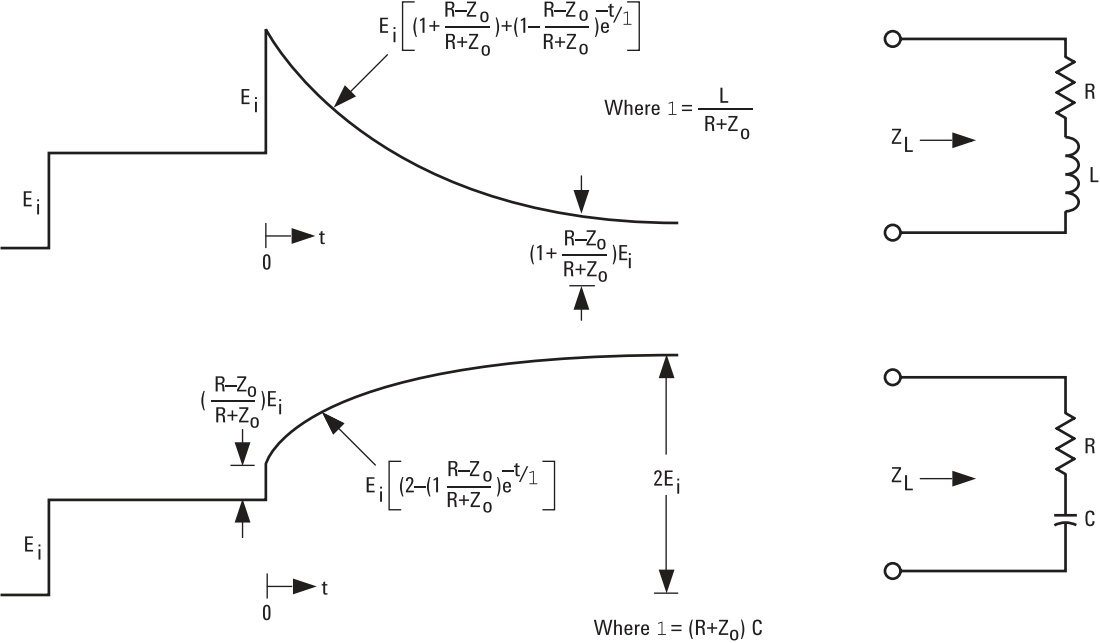
[picture p182: page 1]
