MR-DOS/TDR_diploma_thesis/LaTeX/images/separableunitstep-eps-converted-to.pdf

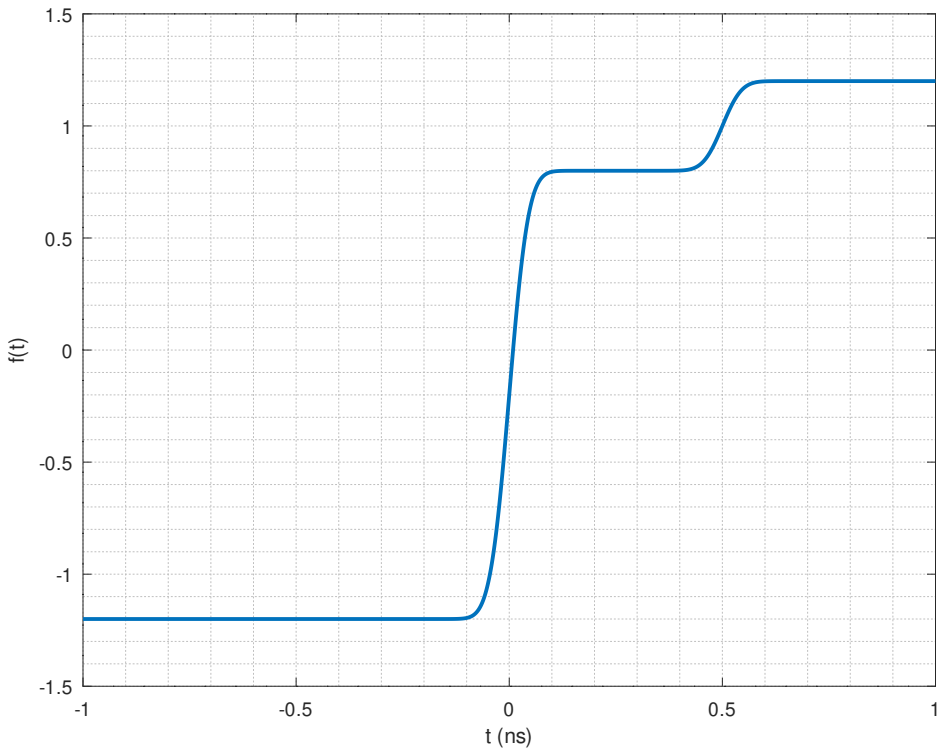
[picture p183: page 1]
