MR-DOS/TDR_diploma_thesis/LaTeX/images/sinc-eps-converted-to.pdf

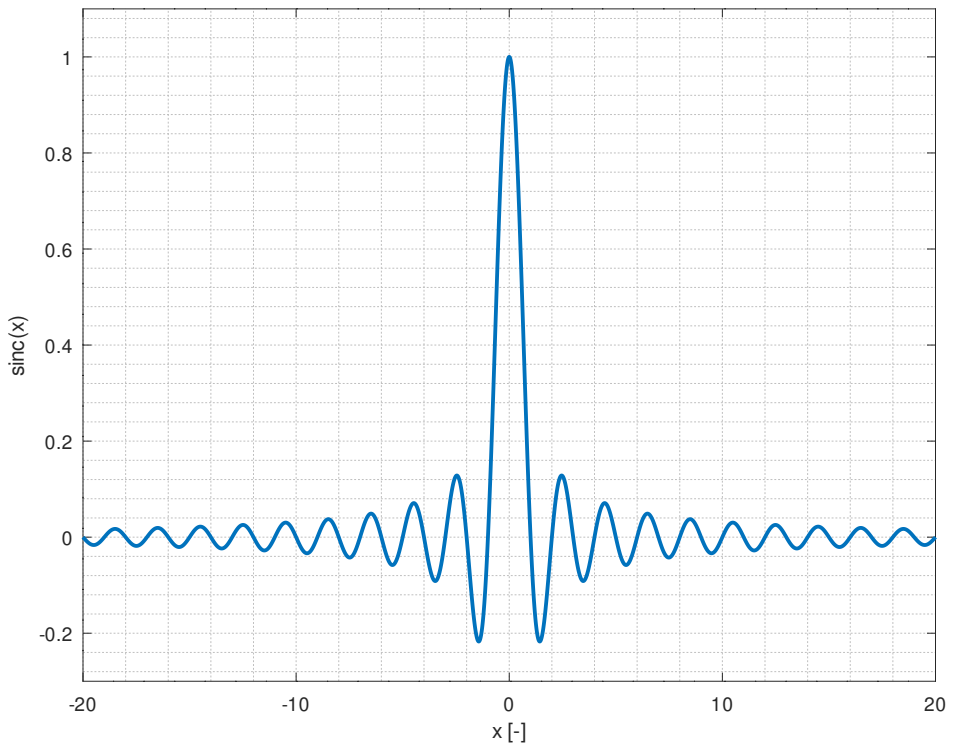
[picture p184: page 1]
sinc(x)
