MR-DOS/TDR_diploma_thesis/LaTeX/images/whitenoise-eps-converted-to.pdf

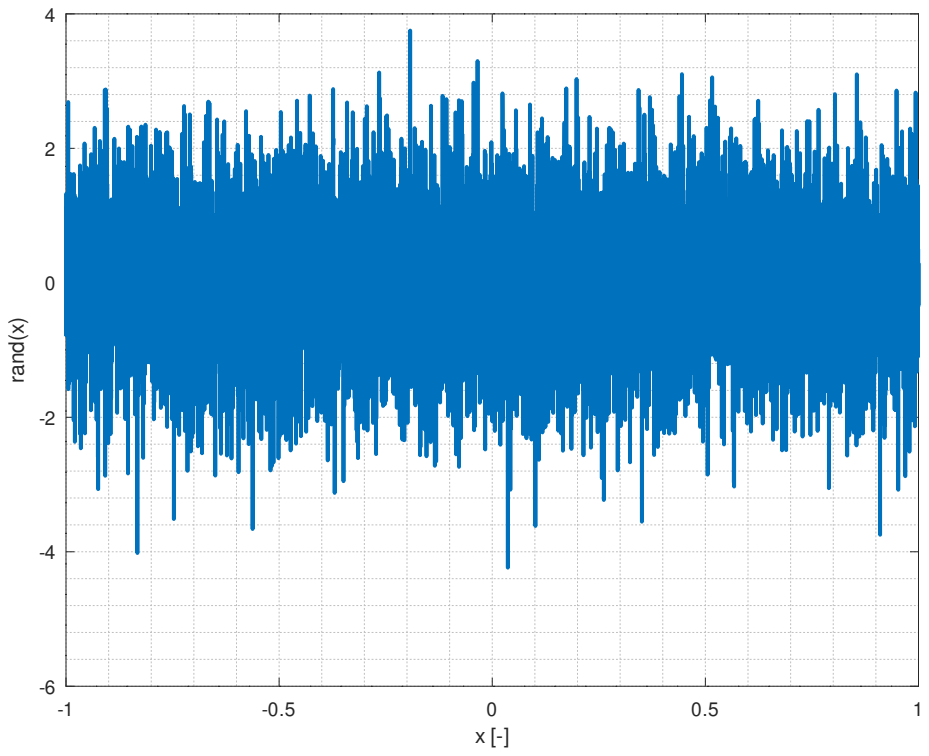
[picture p185: page 1]
rand(x)
