MR-DOS/TDR_diploma_thesis/LaTeX/images/whitenoisecorr-eps-converted-to.pdf

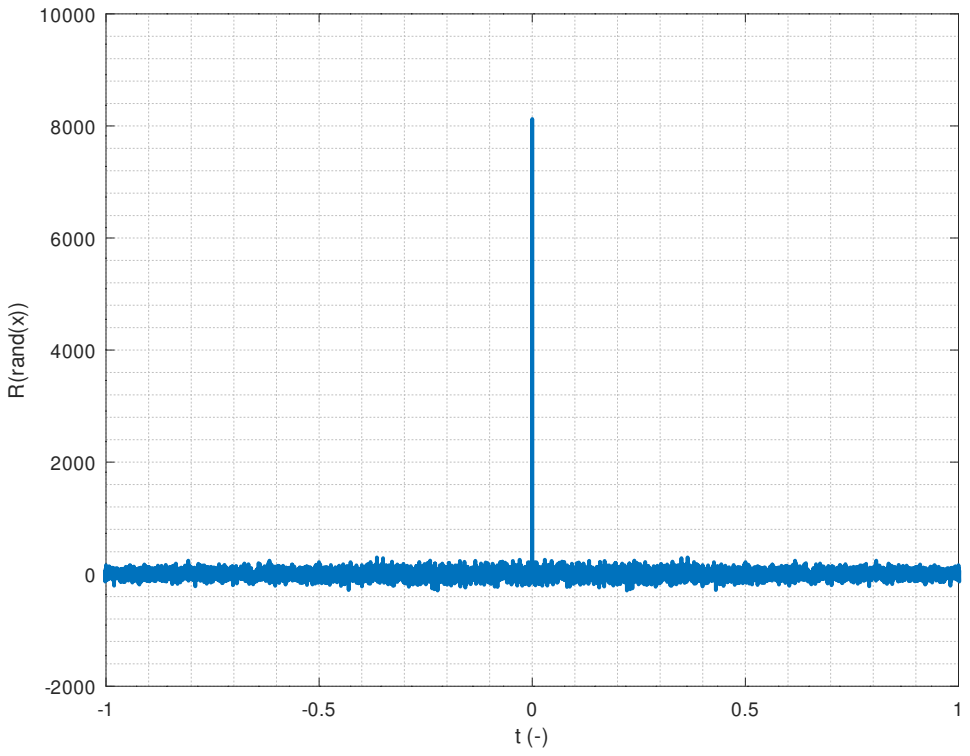
[picture p186: page 1]
R(rand(x))
