MR-DOS/TDR_diploma_thesis/LaTeX/images/AD8309_error-eps-converted-to.pdf

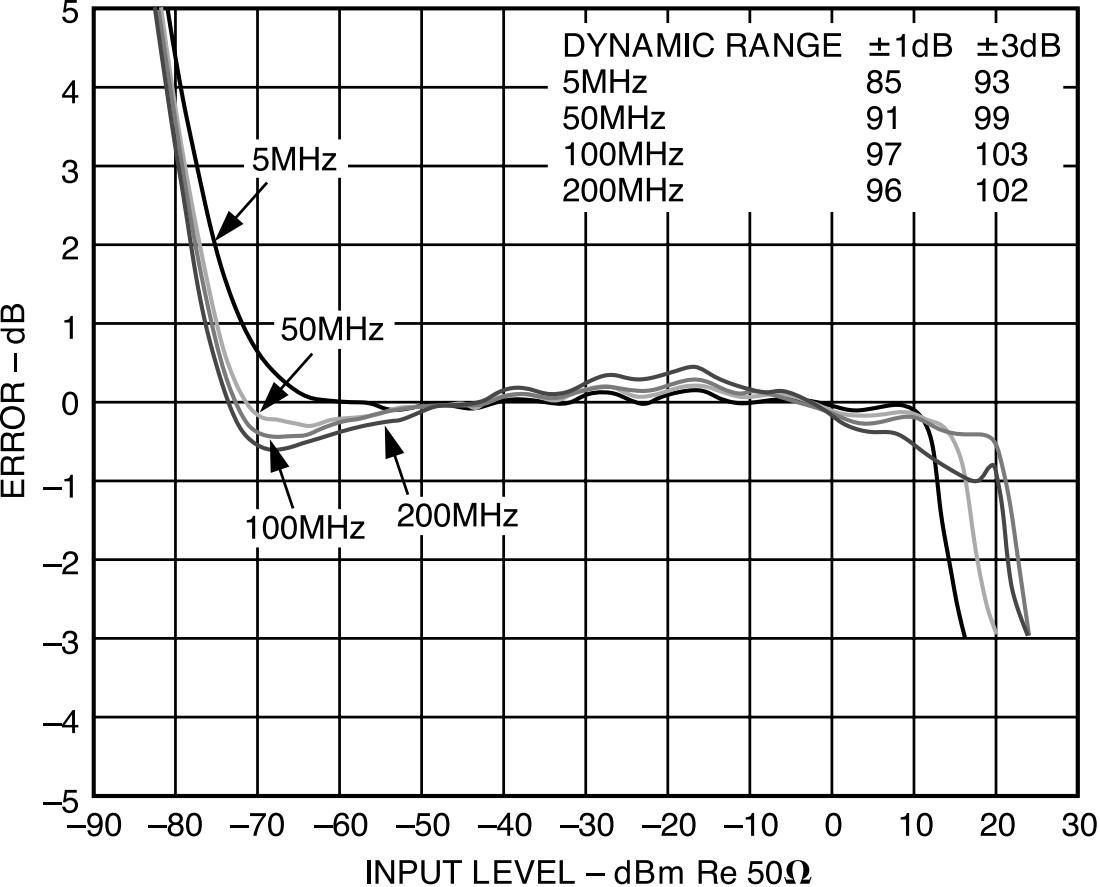
[picture p187: page 1]
