MR-DOS/TDR_diploma_thesis/LaTeX/images/AD8309_function-eps-converted-to.pdf

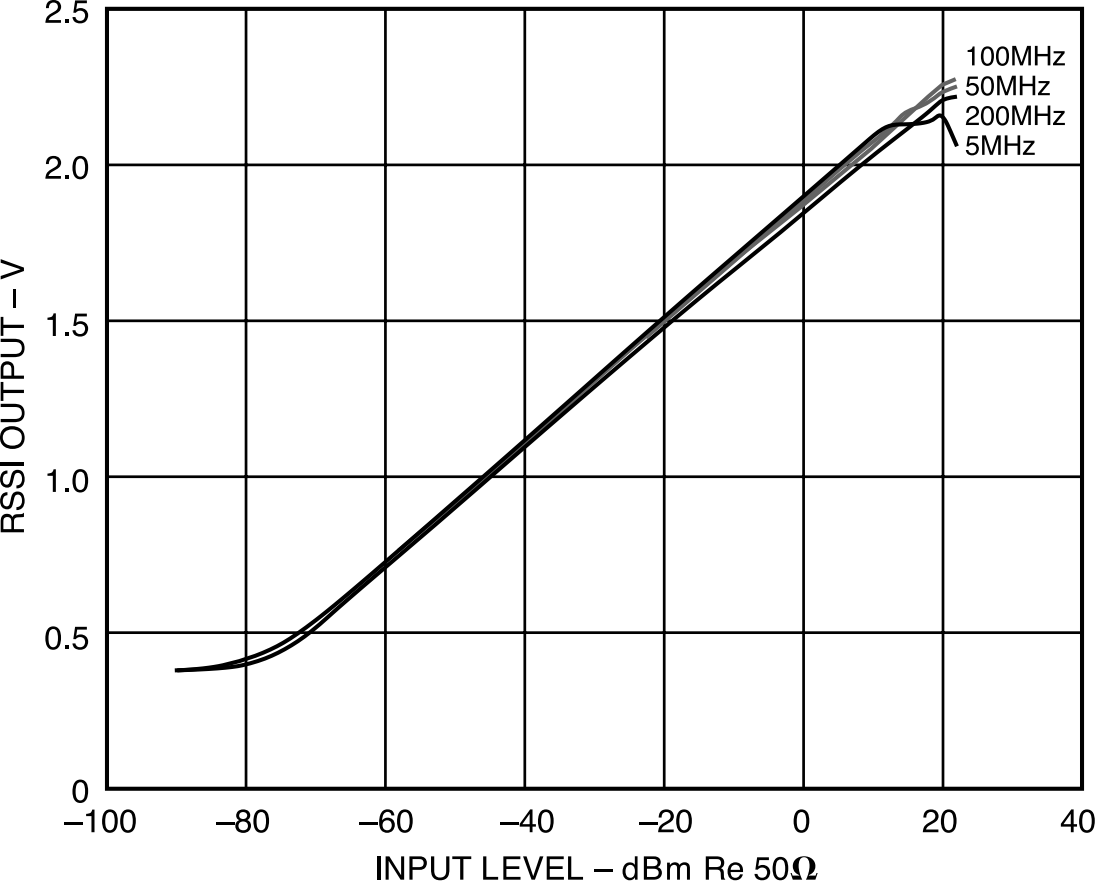
[picture p188: page 1]
