MR-DOS/TDR_diploma_thesis/LaTeX/images/redriver-eps-converted-to.pdf

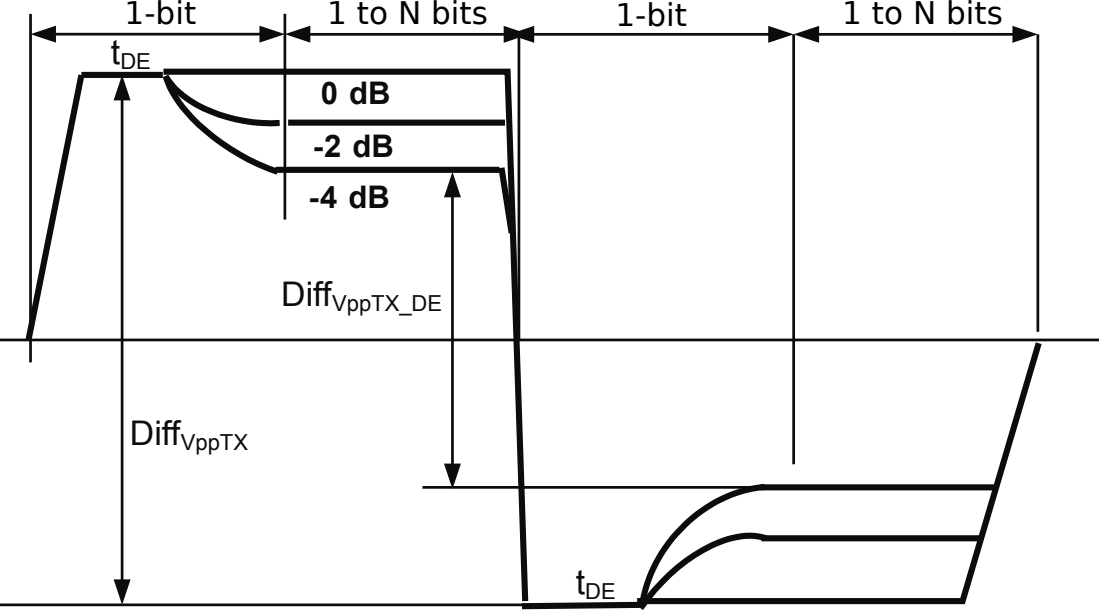
[picture p189: page 1]
DiffVppTX; DiffVppTX_DE; tDE; 1-bit; 1 to N bits
