MR-DOS/TDR_diploma_thesis/LaTeX/images/averaging_float_difference_error-eps-converted-to.pdf

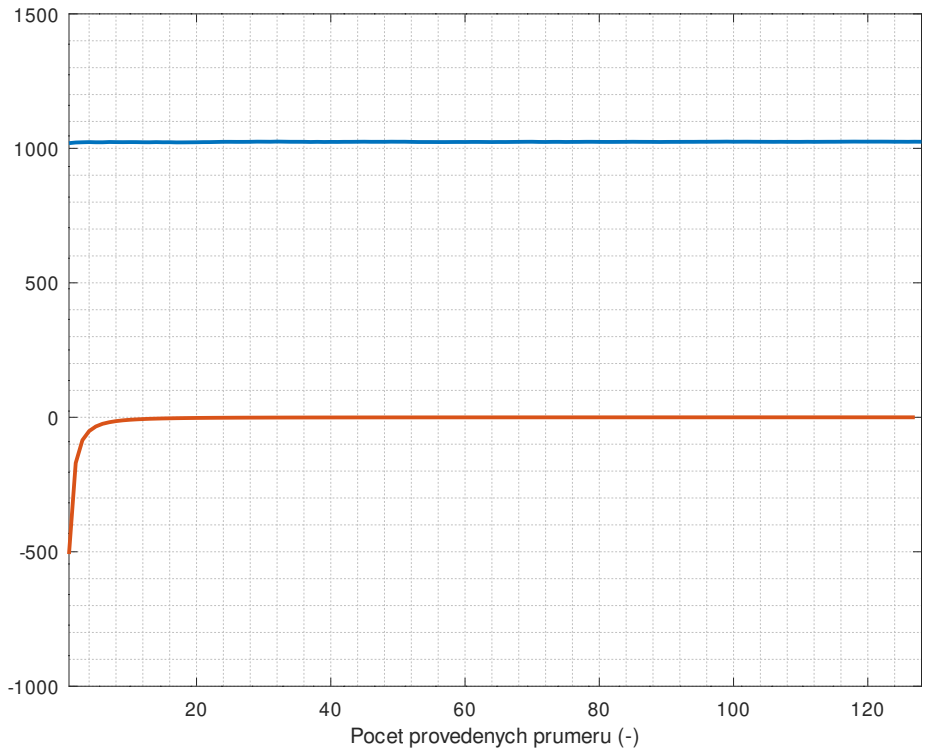
[picture p190: page 1]

Pocet provedenych prumeru (-)
