MR-DOS/TDR_diploma_thesis/LaTeX/images/averaging_integer_difference_error-eps-converted-to.pdf

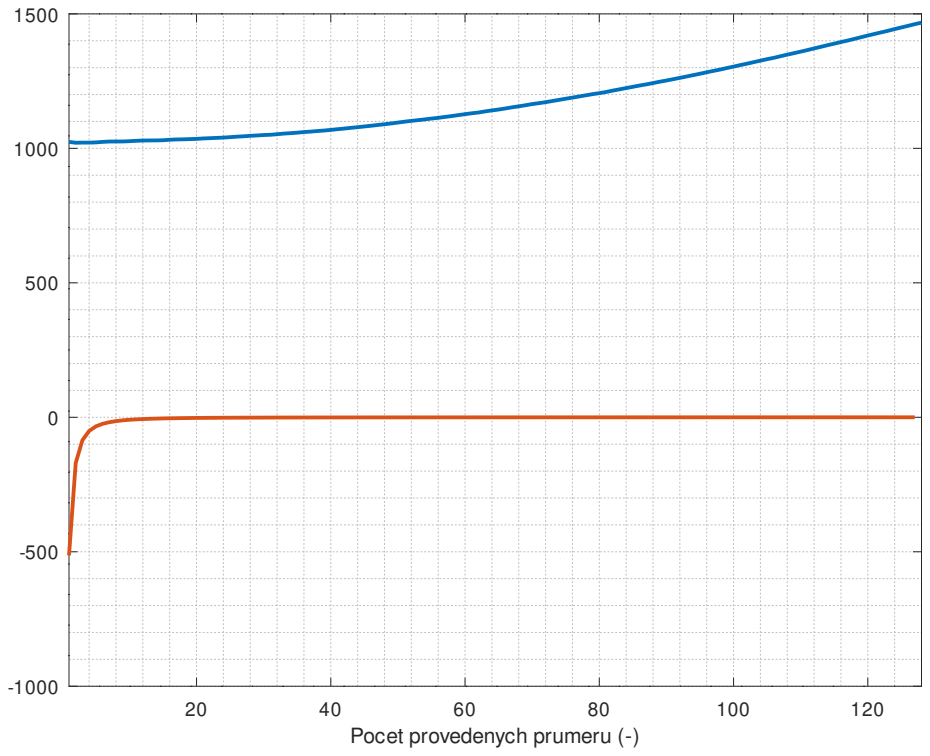
[picture p191: page 1]

Pocet provedenych prumeru (-)
