MR-DOS/TDR_diploma_thesis/LaTeX/images/microcontroller_section-eps-converted-to.pdf

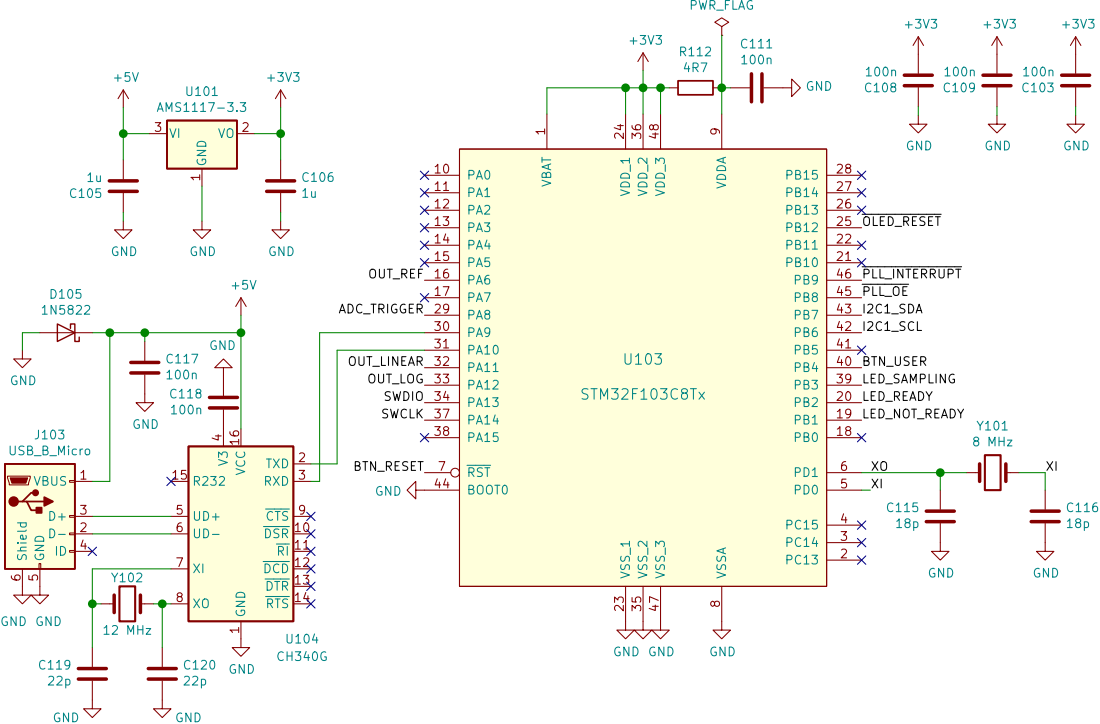
[picture p192: page 1]
