MR-DOS/TDR_diploma_thesis/LaTeX/images/rising_edge_port_load-eps-converted-to.pdf

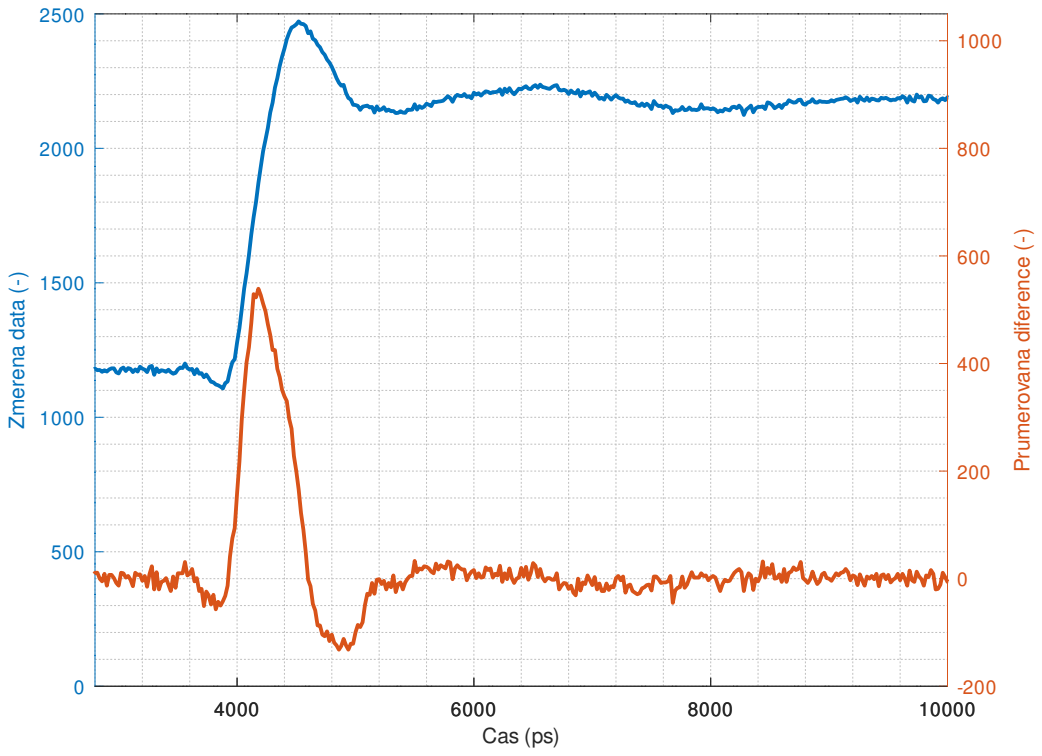
[picture p193: page 1]
Zmerena data (-); Cas (ps); Prumerovana diference (-)
