MR-DOS/TDR_diploma_thesis/LaTeX/images/log_function_graph_whole-eps-converted-to.pdf

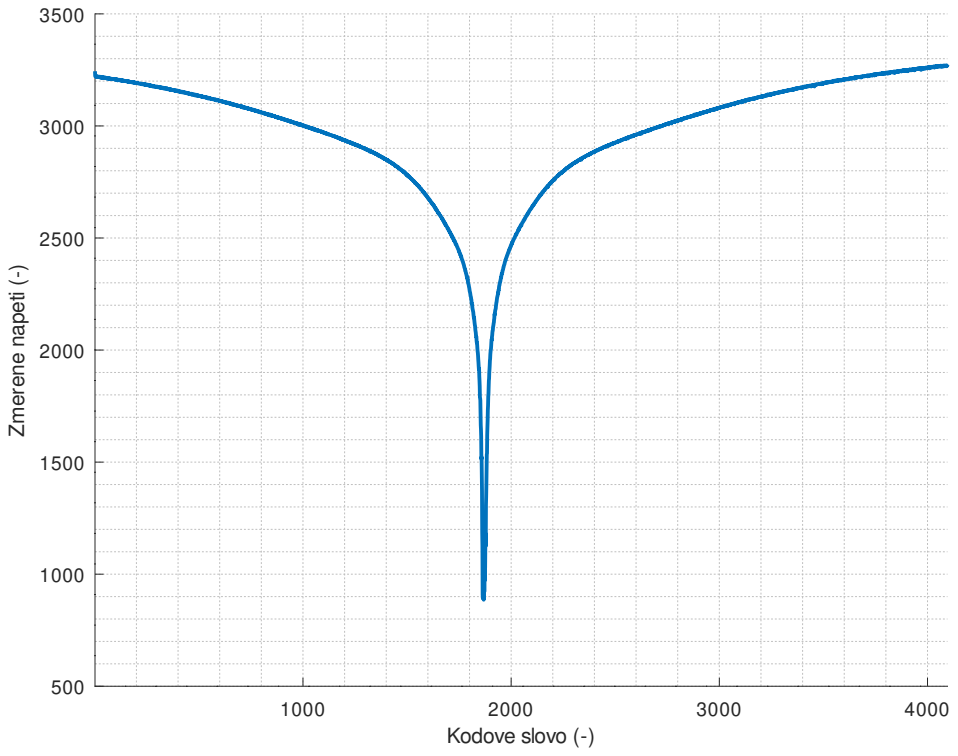
[picture p194: page 1]
Kodove slovo (-); Zmerene napeti (-)
