MR-DOS/TDR_diploma_thesis/LaTeX/images/log_function_graph_zoomed-eps-converted-to.pdf

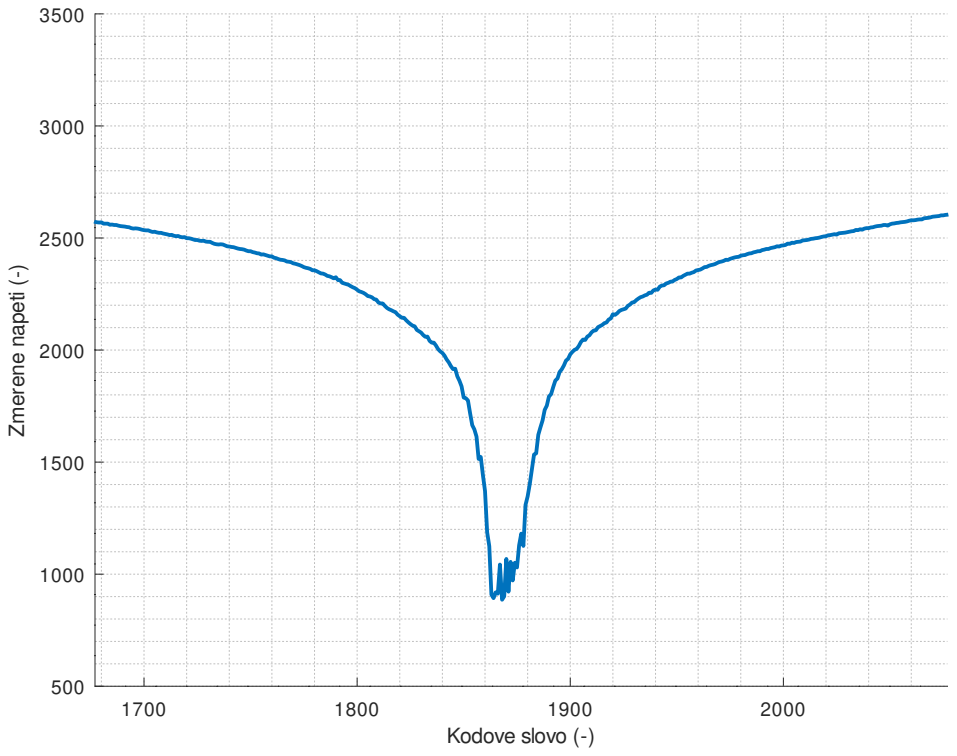
[picture p195: page 1]
Kodove slovo (-); Zmerene napeti (-)
