MR-DOS/TDR_diploma_thesis/LaTeX/images/secondary_sampler_section-eps-converted-to.pdf

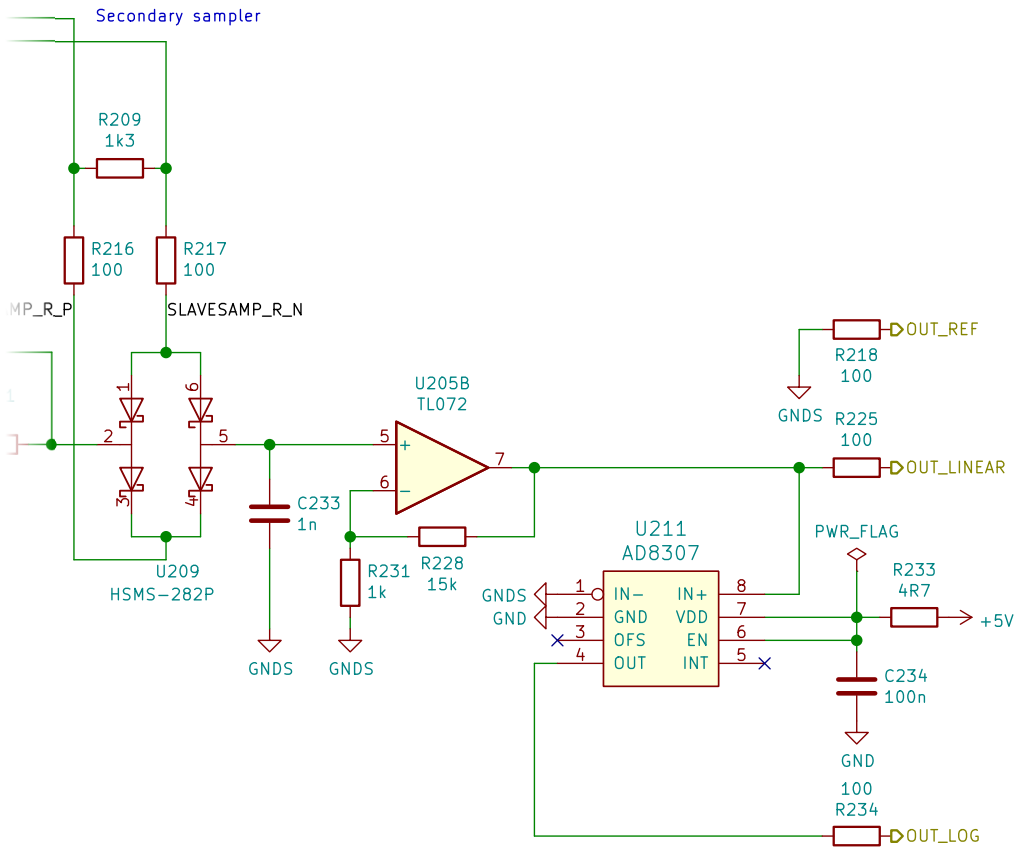
[picture p196: page 1]
