MR-DOS/TDR_diploma_thesis/LaTeX/images/current_source_section-eps-converted-to.pdf

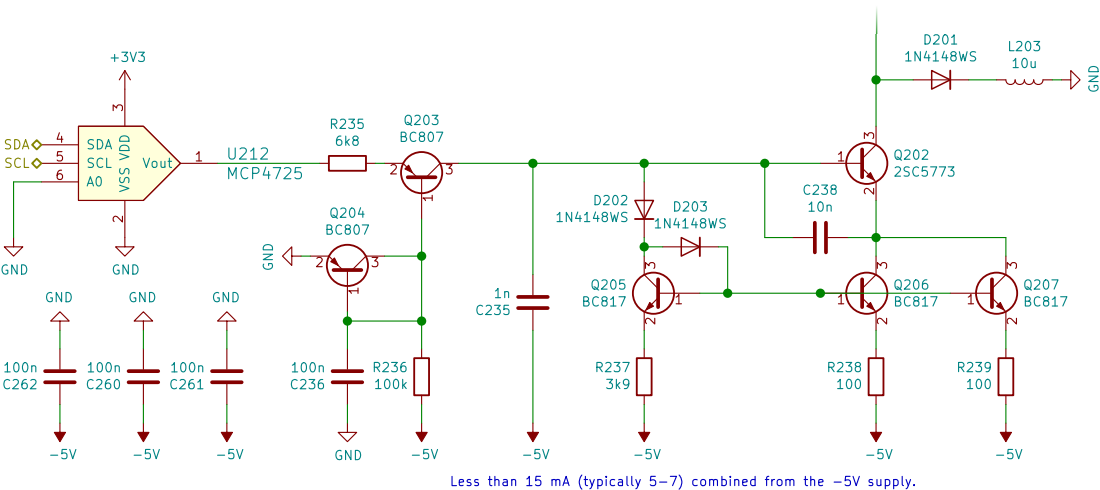
[picture p197: page 1]
