MR-DOS/TDR_diploma_thesis/LaTeX/images/power_supply_section-eps-converted-to.pdf

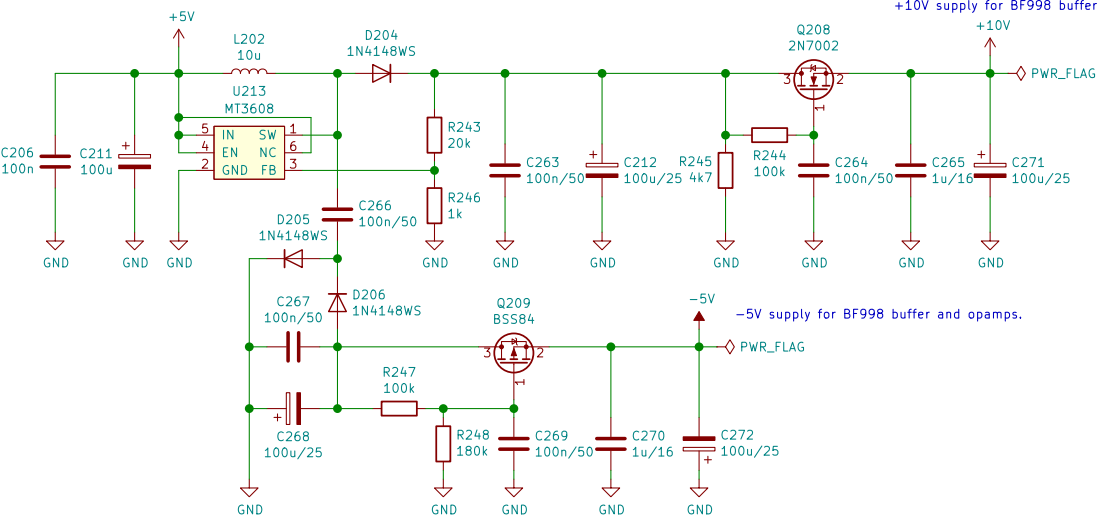
[picture p198: page 1]
