MR-DOS/TDR_diploma_thesis/LaTeX/images/sampler_section-eps-converted-to.pdf

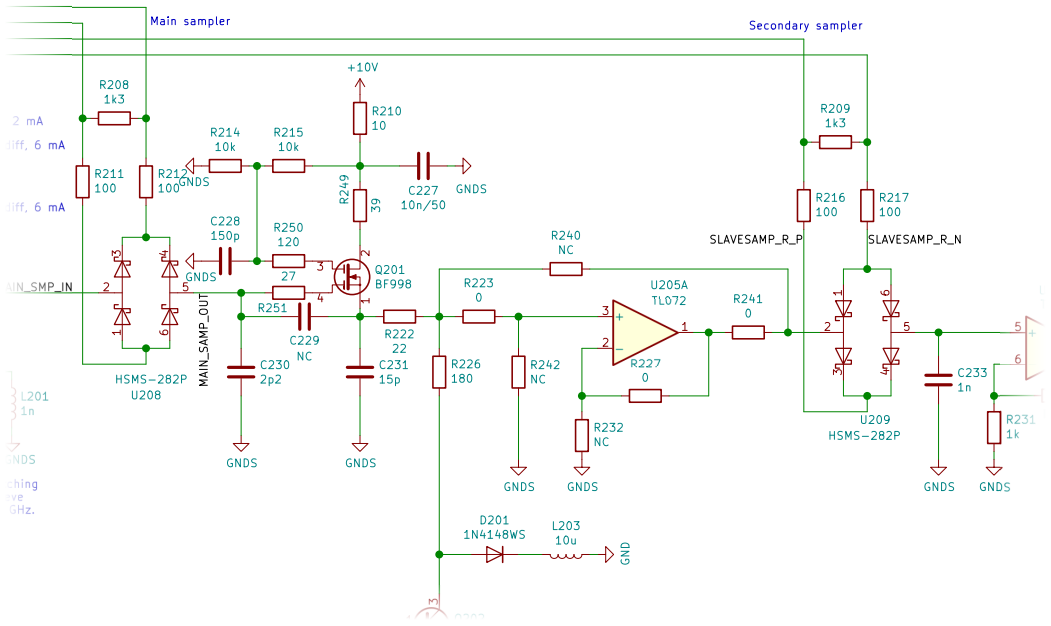
[picture p199: page 1]
