MR-DOS/TDR_diploma_thesis/LaTeX/images/match_section-eps-converted-to.pdf

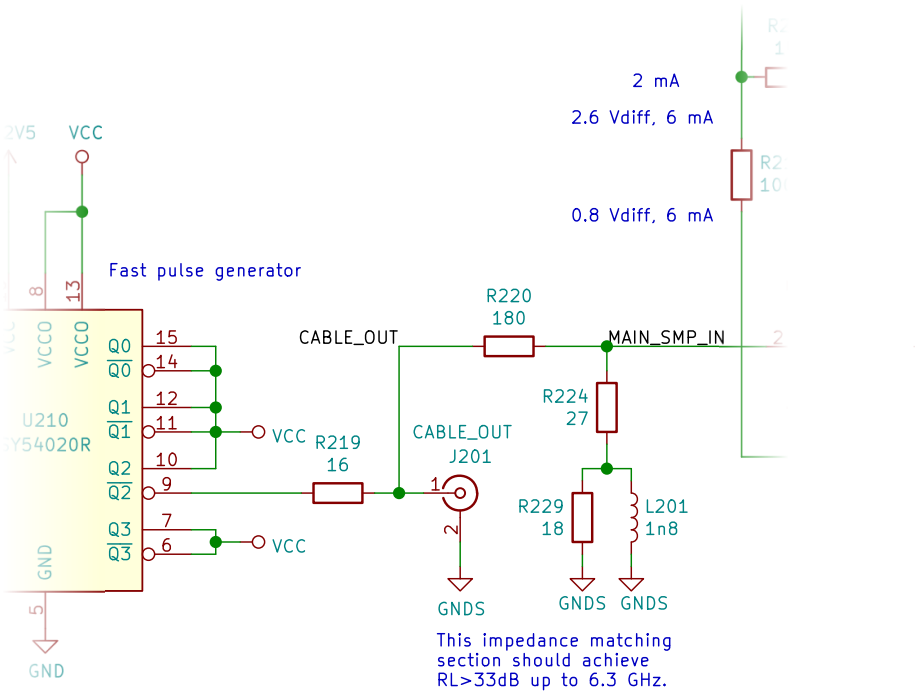
[picture p200: page 1]
