MR-DOS/TDR_diploma_thesis/LaTeX/images/pulse_generator_section-eps-converted-to.pdf

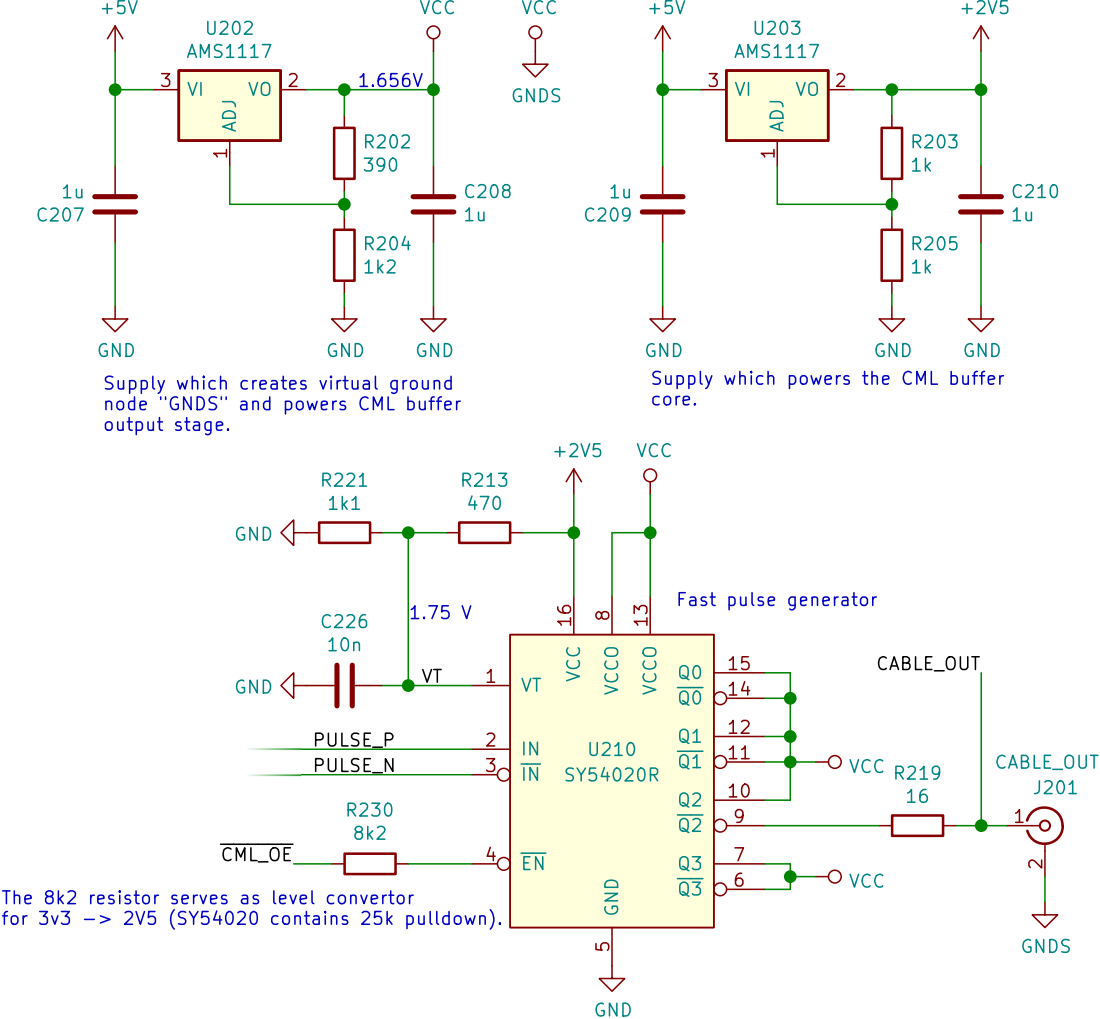
[picture p201: page 1]
