MR-DOS/TDR_diploma_thesis/LaTeX/images/timing_section-eps-converted-to.pdf

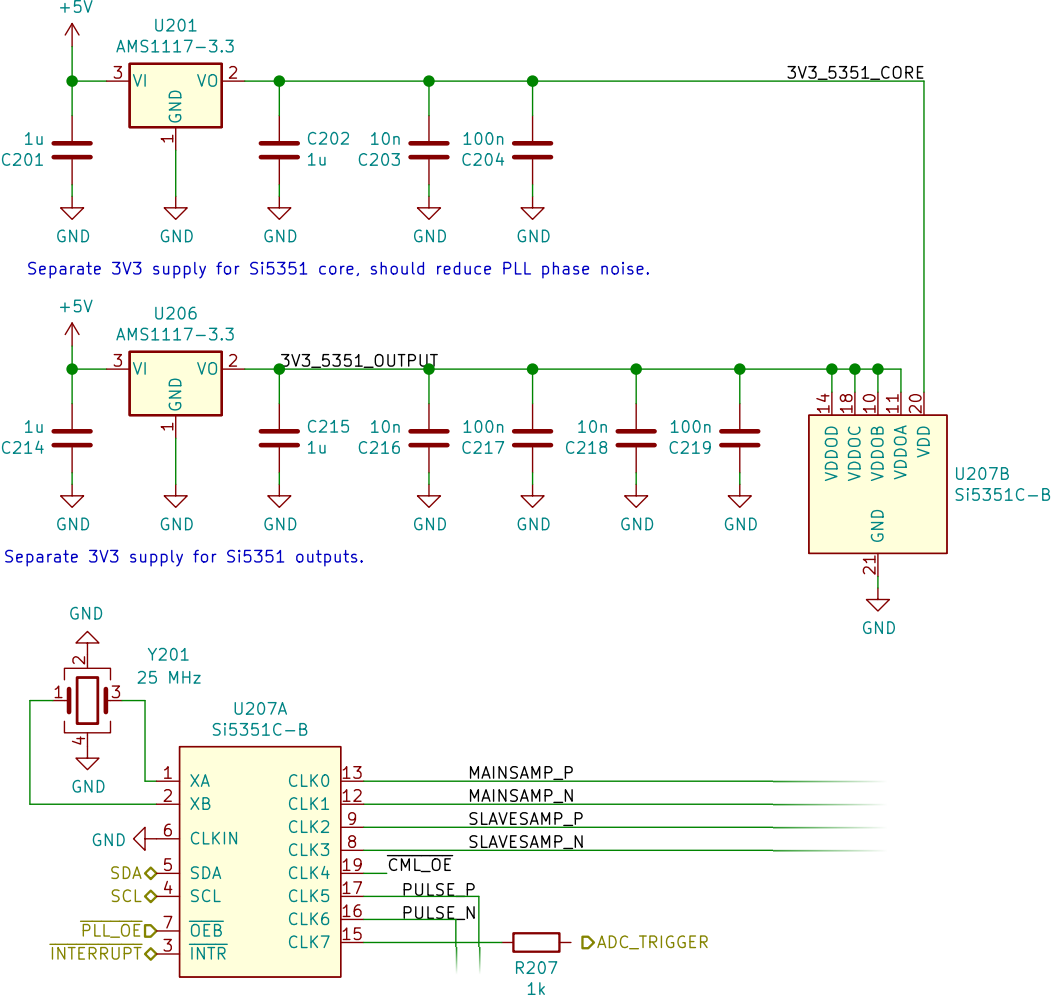
[picture p202: page 1]
