MR-DOS/TDR_diploma_thesis/LTSpice/sim/Draft11.asc

C1: cap; 0p7
C2: cap; 0p7
C3: cap; 0p7
C4: cap; 0p7
C5: cap; 1p
C6: cap; 15p
C7: cap; 2p
C8: cap; 2p
I1: current; PULSE(0 8m 2n 100p 100p 100n 200n); AC -1
L1: ind; 0n8
L2: ind; 0n8
L3: ind; 1n5
L4: ind; 1n5
L5: ind; 1n5
L6: ind; 1n5
L7: ind; 0n8
L8: ind; 0n8
L9: ind; 1n
L10: ind; 1n
L12: ind2; 1µ
L13: ind2; 1µ
R1: res; 6
R2: res; 4.5
R3: res; 150
R4: res; 6
R5: res; 4.5
R6: res; 150
R7: res; 6
R8: res; 4.5
R9: res; 6
R10: res; 4.5
R11: res; 1k3
R12: res; 15Meg
R13: res; 1Meg
R14: res; 20
R15: res; 240
R16: res; 2.2
R18: res; 12
R19: res; 50
R32: res; 15
Named nets: 0, IN
.ac oct 100 10Meg 10G
;tran 0 20n 0 5p
-20*log10(abs(((V(in)/I(I1))-50)/(50+(V(in)/I(I1)))))
k1 L12 L13 -1
