MR-DOS/TDR_diploma_thesis/LTSpice/sim/Draft12a.asc

C1: cap; 0p7
C2: cap; 0p7
C3: cap; 0p7
C4: cap; 0p7
C5: cap; 0.25p
C7: cap; 1p5
C8: cap; 1p5
I1: current; PULSE(0 8m 2n 100p 100p 100n 200n); AC 1
L1: ind; 0n8
L2: ind; 0n8
L3: ind; 1n5
L4: ind; 1n5
L5: ind; 1n5
L6: ind; 1n5
L7: ind; 0n8
L8: ind; 0n8
L9: ind; 1n8
L12: ind2; 1µ
L13: ind2; 1µ
R1: res; 6
R2: res; 4.5
R3: res; 150
R4: res; 6
R5: res; 4.5
R6: res; 150
R7: res; 6
R8: res; 4.5
R9: res; 6
R10: res; 4.5
R11: res; 1k3
R14: res; 27
R15: res; 180
R18: res; 16
R19: res; 50
R32: res; 18
Named nets: 0, IN
.ac oct 100 10Meg 10G
;tran 0 20n 0 5p
-20*log10(abs(((V(in)/I(I1))-50)/(50+(V(in)/I(I1)))))
k1 L12 L13 -1
