MR-DOS/TDR_diploma_thesis/LTSpice/sim/Draft14.asc

C1: cap; 33p
C2: cap; 6p8
Q1: npn; BC847A
Q2: npn; BC847A
Q3: pnp; BC807-40T116
R1: res; 410
R2: res; 4k7
R3: res; 4k7
R4: res; 330
R5: res; 220
R6: res; 4k7
R7: res; 4k7
R8: res; 180k
R9: res; 330
R10: res; 330
R11: res; 3.3
T1: tline; Td=64u Z0=330
V1: voltage; 5
V2: voltage; PULSE(0 5 0 5n 5n 1u 2u)
Named nets: 0, OUT, IN
.tran 0 70u 64u 10n
.step param emitres 330 470 20
