MR-DOS/TDR_diploma_thesis/LTSpice/sim/Draft15.asc

C1: cap; 100n
C2: cap; 100n
C3: cap; 1µ
C6: cap; 680n
C7: cap; 680n
C8: cap; 680n
C9: cap; 100n
C10: cap; 10µ
C11: cap; 100n
D1: diode; 1N4148
D2: diode; 1N4148
D3: diode; 1N4148
Q1: npn; BC817-40
Q3: npn; BC547B
Q4: npn; BC547B
Q5: npn; BC817-40
Q6: npn; BC817-40
Q7: pnp; BC807-40
Q8: pnp; BC807-40
Q9: npn; BC817-40
Q10: npn; BC817-40
Q11: npn; BC817-40
R1: res; 1Meg
R2: res; 99k
R3: res; 3k3
R4: res; 330k
R5: res; 6k8
R6: res; 1Meg
R7: res; 120k
R8: res; 0.1
R12: res; 10k
R13: res; 10k
R14: res; 3.3Meg
R15: res; 3k6
R16: res; 120k
R17: res; 10k
R18: res; 15k
R20: res; 1Meg
R22: res; 1k
R23: res; 3k9
R24: res; 1k
R25: res; 100k
R26: res; 10k
R27: res; 1k
R28: res; 1k
R29: res; 10k
R31: res; 1Meg
R32: res; 22k
R33: res; 2k2
R34: res; 1k
V1: voltage; 9
V2: voltage; 9
V3: voltage; SINE(0 0.25 1k); AC 1
Named nets: 0, V+, V-
.tran 0 10 0 startup
;ac dec 50 1 20k
