MR-DOS/TDR_diploma_thesis/LTSpice/sim/Draft18.asc

C1: cap; 0.07p
C2: cap; 0.07p
C3: cap; 0.07p
C4: cap; 0.07p
C5: cap; 2p2
C6: cap; 2p
C7: cap; 2p
C8: cap; 10n
C9: cap; 150p
C10: cap; 27p
C11: cap; 73f
C12: cap; 120f
C13: cap; 120f
C14: cap; 1n
C15: cap; 1n
D1: diode; SMS3923-081
D2: diode; SMS3923-081
D3: diode; SMS3923-081
D4: diode; SMS3923-081
D5: diode; 1N4148
D6: diode; BAT17_CHIP
D7: diode; BAT17_CHIP
I1: current; {bias}
I2: current; {bias}
I3: current; 10m
L1: ind; 0.3n
L2: ind; 1n
L3: ind; 1n
L4: ind; 0.3n
L5: ind; 1n
L6: ind; 0.3n
L7: ind; 1n
L8: ind; 0.3n
L9: ind; 1n
L10: ind; 1n
L11: ind; 1µ
L12: ind; 1n
L13: ind; 770p
L14: ind; 770p
L15: ind; 490p
L16: ind; 560p
L17: ind; 560p
R1: res; 82
R2: res; 100
R3: res; 100
R4: res; 56
R5: res; 50
R6: res; 420Meg
R7: res; 10
R8: res; 10k
R9: res; 10k
R10: res; 1m
R11: res; 360
R12: res; 50
R13: res; 15
R14: res; 10
R15: res; 180
R16: res; 39
R17: res; 1k
R18: res; 3k9
R19: res; 27
R20: res; 420Meg
R21: res; 100
R22: res; 100
T1: tline; Td=280p Z0=50
U1: BF998
V1: voltage; PULSE(0 400m 100p 35p 35p 5u 10u)
V2: voltage; 6.5
V3: voltage; ""; AC 1
Named nets: 0, samplecap, BF_source
.model SMS3923-081 D(Is=5E-9 Rs=10 N=1.05 Tt=8E-11 Cj0=0.9p M=0.24 Eg=0.69 Xti=2 Fc=0.5 Bv=46 Ibv=1E-5 Vj=0.64)
;op
.tran 0 3n 0 1p
.SUBCKT BF998 1 2 3 4
        L10          1 10   L=0.12N
        L20          2 20   L=0.12N
        L30          3 30   L=0.12N
        L40          4 40   L=0.12N
        L11         10 11   L=1.20N
        L21         20 21   L=1.20N
        L31         30 31   L=1.20N
        L41         40 41   L=1.20N
        C13         10 30   C=0.085P
        C14         10 40   C=0.085P
        C21         10 20   C=0.017P
        C23         20 30   C=0.085P
        C24         20 40   C=0.005P
        D11         42 11   ZENER
        D12         42 41   ZENER
        D21         32 11   ZENER
        D22         32 31   ZENER
        RS          10 12   R=100
        MOS1        61 41 11 12 GATE1 L=1.1E-6 W=1150E-6
        MOS2        21 31 61 12 GATE2 L=2.0E-6 W=1150E-6
 
.MODEL  ZENER  D  BV=10 CJO=1.2E-12  RS=10
 
.MODEL  GATE1
+  NMOS LEVEL=3 UO=600  VTO=-0.250 NFS=300E9 TOX=42E-9
+  NSUB=3E15 VMAX=140E3 RS=2.0 RD=2.0 XJ=200E-9 THETA=0.11
+  ETA=0.06 KAPPA=2 LD=0.1E-6
+  CGSO=0.3E-9 CGDO=0.3E-9 CBD=0.5E-12 CBS=0.5E-12
 
.MODEL  GATE2 
+  NMOS LEVEL=3 UO=600  VTO=-0.250 NFS=300E9 TOX=42E-9
+  NSUB=3E15  VMAX=100E3 RS=2.0 RD=2.0 XJ=200E-9 THETA=0.11
+  ETA=0.06  KAPPA=2 LD=0.1E-6
+  CGSO=0.3E-9 CGDO=0.3E-9 CBD=0.5E-12 CBS=0.5E-12
 
.ENDS BF998
.SUBCKT BF998 1 2 3 4
        L10          1 10   0.12N
        L20          2 20   0.12N
        L30          3 30   0.12N
        L40          4 40   0.12N
        L11         10 11   1.20N
        L21         20 21   1.20N
        L31         30 31   1.20N
        L41         40 41   L=1.20N
        C13         10 30   0.085P
        C14         10 40   0.085P
        C23         20 30   0.085P
        C24         20 40   0.005P
        D11         42 11   ZENER
        D12         42 41   ZENER
        D21         32 11   ZENER
        D22         32 31   ZENER
        RS          10 12   100
        MOS1        61 41 11 12 GATE1 L=1.1E-6 W=1150E-6
        MOS2        21 31 61 12 GATE2 L=2.0E-6 W=1150E-6
 
.MODEL  ZENER  D  BV=10 CJO=1.2E-12  RS=10
 
.MODEL  GATE1
+  NMOS LEVEL=3 UO=600  VTO=-0.250 NFS=300E9 TOX=42E-9
+  NSUB=3E15 VMAX=140E3 RS=2.0 RD=2.0 XJ=200E-9 THETA=0.11
+  ETA=0.06 KAPPA=2 LD=0.1E-6
+  CGSO=0.3E-9 CGDO=0.3E-9 CBD=0.5E-12 CBS=0.5E-12
 
.MODEL  GATE2
+  NMOS LEVEL=3 UO=600  VTO=-0.250 NFS=300E9 TOX=42E-9
+  NSUB=3E15  VMAX=100E3 RS=2.0 RD=2.0 XJ=200E-9 THETA=0.11
+  ETA=0.06  KAPPA=2 LD=0.1E-6
+  CGSO=0.3E-9 CGDO=0.3E-9 CBD=0.5E-12 CBS=0.5E-12
 
*   BF998 SPICE MODEL OCTOBER 1993 PHILIPS SEMICONDUCTORS
*   ENVELOPE    SOT143 (R)
*   1.: SOURCE;  2.: DRAIN;  3.: GATE 2;  4.: GATE 1;
 
.ENDS BF998
.step param X list 3.3 4.7 6.8 8.2 10 12 15 18 20 22
.meas TRAN TOP FIND V(BF_source) AT=2n7
.meas TRAN BOT FIND V(BF_source) AT=0
.meas TRAN risetime TRIG V(BF_source)=BOT+(TOP-BOT)*0.1 TARG V(BF_source)=BOT+(TOP-BOT)*0.9
.meas PEAK MAX V(samplecap)
;ac dec 50 1k 10G
(V(n004)/I(R5)-50)/(V(n004)/I(R5)+50)
.MODEL BAT17_CHIP D(IS=3.33n N=1.009 RS=2.65 XTI=2.0 EG=0.69
+ CJO=398f M=0.21 VJ=0.224 FC=0.5 TT=3.0p BV=7.0 IBV=10.0u)
.param bias=8m
