MR-DOS/TDR_diploma_thesis/LTSpice/sim/Draft19_2.asc

C1: cap; 2p2
C2: cap; 0.07p
C3: cap; 0.07p
C4: cap; 10p
C18: cap; 0.07p
C19: cap; 0.07p
C20: cap; 0.07p
C21: cap; 0.07p
C22: cap; 2p2
C23: cap; 2p
C24: cap; 2p
C25: cap; 10n
C26: cap; 150p
C27: cap; 27p
C32: cap; 100n
C33: cap; 1n
C34: cap; 10n
D1: diode; SMS3923-081
D2: diode; SMS3923-081
D5: diode; SMS3923-081
D12: diode; SMS3923-081
D13: diode; SMS3923-081
D14: diode; SMS3923-081
D19: diode; 1N4148
D20: diode; 1N4148
I3: current; {-bias}
I4: current; {-bias}
L1: ind; 0.3n
L2: ind; 1n
L3: ind; 0.3n
L4: ind; 1n
L5: ind; 1n
L7: ind; 1n
L11: ind; 0.3n
L23: ind; 1n
L24: ind; 1n
L25: ind; 0.3n
L26: ind; 1n
L27: ind; 0.3n
L28: ind; 1n
L29: ind; 0.3n
L30: ind; 1n
L31: ind; 1n
L32: ind; 1n
Q6: pnp; BC807-40
Q7: pnp; BC807-40
Q8: npn; BC817-40
Q9: npn; BC817-40
R1: res; 15
R2: res; 3k9
R4: res; 18
R5: res; 33
R21: res; 82
R23: res; 100
R24: res; 100
R25: res; 56
R26: res; 10
R27: res; 10k
R28: res; 10k
R29: res; 15
R30: res; 50
R31: res; 10
R32: res; 180
R33: res; 30
R34: res; 1k
R35: res; 27
R36: res; 220
R37: res; 50
R39: res; 100k
R40: res; 6k8
R41: res; 100
R42: res; 3k9
R46: res; 22
R47: res; 200
U1: BFR460L3
U3: BF998
U4: BF998
V7: voltage; PULSE(0 400m 100p 35p 35p 5u 10u)
V8: voltage; 8.35
V9: voltage; ""; AC 1
V10: voltage; 2
V11: voltage; 5
V12: voltage; 1.65
Named nets: 0, Vbf, cap, bfout, sampin, bfin, norgnd
.model SMS3923-081 D(Is=5E-9 Rs=10 N=1.05 Tt=8E-11 Cj0=0.9p M=0.24 Eg=0.69 Xti=2 Fc=0.5 Bv=46 Ibv=1E-5 Vj=0.64)
;op
;tran 0 3n 0 1p
.SUBCKT BF998 1 2 3 4
        L10          1 10   L=0.12N
        L20          2 20   L=0.12N
        L30          3 30   L=0.12N
        L40          4 40   L=0.12N
        L11         10 11   L=1.20N
        L21         20 21   L=1.20N
        L31         30 31   L=1.20N
        L41         40 41   L=1.20N
        C13         10 30   C=0.085P
        C14         10 40   C=0.085P
        C21         10 20   C=0.017P
        C23         20 30   C=0.085P
        C24         20 40   C=0.005P
        D11         42 11   ZENER
        D12         42 41   ZENER
        D21         32 11   ZENER
        D22         32 31   ZENER
        RS          10 12   R=100
        MOS1        61 41 11 12 GATE1 L=1.1E-6 W=1150E-6
        MOS2        21 31 61 12 GATE2 L=2.0E-6 W=1150E-6
 
.MODEL  ZENER  D  BV=10 CJO=1.2E-12  RS=10
 
.MODEL  GATE1
+  NMOS LEVEL=3 UO=600  VTO=-0.250 NFS=300E9 TOX=42E-9
+  NSUB=3E15 VMAX=140E3 RS=2.0 RD=2.0 XJ=200E-9 THETA=0.11
+  ETA=0.06 KAPPA=2 LD=0.1E-6
+  CGSO=0.3E-9 CGDO=0.3E-9 CBD=0.5E-12 CBS=0.5E-12
 
.MODEL  GATE2 
+  NMOS LEVEL=3 UO=600  VTO=-0.250 NFS=300E9 TOX=42E-9
+  NSUB=3E15  VMAX=100E3 RS=2.0 RD=2.0 XJ=200E-9 THETA=0.11
+  ETA=0.06  KAPPA=2 LD=0.1E-6
+  CGSO=0.3E-9 CGDO=0.3E-9 CBD=0.5E-12 CBS=0.5E-12
 
.ENDS BF998
.SUBCKT BF998 1 2 3 4
        L10          1 10   0.12N
        L20          2 20   0.12N
        L30          3 30   0.12N
        L40          4 40   0.12N
        L11         10 11   1.20N
        L21         20 21   1.20N
        L31         30 31   1.20N
        L41         40 41   L=1.20N
        C13         10 30   0.085P
        C14         10 40   0.085P
        C23         20 30   0.085P
        C24         20 40   0.005P
        D11         42 11   ZENER
        D12         42 41   ZENER
        D21         32 11   ZENER
        D22         32 31   ZENER
        RS          10 12   100
        MOS1        61 41 11 12 GATE1 L=1.1E-6 W=1150E-6
        MOS2        21 31 61 12 GATE2 L=2.0E-6 W=1150E-6
 
.MODEL  ZENER  D  BV=10 CJO=1.2E-12  RS=10
 
.MODEL  GATE1
+  NMOS LEVEL=3 UO=600  VTO=-0.250 NFS=300E9 TOX=42E-9
+  NSUB=3E15 VMAX=140E3 RS=2.0 RD=2.0 XJ=200E-9 THETA=0.11
+  ETA=0.06 KAPPA=2 LD=0.1E-6
+  CGSO=0.3E-9 CGDO=0.3E-9 CBD=0.5E-12 CBS=0.5E-12
 
.MODEL  GATE2
+  NMOS LEVEL=3 UO=600  VTO=-0.250 NFS=300E9 TOX=42E-9
+  NSUB=3E15  VMAX=100E3 RS=2.0 RD=2.0 XJ=200E-9 THETA=0.11
+  ETA=0.06  KAPPA=2 LD=0.1E-6
+  CGSO=0.3E-9 CGDO=0.3E-9 CBD=0.5E-12 CBS=0.5E-12
 
*   BF998 SPICE MODEL OCTOBER 1993 PHILIPS SEMICONDUCTORS
*   ENVELOPE    SOT143 (R)
*   1.: SOURCE;  2.: DRAIN;  3.: GATE 2;  4.: GATE 1;
 
.ENDS BF998
.step param X list 3.3 4.7 6.8 8.2 10 12 15 18 20 22
.meas TRAN TOP FIND V(BF_source) AT=2n7
.meas TRAN BOT FIND V(BF_source) AT=0
.meas TRAN risetime TRIG V(BF_source)=BOT+(TOP-BOT)*0.1 TARG V(BF_source)=BOT+(TOP-BOT)*0.9
.meas PEAK MAX V(samplecap)
.ac dec 300 1Meg 10G
(V(n004)/I(R5)-50)/(V(n004)/I(R5)+50)
.MODEL BAT17_CHIP D(IS=3.33n N=1.009 RS=2.65 XTI=2.0 EG=0.69
+ CJO=398f M=0.21 VJ=0.224 FC=0.5 TT=3.0p BV=7.0 IBV=10.0u)
.param bias=-8m
;op
